NoBlackBoxes/LastBlackBox/boxes/magnets/README.md

# The Last Black Box : Magnets
In this box, you will learn about magnets...

<details><summary><i>Materials</i></summary><p>

Name|Description| # |Package|Data|Link|
:-------|:----------|:-----:|:-:|:--:|:--:|
Inductor|1 mH toroidal inductor|1|Passive Electronics|[-D-](/boxes/magnets/_resources/datasheets/inductor_toroidal.pdf)|[-L-](https://uk.farnell.com/bourns/2124-v-rc/inductor-1000uh-15-1-3a-toroid/dp/1929753)
Magnet Wire|Narrow gauge epoxy insulated (1 m)|1|Passive Electronics|[-D-](/boxes/magnets/)|[-L-](https://www.amazon.co.uk/sourcing-map-Enameled-Transformers-Inductors/dp/B0CYP8L4L1)
Magnet|Neodymium disc (8 mm x 3 mm)|4|Auxiliary|[-D-](/boxes/magnets/)|[-L-](https://uk.farnell.com/duratool/d01766/magnets-rare-earth-8-x-3mm-pk10/dp/1888095)
USB Sound Card|USB to 3.5 mm Audio out/in|1|Auxiliary|[-D-](/boxes/magnets/)|[-L-](https://www.amazon.co.uk/UGREEN-USB-C-3-5mm-Female-Adapter-dp-B08TR7LWQH/dp/B08TR7LWQH)
Stereo Plug Terminal|3.5 mm plug to screw terminal|2|Auxiliary|[-D-](/boxes/magnets/)|[-L-](https://www.amazon.co.uk/dp/B07MNYBFL9)

</p></details><hr>

## Magnets
#### Watch this video: [Ferromagnetism](https://vimeo.com/1031272573)
<p align="center">
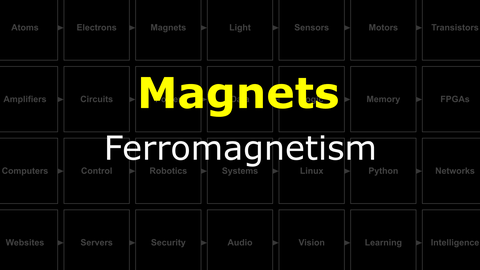
[picture p53: boxes/magnets/_resources/lessons/thumbnails/Ferromagnetism.gif]
Ferromagnetism

</p>

> A mysterious force found in certain types of "magical" materials, ferromagnetism was known about and used for thousands of years, but it was only understood quite recently.

#### Watch this video: [Electromagnets](https://vimeo.com/1031275874)
<p align="center">
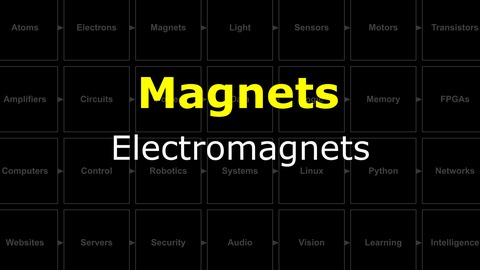
[picture p54: boxes/magnets/_resources/lessons/thumbnails/Electromagnets.gif]
Electromagnets

</p>

> When electrons move they create a (weak) magnetic field. With clever geometry we can make this field much, much stronger.

#### Watch this video: [Induction](https://vimeo.com/1031538232)
<p align="center">
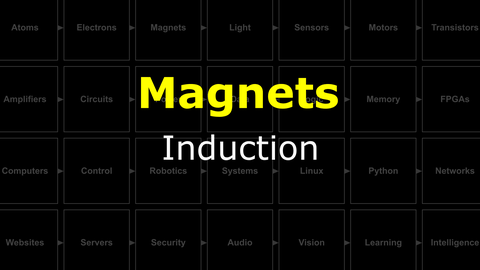
[picture p55: boxes/magnets/_resources/lessons/thumbnails/Induction.gif]
Induction

</p>

> A *changing* magnetic field **induces** an electromotive force on charged particles (and current in a complete conducting circuit). This electromagnetic induction is key to building time-dependent electronic circuits (such as filters) and generating the electricity we use in our homes.

# Projects
#### Watch this video: [NB3 : Building a Speaker](https://vimeo.com/1031277112)
<p align="center">
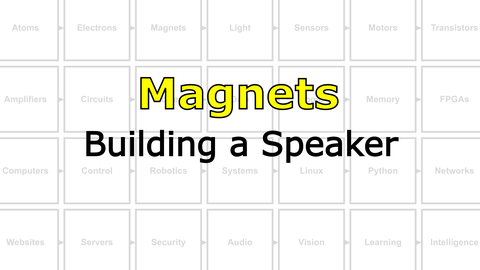
[picture p56: boxes/magnets/_resources/lessons/thumbnails/NB3_Building-a-Speaker.gif]
NB3 : Building a Speaker

</p>

> Oscillating current in a coil creates a dynamic magnetic field. Let's turn these oscillations into sound.
