NoBlackBoxes/LastBlackBox/boxes/motors/README.md

# The Last Black Box : Motors
In this box, you will learn about motors...

<details><summary><i>Materials</i></summary><p>

Name|Description| # |Package|Data|Link|
:-------|:----------|:-----:|:-:|:--:|:--:|
DC Brushed Motor|6V Brushed DC motor|1|Large (100)|[-D-](/boxes/motors/)|[-L-](https://www.amazon.co.uk/Gikfun-1V-6V-Hobby-Arduino-EK1894/dp/B07BHHP2BT)

</p></details><hr>

## Motors
#### Watch this video: [DC Motors](https://vimeo.com/1031627739)
<p align="center">
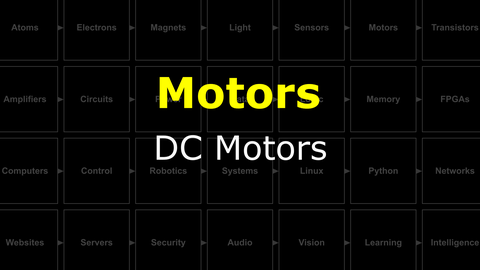
[picture p57: boxes/motors/_resources/lessons/thumbnails/DC-Motors.gif]
DC Motors

</p>

> An electric motor converts current into rotation using electromagnets that are turned on and off in a coordinated pattern. Different types of motors (stepper, brushed, or brushless) use different strategies (circuits) for this coordination.

- **TASK**: Play with your brushed DC motor. Spin it forwards *and* backwards...
    - *Challenge*: What are some ways you could change the *speed* with which your motor spins?
> Switching the direction that current flows through your motor will change the direction it spins.

# Projects
