NoBlackBoxes/LastBlackBox/boxes/sensors/README.md

# The Last Black Box : Sensors
In this box, you will learn about sensors...

<details><summary><i>Materials</i></summary><p>

Name|Description| # |Package|Data|Link|
:-------|:----------|:-----:|:-:|:--:|:--:|
Photoresistor (LDR)|Light-dependent resistor (GL5516 and GL5528)|2|Passive Electronics|[-D-](/boxes/sensors/)|[-L-](https://uk.farnell.com/advanced-photonix/nsl-19m51/light-dependent-resistor-550nm/dp/3168335)
Thermistor|Temperature sensitive resistor|1|Passive Electronics|[-D-](/boxes/sensors/_resources/datasheets/thermistor.pdf)|[-L-](https://uk.farnell.com/epcos/b57891m0103k000/thermistor-ntc-radial-leaded/dp/2285471)
Piezo|Piezo element|1|Passive Electronics|[-D-](/boxes/sensors/_resources/datasheets/piezo.pdf)|[-L-](https://uk.farnell.com/multicomp/mcabt-455-rc/audio-element-piezo-2-8khz-35mm/dp/2433035)

</p></details><hr>

## Sensors
#### Watch this video: [Transducers](https://vimeo.com/1031477896)
<p align="center">
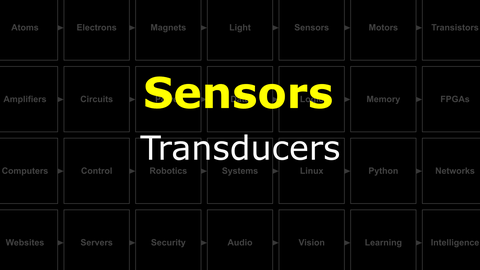
[picture p70: boxes/sensors/_resources/lessons/thumbnails/Transducers.gif]
Transducers

</p>

> A sensor converts (transduces) a physical quantity (light, heat, pressure, etc.) into an electrical signal (voltage, current, or resistance).

# Projects
#### Watch this video: [NB3 : Building a Light Sensor](https://vimeo.com/1031479533)
<p align="center">
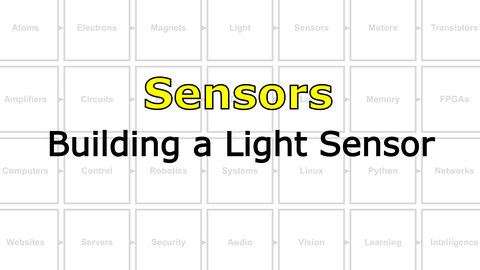
[picture p71: boxes/sensors/_resources/lessons/thumbnails/NB3_Building-a-Light-Sensor.gif]
NB3 : Building a Light Sensor

</p>

> Your NB3 will use LDRs to convert light into voltage. Here you will build and test this light sensing circuit.

- **TASK**: Build a light sensor
    - *Hint*: Build a voltage divider with one of the fixed resistors replaced with an LDR (light-dependent resistor). Does the "output" voltage vary with light level?
    - *Challenge*: What should the value of the fixed resistor be to maximize the sensitive range of the output voltage for varying light levels?
> Your multimeter should measure a change in voltage as you cover your LDR or shine light on it. The voltage will either increase with more light or decrease, depending on whether your LDR is the first or second resistor in the voltage divider circuit.

### NB3 : Sensory Systems
> What your NB3 "knows" about the world is up to you! Want touch sensitivity? temperature? You can add whatever you (and your robot) might like/need.
