NoBlackBoxes/LastBlackBox/boxes/transistors/README.md

# The Last Black Box : Transistors
In this box, you will learn about transistors...

<details><summary><i>Materials</i></summary><p>

Name|Description| # |Package|Data|Link|
:-------|:----------|:-----:|:-:|:--:|:--:|
MOSFET (5V)|Power MOSFET/N-channel (IRL510)|1|Active Electronics|[-D-](/boxes/transistors/_resources/datasheets/IRL510.pdf)|[-L-](https://uk.farnell.com/vishay/irl510pbf/mosfet-n-logic-to-220/dp/9102779)
Diode|IN4001|2|Active Electronics|[-D-](/boxes/transistors/_resources/datasheets/IN4001.pdf)|[-L-](https://uk.farnell.com/on-semiconductor/1n4001g/diode-standard-1a-do-41/dp/1458986)
LED (Red)|3 mm/2 mA red LED|2|Active Electronics|[-D-](/boxes/transistors/_resources/datasheets/led_HLMP.pdf)|[-L-](https://uk.farnell.com/broadcom-limited/hlmp-1700/led-3mm-red-2-1mcd-626nm/dp/1003207)
LED (Yellow)|3 mm/2 mA yellow LED|2|Active Electronics|[-D-](/boxes/transistors/_resources/datasheets/led_HLMP.pdf)|[-L-](https://uk.farnell.com/broadcom-limited/hlmp-1719/led-3mm-yellow-2-1mcd-585nm/dp/1003208)
LED (Green)|3 mm/2 mA green LED|2|Active Electronics|[-D-](/boxes/transistors/_resources/datasheets/led_HLMP.pdf)|[-L-](https://uk.farnell.com/broadcom-limited/hlmp-1790/led-3mm-green-2-3mcd-569nm/dp/1003209)
Resistor (470)|470 &Omega;/0.25 W|4|Passive Electronics|[-D-](/boxes/electrons/_resources/datasheets/resistor.pdf)|[-L-](https://uk.farnell.com/multicomp/mf25-470r/res-470r-1-250mw-axial-metal-film/dp/9341943)
Photodiode (Visible)|Visible (broadband) photodiode|2|Active Electronics|[-D-](/boxes/transistors/)|[-L-](https://uk.farnell.com/vishay/tefd4300/photodiode-950nm-3mm/dp/2251271)
Photodiode (IR)|IR sensitive photodiode|2|Active Electronics|[-D-](/boxes/transistors/)|[-L-](https://uk.farnell.com/osram-opto-semiconductors/sfh203-fa/photodiode-ir-filtered/dp/1212743)
LED (Blue)|Low power blue light emitting diode|2|Active Electronics|[-D-](/boxes/transistors/)|[-L-](https://uk.farnell.com/broadcom-limited/hlmp-ka45-e0000/led-3mm-blue-85mcd-470nm/dp/1863182)
LED (IR)|Low power IR light emitting diode|2|Active Electronics|[-D-](/boxes/transistors/)|[-L-](https://uk.farnell.com/vishay/tsal6100/infrared-emitter-940nm-t-1-3-4/dp/1328299)

</p></details><hr>

## Transistors
#### Watch this video: [Diodes](https://vimeo.com/1032443724)
<p align="center">
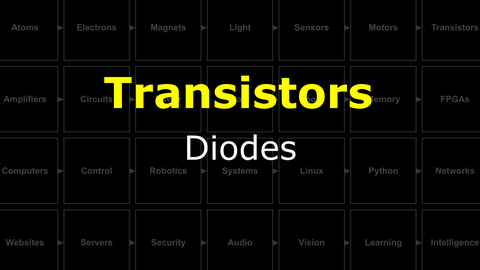
[picture p82: boxes/transistors/_resources/lessons/thumbnails/Diodes.gif]
Diodes

</p>

> The chemical and electrical equilibrium between charge carriers creates a potential across the PN junction. This junction potential only permits current flow in one direction, which gives **diodes** there delightfully non-linear behavior.

- **TASK**: Illuminate a light-emitting diode (LED). *Remember the current limiting resistor!*
> The LED should only illuminate when installed in one orientation. If you flip it around, then the "diode" of the LED will prevent current flowing through the circuit.

#### Watch this video: [Semiconductors](https://vimeo.com/1032460818)
<p align="center">
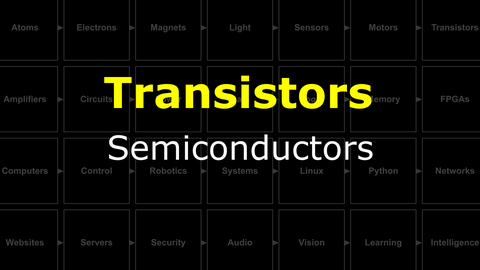
[picture p83: boxes/transistors/_resources/lessons/thumbnails/Semiconductors.gif]
Semiconductors

</p>

> We can modify a pure crystal of certain elements (e.g. silicon) to change how well they conduct electricity.

### Transistors (BJTs)
> Bipolar junction transistors inject charge carriers to amplify the external *current* flowing. They are current controlled devices.

#### Watch this video: [Transistors (MOSFETs)](https://vimeo.com/1032452466)
<p align="center">
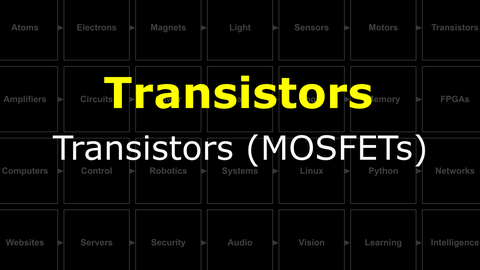
[picture p84: boxes/transistors/_resources/lessons/thumbnails/Transistors-MOSFETs.gif]
Transistors (MOSFETs)

</p>

> MOSFETs are the thing that humans have built more of than anything else. They must be useful! Let's discuss what they are and how they work.

- **TASK**: Measure the threshold voltage that opens your MOSFET gate. Compare it to the "expected" range listed in the
    - The datasheet for your MOSFET here [IRL510](/boxes/transistors/_resources/datasheets/IRL510.pdf)
> The threshold for when current starts to flow through your MOSFET ("Gate-Source Threshold Voltage") should be between 1 to 3 vols for the IRL510. However, the amount of current it allows will rise rapidly up to (and beyond) 5 Volts for the IRL510. Check the datasheet (Figure 3).

# Projects
#### Watch this video: [NB3 : Testing Diodes](https://vimeo.com/1032458879)
<p align="center">
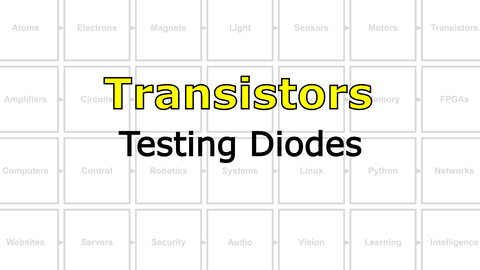
[picture p85: boxes/transistors/_resources/lessons/thumbnails/NB3_Testing-Diodes.gif]
NB3 : Testing Diodes

</p>

> Diodes allow current to flow in only one direction...if you overcome the internal junction potential. Let's measure this...and also use an LED to emit some light.

#### Watch this video: [NB3 : Building a Light-Sensitive Motor](https://vimeo.com/1032454998)
<p align="center">
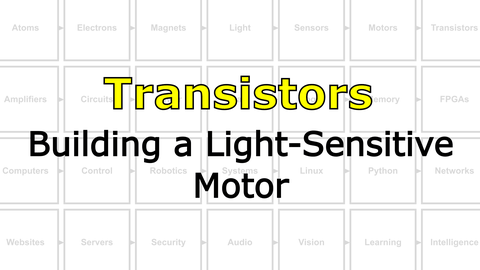
[picture p86: boxes/transistors/_resources/lessons/thumbnails/NB3_Building-a-Light-Sensitive-Motor.gif]
NB3 : Building a Light-Sensitive Motor

</p>

> Let's make something move in response to light!

- **TASK**: Use a MOSFET transistor to control how much current is flowing through your motor and gate the MOSFET with the output voltage from your light sensor...creating a motor that spins when the light is **ON** and stops when the light is **OFF**, or the other way around.
- *Hint*: Use the following circuit as a guide: [MOSFET driver:400](/boxes/transistors/_resources/images/MOSFET_motor_driver.png)
> Your motor should change how fast it spins when you change how much light hits the LDR.
