NoBlackBoxes/LastBlackBox/boxes/amplifiers/README.md

# The Last Black Box : Amplifiers
In this box, you will learn about amplifiers...

<details><summary><i>Materials</i></summary><p>

Name|Description| # |Package|Data|Link|
:-------|:----------|:-----:|:-:|:--:|:--:|
LM741|OpAmp|1|Active Electronics|[-D-](/boxes/amplifiers/_resources/datasheets/LM741.pdf)|[-L-](https://uk.farnell.com/texas-instruments/lm741cn-nopb/op-amp-single-pdip-8-0-to-70deg/dp/3117118)
LM386|Audio-Amp|2|Active Electronics|[-D-](/boxes/amplifiers/_resources/datasheets/LM386.pdf)|[-L-](https://uk.farnell.com/texas-instruments/lm386n-4-nopb/audio-power-amplifier-class-ab/dp/3116866)

</p></details><hr>

## Amplifiers
### Differential Amplifier
> Signals often have noise. However, this noise is often the same in many places around our circuit. What if we could reject (subtract out) this common noise? A differential amplifier allows us to selectively amplify the difference between a signal (with noise) and background (just noise). They are *very* useful.

### Op Amps
> Combine *high gain differential amplification* with *negative feedback* to build a much, much better amplifier. We call these devices **operational amplifiers** or **Op Amps**.

- Use an OpAmp to make your DIY speaker louder!

# Projects
