NoBlackBoxes/LastBlackBox/boxes/circuits/README.md

# The Last Black Box : Circuits
In this box, you will learn about circuits...

<details><summary><i>Materials</i></summary><p>

Name|Description| # |Package|Data|Link|
:-------|:----------|:-----:|:-:|:--:|:--:|

</p></details><hr>

## Circuits
### Radios
> Let's make some light, send it across the room, and decode it into a useful signal.

# Projects
