NoBlackBoxes/LastBlackBox/boxes/fpgas/README.md

# The Last Black Box : FPGAs
In this box, you will learn about fpgas...

<details><summary><i>Materials</i></summary><p>

Name|Description| # |Package|Data|Link|
:-------|:----------|:-----:|:-:|:--:|:--:|
NB3 Hindbrain|ICE40UP5K dev board with ADC/DAC|1|Circuit Boards|[-D-](/boxes/fpgas/NB3_hindbrain)|[-L-](VK)
Cable (MicroUSB-1m)|Micro-USB to Type-A cable (1 m)|1|Cables (001)|[-D-](/boxes/fpgas/)|[-L-](https://www.amazon.co.uk/gp/product/B07GBCKX49)
Cable (MicroUSB-20cm)|Short micro-USB to Type-A cable (20 cm)|1|Cables (001)|[-D-](/boxes/networks/)|[-L-](https://www.amazon.co.uk/gp/product/B07GBS2QZ1)

</p></details><hr>

## FPGAs
### Hardware Description Languages
> Describing hardware layouts is very different than describing software algorithms. Hardware description languages allow you to describe precisely what pieces of transistor logic you want. They come in many flavours, but the most popular are **Verilog** and **VHDL**.

# Projects
