NoBlackBoxes/LastBlackBox/course/tools/README.md

# course : tools
Tools to generate LBB designs, material lists, video lists, and run the README template engine
