NoBlackBoxes/LastBlackBox/boxes/ics/README.md

# FPGAs

Field-programmable-gate-arrays-are-awesome.

----

<details><summary><b>Materials</b></summary><p>

Contents|Description| # |Data|Link|
:-------|:----------|:-:|:--:|:--:|
UpDuino|ICE40UP5K dev board|1|[-D-](_data/datasheets/arduino_nano_rev3.pdf)|[-L-](https://uk.farnell.com/arduino/a000005/arduino-nano-evaluation-board/dp/1848691)
Cable (MiniUSB-1m)|Mini-USB to Type-A cable (1 m)|1|[-D-](_data/datasheets/mini_USB_cable_1m.pdf)|[-L-](https://uk.farnell.com/molex/88732-8602/usb-cable-2-0-plug-plug-1m/dp/1221071)
Piezo Buzzer|Piezoelectric speaker/buzzer|1|[-D-](_data/datasheets/piezo_speaker.pdf)|[-L-](https://uk.farnell.com/kingstate/kpeg110/piezo-transducer/dp/1193641)

</p></details>

----

## Goals

### Grey

1. Setup your FPGA dev board (run "blink" example).
2. Design a counter in HDL, synthesize, and test.
3. Design a 4-bit adder in HDL, synthesisze, and test.
4. Design a PWM controller in HDL, synthesisze, and test.

### White

1. Design a (RISC-V: rv32i) CPU

----

## NB3

This box will contribute the following (red) components to your NB3

<p align="center">
NB3 stage
<p>

----
