NoBlackBoxes/LastBlackBox/boxes/vision/image_processing/README.md

# Vision : Image Processing

This directory contains image processing examples and tools for computer vision tasks.

## Subdirectories

- **`python/`** - Python scripts for image processing (offline and online/streaming)
- **`picamera/`** - Information about using picamera2 library with libcamera

## Quick Start

**⚠️ Setup Required**: Before running the scripts, make sure you have activated your Python environment (or set one up). Follow the [Virtual Environment Setup Guide](../../python/virtual_environments/README.md) if needed.

### Python Dependencies

**Note**: Make sure you have activated the LBB virtual environment before installing packages:
```bash
source ~/NoBlackBoxes/LastBlackBox/_tmp/LBB/bin/activate
```

Then install the required packages:
```bash
pip install opencv-python
pip install numpy==1.26       # OpenCV is currently forcing numpy version >2 (which breaks other things)
```

### Camera Support

- **NB3/Raspberry Pi**: Uses picamera2 library (pre-installed on Raspberry Pi OS)
- **PC/Development**: Falls back to webcam support

See the individual subdirectory READMEs for detailed documentation:
- [`python/README.md`](python/README.md) - Python scripts documentation
- [`picamera/README.md`](picamera/README.md) - picamera2 information
