NoBlackBoxes/LastBlackBox/course/tools/videos/README.md

# course : tools : videos
Generate the LBB video list (with links), thumbnail frames, and GIF summary clips

## Normalize Audio
Use FFMPEG's loudnorm filter (via a Python wrapper: https://github.com/slhck/ffmpeg-normalize/tree/master)

```bash
# Requires an installation of FFMPEG
pip install ffmpeg-normalize

# Usage
ffmpeg-normalize -p -v -f -c:a aac -b:a 320k -t -16 --keep-loudness-range-target <filename.mkv>

# Detect volume levels
ffmpeg -filter:a ebur128 -map 0:a -f null - -i <filename.mkv>

## Integrated loudness should be around -16 LUFS
```
