NoBlackBoxes/LastBlackBox/boxes/electrons/kicad/README.md

# Electrons : KiCAD
KiCad is an open-course, highly capable, Python-based printed circuit board (PCB) design software

## JLC to KICAD
The following library coverts JLC/LCSC footprints/schematics/models into KiCAD footprints/schematics/models based on the part number.

```bash
pip install JLC2KiCadLib
```
