NoBlackBoxes/LastBlackBox/boxes/networks/sockets/README.md

# Python : Sockets
Instructions for developing socket-based network applications in Python.

## Setup
- Upload the "analog_stream" sketch to your Arduino
- Run the server on your NB3
- Run one of the clients (text, Matplotlib plotting (slow), OpenGL plotting (fast))
