NoBlackBoxes/LastBlackBox/boxes/vision/drone-NB3/README.md

# Vision : Drone NB3
Stream live camera images from the NB3 camera and provide web form input controls for driving the NB£ with a first-person view (FPV).
