NoBlackBoxes/LastBlackBox/boxes/light/equations/README.md

# Light : equations

Maxwell-Heaviside equations explained and demonstrated.

$$
\begin{align}
  \nabla \cdot  \vec{E} &= \frac{\rho} {\epsilon_0} \nonumber \\
  \nabla \cdot  \vec{B} &= 0 \nonumber \\
  \nabla \times \vec{E} &= - \frac{\partial \vec{B}}{\partial t} \nonumber \\
  \nabla \times \vec{B} &= \mu_0 ( \vec{j} + \frac{\partial \vec{E}}{\partial t} ) \nonumber \\
\end{align}
$$

---

## Gauss's Law for Electricity
$$
\begin{align}
  \nabla \cdot \vec{E} &= \frac{\rho} {\epsilon_0} \nonumber \\
\end{align}
$$

The electric field points towards negative charges and away from positive charges.  $\rho$ is charge density and $\epsilon_0$ is the permitivity of free space.

## Gauss's Law for Magnetisim
$$
\begin{align}
  \nabla \cdot  \vec{B} &= 0 \nonumber \\
\end{align}
$$

There are no magnetic dipoles (i.e. no net inward or outward magentic field lines).

## Faraday's Law of Induction
$$
\begin{align}
  \nabla \times \vec{E} &= - \frac{\partial \vec{B}}{\partial t} \nonumber \\
\end{align}
$$

Induced electric field (also EMF) is related to the rate of change of a magentic field.

## Ampere's Law
$$
\begin{align}
  \nabla \times \vec{B} &= \mu_0 ( \vec{j} + \frac{\partial \vec{E}}{\partial t} ) \nonumber \\
\end{align}
$$

Induced magnetic field is related to the rate of change of an electric field field + current density $\vec(j)$ scaled by $\mu_0$, the permeability of free space. (hmm....more to this...)
