NoBlackBoxes/LastBlackBox/boxes/servers/node/README.md

# Servers : Node

There is a lot to say about Node.js, but not yet. This section is currently only used to introduce the framework for developing a VSCode extension.
