NoBlackBoxes/LastBlackBox/course/versions/crick/01_electronics-and-sensors/README.md

# Crick : Electronics and Sensors
Day one of the NB3 build is entirely analog - no microcontroller, no software, no code. By the end of the session you will have built a working light sensor (LDR voltage divider), a hand-wound electromagnetic speaker, and a fully analog light-sensitive motor with a MOSFET as the only computational element.

<details><summary><i>Materials</i></summary><p>

Name|Description| # |Package|Data|Link|
:-------|:----------|:-----:|:-:|:--:|:--:|
Periodic Table|Periodic Table Card|1|Body (000)|[-D-](/boxes/atoms/card)|[-L-](VK)
NB3 Body|NB3 robot base PCB|1|Body (000)|[-D-](/boxes/electrons/NB3_body)|[-L-](VK)
Resistor (470)|470 &Omega;/0.25 W|2|Passive Electronics|[-D-](/boxes/electrons/_resources/datasheets/resistor.pdf)|[-L-](https://uk.farnell.com/multicomp/mf25-470r/res-470r-1-250mw-axial-metal-film/dp/9341943)
Resistor (1k)|1 k&Omega;/0.25 W|2|Passive Electronics|[-D-](/boxes/electrons/_resources/datasheets/resistor.pdf)|[-L-](https://uk.farnell.com/multicomp/mf25-1k/res-1k-1-250mw-axial-metal-film/dp/9341102)
Resistor (10k)|10 k&Omega;/0.25 W|2|Passive Electronics|[-D-](/boxes/electrons/_resources/datasheets/resistor.pdf)|[-L-](https://uk.farnell.com/multicomp/mf25-10k/res-10k-1-250mw-axial-metal-film/dp/9341110)
Button|Tactile switch|2|Passive Electronics|[-D-](/boxes/electrons/_resources/datasheets/button.pdf)|[-L-](https://uk.farnell.com/omron/b3f-1000/switch-spno-0-05a-24v-tht-0-98n/dp/176432)
Potentiometer|2.2 k&Omega; variable resistor|2|Passive Electronics|[-D-](/boxes/electrons/_resources/datasheets/pot_2k2.pdf)|[-L-](https://uk.farnell.com/bourns/3362p-1-222lf/trimmer-pot-2-2kohm-10-1turn-th/dp/2328599)
Breadboard (400)|400-tie solderless breadboard|1|Small (010)|[-D-](/boxes/electrons/_resources/datasheets/breadboard_400.pdf)|[-L-](https://www.amazon.co.uk/gp/product/B0739XRX8F)
Breadboards (170)|170-tie solderless breadboard|4|Small (010)|[-D-](/boxes/electrons/_resources/datasheets/breadboard_170.pdf)|[-L-](https://www.amazon.co.uk/ELEGOO-tie-points-Breadboard-Breadboards-Electronic/dp/B01N0YWIR7)
Batteries (AA)|AA 1.5 V alkaline battery|4|Auxiliary|[-D-](/boxes/electrons/)|[-L-](https://www.amazon.co.uk/Duracell-Optimum-Alkaline-Batteries-MX1500/dp/B093Q5XY66)
Battery holder|4xAA battery holder with ON-OFF switch|1|Small (010)|[-D-](/boxes/electrons/)|[-L-](https://www.amazon.co.uk/gp/product/B0814ZH68F)
Jumper Kit|Kit of multi-length 22 AWG breadboard jumpers|1|Large (100)|[-D-](/boxes/electrons/_resources/datasheets/jumper_kit.pdf)|[-L-](https://uk.farnell.com/multicomp/mc001810/hard-jumper-wire-22awg-140pc/dp/2770338)
Jumper Wires|Assorted 22 AWG jumper wire leads (male/female)|1|Cables (001)|[-D-](/boxes/electrons/_resources/datasheets/jumper_wires.pdf)|[-L-](https://www.amazon.co.uk/gp/product/B09KR7Z4PF)
Test Lead|Alligator clip to 0.64 mm pin (20 cm)|2|Cables (001)|[-D-](/boxes/electrons/)|[-L-](https://www.amazon.co.uk/gp/product/B096JR15JW)
Rubber feet|Adhesive rubber standoffs (1421T6CL)|4|Passive Electronics|[-D-](/boxes/electrons/_resources/datasheets/rubber_feet.pdf)|[-L-](https://uk.farnell.com/hammond/1421t6cl/feet-stick-on-pk24/dp/1876522)
Photoresistor (LDR)|Light-dependent resistor (GL5516 and GL5528)|2|Passive Electronics|[-D-](/boxes/sensors/)|[-L-](https://uk.farnell.com/advanced-photonix/nsl-19m51/light-dependent-resistor-550nm/dp/3168335)
DC Brushed Motor|6V Brushed DC motor|1|Large (100)|[-D-](/boxes/motors/)|[-L-](https://www.amazon.co.uk/Gikfun-1V-6V-Hobby-Arduino-EK1894/dp/B07BHHP2BT)
MOSFET (5V)|Power MOSFET/N-channel (IRL510)|1|Active Electronics|[-D-](/boxes/transistors/_resources/datasheets/IRL510.pdf)|[-L-](https://uk.farnell.com/vishay/irl510pbf/mosfet-n-logic-to-220/dp/9102779)
Diode|IN4001|2|Active Electronics|[-D-](/boxes/transistors/_resources/datasheets/IN4001.pdf)|[-L-](https://uk.farnell.com/on-semiconductor/1n4001g/diode-standard-1a-do-41/dp/1458986)
LED (Red)|3 mm/2 mA red LED|2|Active Electronics|[-D-](/boxes/transistors/_resources/datasheets/led_HLMP.pdf)|[-L-](https://uk.farnell.com/broadcom-limited/hlmp-1700/led-3mm-red-2-1mcd-626nm/dp/1003207)
LED (Yellow)|3 mm/2 mA yellow LED|2|Active Electronics|[-D-](/boxes/transistors/_resources/datasheets/led_HLMP.pdf)|[-L-](https://uk.farnell.com/broadcom-limited/hlmp-1719/led-3mm-yellow-2-1mcd-585nm/dp/1003208)
LED (Green)|3 mm/2 mA green LED|2|Active Electronics|[-D-](/boxes/transistors/_resources/datasheets/led_HLMP.pdf)|[-L-](https://uk.farnell.com/broadcom-limited/hlmp-1790/led-3mm-green-2-3mcd-569nm/dp/1003209)
Resistor (470)|470 &Omega;/0.25 W|4|Passive Electronics|[-D-](/boxes/electrons/_resources/datasheets/resistor.pdf)|[-L-](https://uk.farnell.com/multicomp/mf25-470r/res-470r-1-250mw-axial-metal-film/dp/9341943)
Magnet Wire|Narrow gauge epoxy insulated (1 m)|1|Passive Electronics|[-D-](/boxes/magnets/)|[-L-](https://www.amazon.co.uk/sourcing-map-Enameled-Transformers-Inductors/dp/B0CYP8L4L1)
Magnet|Neodymium disc (8 mm x 3 mm)|4|Auxiliary|[-D-](/boxes/magnets/)|[-L-](https://uk.farnell.com/duratool/d01766/magnets-rare-earth-8-x-3mm-pk10/dp/1888095)
USB Sound Card|USB to 3.5 mm Audio out/in|1|Auxiliary|[-D-](/boxes/magnets/)|[-L-](https://www.amazon.co.uk/UGREEN-USB-C-3-5mm-Female-Adapter-dp-B08TR7LWQH/dp/B08TR7LWQH)
Stereo Plug Terminal|3.5 mm plug to screw terminal|2|Auxiliary|[-D-](/boxes/magnets/)|[-L-](https://www.amazon.co.uk/dp/B07MNYBFL9)

</p></details><hr>

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

## Voltage, current, resistance
#### Watch this video: [Voltage](https://vimeo.com/1000730032)
<p align="center">
<a href="https://vimeo.com/1000730032" title="Control+Click to watch in new tab">Voltage</a>
</p>

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

## Building circuits
#### Watch this video: [NB3 : Body](https://vimeo.com/1030776673)
<p align="center">
<a href="https://vimeo.com/1030776673" title="Control+Click to watch in new tab">NB3 : Body</a>
</p>

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

## Voltage dividers and transduction
#### Watch this video: [Voltage Dividers](https://vimeo.com/1030787469)
<p align="center">
<a href="https://vimeo.com/1030787469" title="Control+Click to watch in new tab">Voltage Dividers</a>
</p>

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

> Step-by-step guide to building and testing voltage dividers with discrete resistors and a potentiometer.

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

## Semiconductors and the MOSFET
#### Watch this video: [Semiconductors](https://vimeo.com/1032460818)
<p align="center">
<a href="https://vimeo.com/1032460818" title="Control+Click to watch in new tab">Semiconductors</a>
</p>

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

# Project
#### Watch this video: [NB3 : Building a Speaker](https://vimeo.com/1031277112)
<p align="center">
<a href="https://vimeo.com/1031277112" title="Control+Click to watch in new tab">NB3 : Building a Speaker</a>
</p>

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

> Let's make something move in response to light!

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
