NoBlackBoxes/LastBlackBox/course/versions/bootcamp/08_signal-processing/README.md

# Bootcamp : Signal Processing
Let's learn how to process one-dimensional time series data...like audio waveforms.

<details><summary><i>Materials</i></summary><p>

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

</p></details><hr>

## Audio
We will continue our explanation of sound measurement and generation by exploring "signal processing" in Python.
#### Watch this video: [Signal Processing](https://vimeo.com/manage/videos/1139975157)
<p align="center">
<a href="https://vimeo.com/manage/videos/1139975157" title="Control+Click to watch in new tab">Signal Processing</a>
</p>

> One-dimensional (1D) signals are common in the world. They often arise as time series (a sequence of measurements made at a regular "sample rate"). Here we will explore techniques to process a common 1D signal...**sound**. We will both measure and generate different sounds. We will develop tools in Python to compare their amplitude (volume), frequency content, and visualize the "spectrogram" of different spoken words (e.g. "Go" vs "Stop").

- Explore, test, and expand upon these Python examples for processing signals measured from the NB3's microphones (ears): [Measurement](/boxes/audio/signal-processing/python/measurement/)
    - Stream the live frequency spectrum from your NB3 to your PC.
        - Run the [server](/boxes/audio/signal-processing/python/measurement/03_stream_frequency.py) on your NB3 (via SSH)
        - Run the [client](/boxes/audio/signal-processing/python/measurement/clients/live_plot_frequency_client_pyglet.py) on your PC (in a separate VS Code window)
- Explore, test, and expand upon these Python examples for processing signals generated and output to the NB3's speaker (mouth): [Generation](/boxes/audio/signal-processing/python/generation/)
    - *Note*: For text-to-speech synthesis you will need to install the Linux espeak package:
- *code*
```bash
sudo apt install espeak-ng
```

# Project
You should now have all the skills required to make your NB3 "respond" to sound!
  - This could be as simple as detecting a loud ***clap*** and turning on an LED.
  - You could tell NB3 to turn left or right based on the most prominent frequency measured by its ears.
  - Respond to commands, like "Go" and "Stop"...tricky...but doable.
    - *Note*: We will revisit this when we start learning about learning.
