NoBlackBoxes/LastBlackBox/course/_resources/videos/list.md

## Atoms
- [x] [The Periodic Table](https://vimeo.com/1028399080)
- [ ] [Chemistry]()
- [ ] [Nuclear Forces]()
- [x] [Heat](https://vimeo.com/1029691491)
- [x] [Atomic Structure](https://vimeo.com/1000458082)
- [ ] [Fission and Fusion]()

## Electrons
- [x] [NB3 : Multimeter Basics](https://vimeo.com/1027764019)
- [x] [Voltage Dividers](https://vimeo.com/1030787469)
- [x] [NB3 : Body](https://vimeo.com/1030776673)
- [ ] [NB3 : Designing PCBs With KiCAD]()
- [x] [NB3 : Measuring Resistance](https://vimeo.com/1027761453)
- [x] [NB3 : Building Circuits](https://vimeo.com/1030783826)
- [x] [NB3 : Building Voltage Dividers](https://vimeo.com/1030790826)
- [x] [Electric Fields](https://vimeo.com/1032441712)
- [x] [Capacitors](https://vimeo.com/1035298931)
- [x] [Resistors](https://vimeo.com/1029696806)
- [x] [NB3 : Measuring Current](https://vimeo.com/1027757287)
- [x] [Current](https://vimeo.com/1029334167/2492ff3542)
- [x] [Ohm's Law](https://vimeo.com/1029695302)
- [ ] [NB3 : How Do Multimeters Work]()
- [x] [Power](https://vimeo.com/1029693122)
- [x] [NB3 : Measuring Voltage](https://vimeo.com/1027762531)
- [x] [Batteries](https://vimeo.com/1029278169)
- [x] [NB3 : Building a Battery](https://vimeo.com/1029280971)
- [x] [Conductors](https://vimeo.com/1029337222)
- [x] [Voltage](https://vimeo.com/1000730032)

## Magnets
- [x] [NB3 : Building a Speaker](https://vimeo.com/1031277112)
- [x] [Ferromagnetism](https://vimeo.com/1031272573)
- [x] [Electromagnets](https://vimeo.com/1031275874)
- [x] [Induction](https://vimeo.com/1031538232)

## Light
- [ ] [The EM Spectrum]()
- [ ] [Optics]()
- [ ] [Maxwell's Equations]()
- [x] [Electromagnetic Radiation](https://vimeo.com/1032447600)

## Sensors
- [x] [Transducers](https://vimeo.com/1031477896)
- [ ] [NB3 : Sensory Systems]()
- [x] [NB3 : Building a Light Sensor](https://vimeo.com/1031479533)

## Motors
- [x] [DC Motors](https://vimeo.com/1031627739)

## Transistors
- [ ] [Transistors (BJTs)]()
- [x] [Diodes](https://vimeo.com/1032443724)
- [x] [Semiconductors](https://vimeo.com/1032460818)
- [x] [NB3 : Building a Light-Sensitive Motor](https://vimeo.com/1032454998)
- [x] [Transistors (MOSFETs)](https://vimeo.com/1032452466)
- [x] [NB3 : Testing Diodes](https://vimeo.com/1032458879)

## Amplifiers
- [ ] [Differential Amplifier]()
- [ ] [Op Amps]()

## Circuits
- [ ] [Radios]()

## Data
- [x] [Analog to Digital Converters](https://vimeo.com/1033223967)
- [x] [Binary Numbers](https://vimeo.com/1033226788)
- [x] [NB3 : Build an ADC (input)](https://vimeo.com/1034767170)

## Logic
- [x] [Logic Gates](https://vimeo.com/1033231995)
- [ ] [NB3 : Build an ADC (output)]()

## Memory
- [x] [Flash Memory](https://vimeo.com/1033230293)
- [x] [NB3 : Building an SR Latch](https://vimeo.com/1033234541)
- [ ] [Flip Flop]()
- [x] [SR Latch](https://vimeo.com/1033238234)

## FPGAs
- [ ] [Hardware Description Languages]()

## Computers
- [x] [Architecture](https://vimeo.com/1033601146)
- [x] [NB3 : Hindbrain](https://vimeo.com/1033609727)
- [ ] [Low-Level Programming]()
- [x] [NB3 : Building a Theremin](https://vimeo.com/1033896646)
- [x] [NB3 : Programming Arduino](https://vimeo.com/1033810807)

## Control
- [x] [PWM](https://vimeo.com/1033905955)
- [x] [Servo Loops](https://vimeo.com/1033963709)
- [x] [NB3 : Building a PWM Speed Controller](https://vimeo.com/1033891821)
- [x] [H-Bridges](https://vimeo.com/1034209519)

## Robotics
- [ ] [NB3 : Muscles (DC Gear Motors)]()
- [ ] [Reflexes]()
- [x] [NB3 : Muscles (Servos)](https://vimeo.com/1034800702)
- [x] [NB3 : Build a Braitenberg Vehicle](https://vimeo.com/1034798460)
- [x] [NB3 : Ball Caster](https://vimeo.com/1034797327)

## Power
- [x] [NB3 : Power Supply](https://vimeo.com/1035306761)
- [x] [NB3 : Battery Pack](https://vimeo.com/1042781111)
- [x] [DC-DC Converters](https://vimeo.com/1035304311)

## Systems
- [x] [NB3 : Programming Concurrency (Arduino)](https://vimeo.com/1036094397)
- [x] [Operating Systems](https://vimeo.com/1036096746)
- [x] [NB3 : Connecting to RPi](https://vimeo.com/1036391512)
- [x] [NB3 : Midbrain](https://vimeo.com/1036089510)
- [x] [Visual Studio Code](https://vimeo.com/1036716612)
- [x] [Multi-Tasking](https://vimeo.com/1036086160)
- [x] [NB3 : RPiOS](https://vimeo.com/1036095710)

## Linux
- [x] [Package Managers](https://vimeo.com/1036834036)
- [x] [Navigating the Command Line](https://vimeo.com/1036829527)
- [x] [Git](https://vimeo.com/1036825331)

## Python
- [x] [Virtual Environments](https://vimeo.com/1042637566)
- [x] [Introducing the Interpreter](https://vimeo.com/1042618092)
- [ ] [NB3 : Playing With Python]()

## Networks
- [x] [NB3 : Remote Control NB3 (TUI)](https://vimeo.com/1042784651)
- [x] [Sockets](https://vimeo.com/1134201413)
- [x] [Architectures](https://vimeo.com/manage/videos/1127222969)
- [x] [Physical Layers](https://vimeo.com/1127178041)
- [x] [NB3 : Develop a Protocol](https://vimeo.com/1042782602)

## Websites
- [x] [Javascript](https://vimeo.com/1134729863)
- [x] [HTML](https://vimeo.com/1134724080)
- [x] [CSS](https://vimeo.com/1134720724)

## Servers
- [x] [NB3 : Remote Control NB3 (GUI)](https://vimeo.com/1135870296)
- [x] [NB3 : Host a Website](https://vimeo.com/1135859914)
- [x] [HTTP](https://vimeo.com/1135853103)

## Security
- [ ] [One Way Functions]()

## Audio
- [x] [NB3 : Install the Mouth](https://vimeo.com/1042947561)
- [x] [NB3 : Install the Ears](https://vimeo.com/1042943195)
- [x] [NB3 : Build and Install the Linux I2S Driver](https://vimeo.com/1042781850)
- [x] [Microphones, Speakers, and I2S](https://vimeo.com/1136576333)
- [x] [Signal Processing](https://vimeo.com/manage/videos/1139975157)

## Vision
- [x] [NB3 : Streaming Images](https://vimeo.com/manage/videos/1141582696)
- [x] [Light, Cameras, Noise](https://vimeo.com/manage/videos/1141367902)
- [x] [Image-Processing](https://vimeo.com/manage/videos/1144050570)
- [x] [NB3 : Install the Eye](https://vimeo.com/1042945461)

## Learning
- [ ] [NB3 : Clicker Training]()
- [ ] [Gradient Descent]()

## Intelligence
- [ ] [Large Language Models]()
- [x] [NB3 : Install the Forebrain (NPU)](https://vimeo.com/1043159124)
- [ ] [NB3 : Install the Skull]()
