NoBlackBoxes/LastBlackBox/boxes/circuits/_resources/info.md

## Description
Analog circuits can do some amazing things. Here we will build a radio (receiver and transmitter).
