NoBlackBoxes/LastBlackBox/boxes/power/_resources/info.md

## Description
Running more capable software requires a faster computer, which requires more electrical power. We will now explore how power supplies work and then install one on your NB3.
