NoBlackBoxes/LastBlackBox/boxes/control/_resources/info.md

## Description
Getting a motor to move precisely how you want it to (direction and speed) is very important for *controlling* the behaviour of your robot. A number of very clever strategies have been developed to help you take **control** of your motor.
