NoBlackBoxes/LastBlackBox/boxes/robotics/_resources/info.md

## Description
Combining sensors, motors, and a "brain" in between.
