NoBlackBoxes/LastBlackBox/boxes/amplifiers/_resources/info.md

## Description
The signals arriving from the environment are often too small to measure reliably with a computer (or brain). We need to make them bigger. Making tiny voltage or current signals larger is called *amplification*, and the things that can do this are ***amplifiers***.
