NoBlackBoxes/LastBlackBox/boxes/data/_resources/info.md

## Description
What is a data...for computers? for brains? How can machines decide what to do based on their inputs? A key concept in decision-making is threshold functions. If an input value goes above a threshold, a decision is triggered. How can we make such a trigger out of electronic circuit elements?
