NoBlackBoxes/LastBlackBox/boxes/electrons/_resources/info.md

## Description
Electrons are the sub-atomic particles that underlie *electricity*. Controlling the movement of electrons (and the effects of that movement) will allow us to build many different kinds of electronic devices, from simple circuits to robots and computers.
