NoBlackBoxes/LastBlackBox/boxes/magnets/_resources/info.md

## Description
Magnets were known about (and useful) long before we understood electricity. However, the connection between electricity and magnetism is one of the most important discoveries of science. It has major implications for your everyday life (and your NB3).
