NoBlackBoxes/LastBlackBox/boxes/motors/_resources/info.md

## Description
Clever arrangements of electromagnets and their control circuits can be used to produce a rotational force. You will use these devices to make your NB3 move!
