NoBlackBoxes/LastBlackBox/boxes/transistors/_resources/info.md

## Description
Semiconductors are materials that can both conduct and resist the flow of electrons. You can arrange them such that the conduction of (lots of) electricity can be controlled by a (tiny) external signal. These devices are call **transistors**.
