NoBlackBoxes/LastBlackBox/boxes/vision/_resources/lessons/NB3_Streaming-Images.md

# Vision : NB3 : Streaming Images
Let's stream live images from your NB3's camera to any web browser.

## [Video](https://vimeo.com/manage/videos/1141582696)

## Concepts

## Lesson
