NoBlackBoxes/LastBlackBox/boxes/logic/_resources/lessons/Logic-Gates.md

# Logic : Logic Gates
The essential elements of computation (NOT, AND, OR, XOR, etc.) can be built from straight forward combinations of MOSFETs.

## [Video](https://vimeo.com/1033231995)

## Concepts
- MOSFETs make it easy.
- Inverter
- NAND (and AND)
- NOR
- Addition
- XOR?

## Lesson
- Design an XOR gate
- Build an addition circuit (2-bit adder)
- Build a priority encoder for your 2-bit ADC
