NoBlackBoxes/LastBlackBox/boxes/vision/_resources/lessons/Cameras.md

# Vision : Cameras
From CCDs to CMOS.

## [Video]()

## Concepts

## Lesson
