NoBlackBoxes/LastBlackBox/boxes/networks/_resources/lessons/Physical-Layers.md

# Networks : Physical Layers
Connections must be made between computers in order for them to communicate. These can be wires carrying electrical signals (from just one or two wires for serial connections to many wires for parallel connections) or wireless (most often using light, i.e. radio waves). This is the physical layer of the network...and a message may traverse many different types of physical connections on its path from the sender to the receiver.

## [Video](https://vimeo.com/1127178041)

## Concepts
 - serial connections (simplex/duplex?, synchronous (with clock, e.g. SPI (with chip select...master/slave)) or asynchronous (UART, Rx/Tx, frames), baud-rate (BPS))
 - twisted-pair, deal with noise - differential signalling
 - Ethernet (four twisted-pairs: RJ45)
 - WiFi

## Lesson
