NoBlackBoxes/LastBlackBox/boxes/systems/_resources/lessons/NB3_Midbrain.md

# Systems : NB3 : Midbrain
Now we will add a more powerful computer (Raspberry Pi) to your NB3's midbrain.

## [Video](https://vimeo.com/1036089510)

## Concepts
- Overview of Pi SoC
- Overview of Pi board layout
- Mount Midbrain
- Attach heatsinks

## Lesson

- **TASK**: Mount a Raspberry Pi on your robot (and connect its power inputs using your *shortest* jumper cables, 2x5V and 2x0V from the NB3, to the correct GPIO pins on the RPi...please *double-check* the pin numbers)
    - This pinout of the Raspberry Pi GPIO might be useful: [Raspberry Pi GPIO](/boxes/systems/_resources/images/rpi_GPIO_pinout.png)
> A powered and blinking RPi midbrain.
