NoBlackBoxes/LastBlackBox/boxes/systems/_resources/lessons/Visual-Studio-Code.md

# Systems : Visual Studio Code
We will be using Visual Studio Code (VS Code) as our tool for writing programs. VS Code is just a simple, *but really powerful*, text editor. It has extensions for all sorts of useful tools (Python, Git, etc.), and for connecting to a "remote" computer (our NB3's midbrain).

## [Video](https://vimeo.com/1036716612)

## Concepts
- Managing complex, powerful systems requires more complex, powerful tools
- Fortunately, the basics are pretty standardized: Run commands, browse folders, and edit files
- VS Code, simple, but extensible (runs in a browser framework  electron, based on Chrome)
- Overview: Terminal, Explorer, Editor, and Search
- Workflow: Open a project folder
- Extensions
- Remote-SSH

## Lesson
