NoBlackBoxes/LastBlackBox/boxes/power/_resources/lessons/DC-DC-Converters.md

# Power : DC-DC Converters
How does efficient DC to DC conversion work? Buck and Boost.

## [Video](https://vimeo.com/1035304311)

## Concepts
- A voltage divider is a bad (inefficient) idea
- Switching regulators are more efficient.
- Must filter out switching noise (ripple)
- Buck vs Boost
- Synchronous Buck (no diode)

## Lesson
