NoBlackBoxes/LastBlackBox/boxes/power/_resources/lessons/NB3_Battery-Pack.md

# Power : NB3 : Battery Pack
Let's install a rechargeable NiMH battery pack on our NB3.

## [Video](https://vimeo.com/1042781111)

## Concepts
- Add velcro mount
- Add battery pack
- Test

## Lesson

- **TASK**: Add a NiMH rechargeable 9.6 volt battery pack to your NB3.
> You should now be able to power and control your NB3 autonomously (without any cables).
