NoBlackBoxes/LastBlackBox/boxes/robotics/_resources/lessons/NB3_Ball-Caster.md

# Robotics : NB3 : Ball Caster
Let's add a front wheel (ball caster) to keep your NB3 from dragging its face on the ground.

## [Video](https://vimeo.com/1034797327)

## Concepts
- Add ball caster
- Choose spacer count (angle of attack)

## Lesson

- **TASK**: Mount caster (ball bearing) to the front of your NB3.
> The ball caster mount should look like this.
