NoBlackBoxes/LastBlackBox/boxes/robotics/_resources/lessons/Reflexes.md

# Robotics : Reflexes
Simple sensory-motor loops that underlie essential behaviour.

## [Video]()

## Concepts

## Lesson
