NoBlackBoxes/LastBlackBox/boxes/control/_resources/lessons/Servo-Loops.md

# Control : Servo Loops
A servo loop connects feedback from a sensor to the control signals sent to a motor.

## [Video](https://vimeo.com/1033963709)

## Concepts
- Feedback
- Demo hobby servo (position) and continuous rotation (speed?)
- PID
- Dissection

## Lesson
