NoBlackBoxes/LastBlackBox/boxes/amplifiers/_resources/lessons/Op-Amps.md

# Amplifiers : Op Amps
Combine *high gain differential amplification* with *negative feedback* to build a much, much better amplifier. We call these devices **operational amplifiers** or **Op Amps**.

## [Video]()

## Concepts
- Differential amplification
- Gain
- (Negative) feedback
- The *ideal* op amp

## Lesson

- Use an OpAmp to make your DIY speaker louder!
