NoBlackBoxes/LastBlackBox/boxes/electrons/_resources/lessons/NB3_Measuring-Current.md

# Electrons : NB3 : Measuring Current
How to measure current with a digital multimeter.

## [Video](https://vimeo.com/1027757287)

## Concepts
- Current is the trickiest of the basic electronic values to measure
- The current must flow *through* the meter. Therefore, you must measure in series.
- **Warning**: Do ***NOT*** try to measure the current coming out of your batteries directly...it will blow your fuse.

## Lesson
