NoBlackBoxes/LastBlackBox/boxes/electrons/_resources/lessons/NB3_Measuring-Resistance.md

# Electrons : NB3 : Measuring Resistance
How to measure resistance with a digital multimeter.

## [Video](https://vimeo.com/1027761453)

## Concepts
- Resistance between two points
- Must pass current from the multimeter through the resistor being measured
- Normally necessary to remove the resistor from the circuit (but there are some exceptions, e.g. an un-powered simple circuit).

## Lesson
