NoBlackBoxes/LastBlackBox/boxes/electrons/_resources/lessons/NB3_Multimeter-Basics.md

# Electrons : NB3 : Multimeter Basics
An overview of digital multimeters for beginners. What can it measure? What features do you need to complete the course?

## [Video](https://vimeo.com/1027764019)

## Concepts
- What is a multimeter? (electrical measurements)
- What types of multimeters? (cheap vs. expensive, analog vs. digital)
- Types of measurements (voltage, resistance, current, and more)
- Probes
- Fuses (over current protection)
- Auto-ranging vs. manual range
- Other features (light, hold)

## Lesson
