NoBlackBoxes/LastBlackBox/boxes/electrons/_resources/lessons/Voltage.md

# Electrons : Voltage
When there is more negative or positive charge in one location vs. another there is a *potential difference* between these locations. This *potential difference* is called a **voltage** and it creates a pressure that pushes electrons from the location with more negative charge to the location with less.

## [Video](https://vimeo.com/1000730032)

## Concepts
- Most materials are electrically neutral
- Static electricity
- Differences in charge concentration create "electric pressure" (potential difference): voltage

## Lesson
