NoBlackBoxes/LastBlackBox/boxes/memory/_resources/lessons/Flip-Flop.md

# Memory : Flip Flop
If we add a clock to our memory, then we can synchronize the operation of our logic circuit.

## [Video]()

## Concepts

## Lesson

- Build an D Flip Flop
