NoBlackBoxes/LastBlackBox/boxes/transistors/_resources/lessons/Transistors-BJTs.md

# Transistors : Transistors (BJTs)
Bipolar junction transistors inject charge carriers to amplify the external *current* flowing. They are current controlled devices.

## [Video]()

## Concepts
- Recall NPN, PNP stacks.
- BJTs use a direct connection to the base that can inject charge carriers.
- Different doping.
- Usage.

## Lesson
