NoBlackBoxes/LastBlackBox/boxes/control/_resources/lessons/H-Bridges.md

# Control : H-Bridges
An H-Bridge allows sending current through a motor in both directions, and thus drive forwards *and* backwards.

## [Video](https://vimeo.com/1034209519)

## Concepts

## Connections

## Lesson
