NoBlackBoxes/LastBlackBox/boxes/memory/README.md

# The Last Black Box : Memory
In this box, you will learn about memory...

<details><summary><i>Materials</i></summary><p>

Name|Description| # |Package|Data|Link|
:-------|:----------|:-----:|:-:|:--:|:--:|
Gate (NAND)|4xNAND gate|2|Active Electronics|[-D-](/boxes/memory/_resources/datasheets/NAND_gates.pdf)|[-L-](https://uk.farnell.com/texas-instruments/cd4011be/ic-4000-cmos-4011-dip14-18v/dp/3120113)

</p></details><hr>

## Memory
#### Watch this video: [Flash Memory](https://vimeo.com/1033230293)
<p align="center">
<a href="https://vimeo.com/1033230293" title="Control+Click to watch in new tab">Flash Memory</a>
</p>

> Storing much of your data requires *quantum mechanics*.

#### Watch this video: [SR Latch](https://vimeo.com/1033238234)
<p align="center">
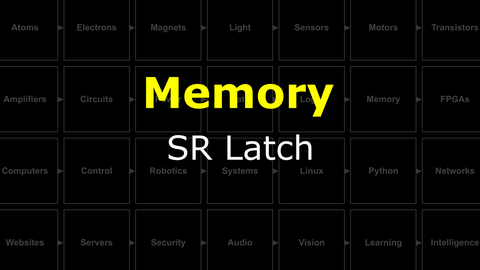
[picture p111: boxes/memory/_resources/lessons/thumbnails/SR-Latch.gif]
SR Latch

</p>

> Logic gates with feedback can hold onto their values...they can remember.

- Understand the role of feedback in an SR latch

### Flip Flop
> If we add a clock to our memory, then we can synchronize the operation of our logic circuit.

- Build an D Flip Flop

# Projects
#### Watch this video: [NB3 : Building an SR Latch](https://vimeo.com/1033234541)
<p align="center">
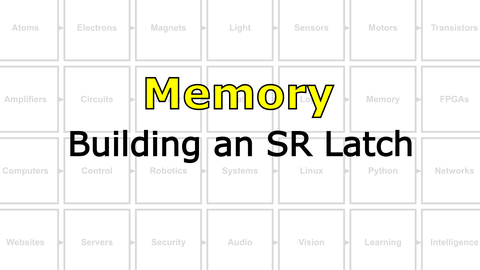
[picture p112: boxes/memory/_resources/lessons/thumbnails/NB3_Building-an-SR-Latch.gif]
NB3 : Building an SR Latch

</p>

> Let's build and test an SR latch from NAND gates.

- Build an SR latch, follow the video guide
