NoBlackBoxes/LastBlackBox/boxes/learning/README.md

# The Last Black Box : Learning
In this box, you will learn about vision...

<details><summary><i>Materials</i></summary><p>

Name|Description| # |Package|Data|Link|
:-------|:----------|:-----:|:-:|:--:|:--:|
Clicker|Loud sound maker (and whistle)|1|Auxiliary|[-D-](/boxes/learning/)|[-L-](https://www.amazon.co.uk/Clicker-Multi-Color-Diyife-Training-Wrist/dp/B076LZ4XGK)

</p></details><hr>

## Learning
### Gradient Descent
> If it gets better, then keep going!

# Projects
### NB3 : Clicker Training
> If a *click* is reinforcing, then training complex behaviour becomes far simpler.
