NoBlackBoxes/LastBlackBox/boxes/security/README.md

# The Last Black Box : Security
In this box, you will learn about security...

<details><summary><i>Materials</i></summary><p>

Name|Description| # |Package|Data|Link|
:-------|:----------|:-----:|:-:|:--:|:--:|
Secret Message|A SHA256 encrypted message (in HEX)|1|Auxiliary|[-D-](/boxes/security/)|[-L-]()

</p></details><hr>

## Security
### One Way Functions
> Easy to compute, hard to inverse.

# Projects
