NoBlackBoxes/LastBlackBox/boxes/servers/flask/README.md

# Servers : Flask
Flask is a Python-based micro-framework for creating (and serving) web applications

## Install

```bash
pip install Flask
```

## Notes
- Request context (request and session)
- Application context

- Request hooks
  - before_request, before_first, after, etc.

- redirects (response that tells the browser to navigate to a new location)

- Templates
  - Jinja2 template engine (for rendering)
