NoBlackBoxes/LastBlackBox/course/versions/ownphone/README.md

# The Last Black Box: *Own Phone*

> **LBB-104**: Smarter than your *smart*phone

<p align="center">
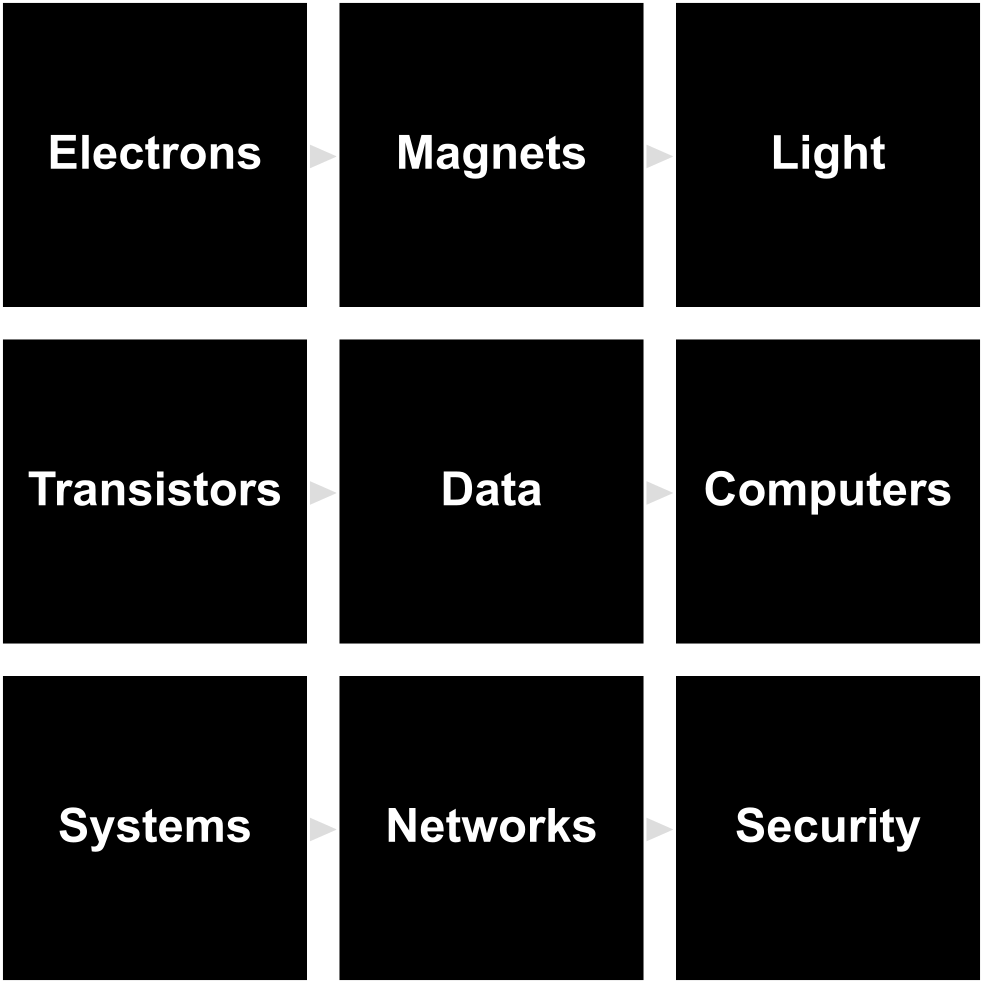
[picture p113: course/_resources/designs/layout/png/layout_ownphone.png]
LBB ownphone layout

</p>

----

## NB2P

You will be building a phone...without using any "black boxes". We thus call this phone the No-Black-Box-Phone or NBBP or ***NB2P***.

----

## Topics

- What is a phone?
  - learn about sound, light, and radio
- What is data?
  - learn about digital, compression
- Where are you?
  - learn about GPS
- Apps

- Attention/Focus
- Addiction
- Manipulation
- Advertisements
- Loot-boxes
- Mental health

## Timeline

### Session 1 - Electrons

- Build a circuit
  - Learn about atoms and electons

### Session 2 - Magnets

- Build a speaker
  - Learn about magnets, motion, and sound

### Session 3 - Light

- Build a radio
  - Learn about light, antennaes, transmitters, and receivers

### Session 4 - Transistors

- The most important thing you don't understand
  - Learn about transistors, amplifiers, and integrated circuits

### Session 5 - Data

- How can two numbers create *everything*?
  - Learn about logic and memory

### Session 6 - Computers

- To think is to compute
  - Learn about computers and FPGAs

### Session 7 - Systems

- Extend your phone with some human-engineered complexity
  - Learn about Linux and Python

### Session 8 - Networks

- Connect and communicate...like a machine
  - Learn about websites, servers, and networks

### Session 9 - Security

- How to keep things private?
  - Learn about encryption and hacking

----

## License

<br />The entire LastBlackBox repository and website is licensed under a <a rel="license" href="http://creativecommons.org/licenses/by-nc-sa/4.0/">Creative Commons Attribution-NonCommercial-ShareAlike 4.0 International License</a>.
