NoBlackBoxes/LastBlackBox/boxes/intelligence/LLMs/gemini/README.md

# Intelligence :  LLMs : Gemini

## Install required Python packages
```bash
pip install google-genai
pip install python-dotenv
```

## Environment File
Create a .env in "base_path"
```txt
GEMINI_API_KEY=######################
```

### Gemini API Key
This is a special code that you can get from Google that allows you to send requests to their computers running very large neural networks. Each time you make a request, they charge a tiny amount of money. This is their business model. I will provide you with a Gemini API key to use during the course...but please don't share it with the internet. (It has a spending cap, but it will be quickly used up if the "world" gets access.)

**NOTE**: You may be able to get a free API from Google, which should suffice for completing the exercises in this course: [Gemini API Quickstart](https://ai.google.dev/gemini-api/docs/quickstart)
