NoBlackBoxes/LastBlackBox/boxes/systems/_resources/lessons/NB3_Programming-Concurrency-Arduino.md

# Systems : NB3 : Programming Concurrency (Arduino)
Getting a microcontroller to perform two tasks (with very different timescales) at the same time is a fun programming challenge. You will develop new skills in organizing your programs and get a glimpse of the problems solved by the *kernel* of a modern operating system.

## [Video](https://vimeo.com/1036094397)

## Concepts
- Demo naive approach and problem
- Demo one solution
- Can you generalize?

## Lesson
