NoBlackBoxes/LastBlackBox/course/_resources/designs/layout/animation_parameters_position_hover.csv

Atoms | 0 | 0.285 | 0.3 | 0 | -30.986 | -30.986 | 0 | -27.959 | -27.959 | 0 | font-size | 0px | 1px | 2.00px
Electrons | 0 | 0.57 | 0.6 | 0 | -29.681 | -29.681 | 0 | -30.709 | -30.709 | 0 | font-size | 0px | 1px | 2.00px
Magnets | 0 | 0.6175 | 0.65 | 0 | -17.162 | -17.162 | 0 | -21.685 | -21.685 | 0 | font-size | 0px | 1px | 2.00px
Light | 0 | 0.285 | 0.3 | 0 | -14.557 | -14.557 | 0 | -27.022 | -27.022 | 0 | font-size | 0px | 1px | 2.00px
Sensors | 0 | 0.4275 | 0.45 | 0 | 4.492 | 4.492 | 0 | -19.107 | -19.107 | 0 | font-size | 0px | 1px | 2.00px
Motors | 0 | 0.475 | 0.55 | 0 | 9.645 | 9.645 | 0 | -22.34 | -22.34 | 0 | font-size | 0px | 1px | 2.00px
Transistors | 0 | 0.1425 | 0.15 | 0 | 16.512 | 16.512 | 0 | -30.364 | -30.364 | 0 | font-size | 0px | 1px | 2.00px
Amplifiers | 0 | 0.475 | 0.5 | 0 | -72.141 | -72.141 | 0 | -5.289 | -5.289 | 0 | font-size | 0px | 1px | 2.00px
Circuits | 0 | 0.52 | 0.5 | 0 | -54.282 | -54.282 | 0 | 2.329 | 2.329 | 0 | font-size | 0px | 1px | 2.00px
Data | 0 | 0.285 | 0.3 | 0 | -34.821 | -34.821 | 0 | 6.803 | 6.803 | 0 | font-size | 0px | 1px | 2.00px
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
