NoBlackBoxes/LastBlackBox/course/_resources/designs/logo/animation_parameters_fill_stroke_delay.csv

Atoms | 0 | 0.57 | 0.6 | 0 | 0 | 0 | 0 | 0 | 0 | 1 | fill | #000000 | #FFFFFF | #FFFFFF | stroke | #FFFFFF | #000000 | #000000
Electrons | 0 | 1.14 | 1.2 | 0 | 0 | 0 | 0 | 0 | 0 | 1 | fill | #000000 | #FFFFFF | #FFFFFF | stroke | #FFFFFF | #000000 | #000000
Magnets | 0 | 1.235 | 1.3 | 0 | 0 | 0 | 0 | 0 | 0 | 1 | fill | #000000 | #FFFFFF | #FFFFFF | stroke | #FFFFFF | #000000 | #000000
Light | 0 | 0.57 | 0.6 | 0 | 0 | 0 | 0 | 0 | 0 | 1 | fill | #000000 | #FFFFFF | #FFFFFF | stroke | #FFFFFF | #000000 | #000000
Sensors | 0 | 0.855 | 0.9 | 0 | 0 | 0 | 0 | 0 | 0 | 1 | fill | #000000 | #FFFFFF | #FFFFFF | stroke | #FFFFFF | #000000 | #000000
Motors | 0 | 2.95 | 3.1 | 0 | 0 | 0 | 0 | 0 | 0 | 1 | fill | #000000 | #000000 | #FFFFFF | stroke | #FFFFFF | #FFFFFF | #000000
Transistors | 0 | 0.285 | 0.3 | 0 | 0 | 0 | 0 | 0 | 0 | 1 | fill | #000000 | #FFFFFF | #FFFFFF | stroke | #FFFFFF | #000000 | #000000
Amplifiers | 0 | 0.95 | 1 | 0 | 0 | 0 | 0 | 0 | 0 | 1 | fill | #000000 | #FFFFFF | #FFFFFF | stroke | #FFFFFF | #000000 | #000000
Circuits | 0 | 1.14 | 1.2 | 0 | 0 | 0 | 0 | 0 | 0 | 1 | fill | #000000 | #FFFFFF | #FFFFFF | stroke | #FFFFFF | #000000 | #000000
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
