NoBlackBoxes/LastBlackBox/course/_resources/designs/logo/animation_parameters_fill_stroke_repeat.csv

Atoms | 0 | 0.57 | 4.2 | 0 | 0 | 0 | 0 | 0 | 0 | 1 | fill | #000000 | #FFFFFF | #FFFFFF | stroke | #FFFFFF | #000000 | #000000
Electrons | 0 | 1.14 | 4.2 | 0 | 0 | 0 | 0 | 0 | 0 | 1 | fill | #000000 | #FFFFFF | #FFFFFF | stroke | #FFFFFF | #000000 | #000000
Magnets | 0 | 1.235 | 4.2 | 0 | 0 | 0 | 0 | 0 | 0 | 1 | fill | #000000 | #FFFFFF | #FFFFFF | stroke | #FFFFFF | #000000 | #000000
Light | 0 | 0.57 | 4.2 | 0 | 0 | 0 | 0 | 0 | 0 | 1 | fill | #000000 | #FFFFFF | #FFFFFF | stroke | #FFFFFF | #000000 | #000000
Sensors | 0 | 0.855 | 4.2 | 0 | 0 | 0 | 0 | 0 | 0 | 1 | fill | #000000 | #FFFFFF | #FFFFFF | stroke | #FFFFFF | #000000 | #000000
Motors | 0 | 2.95 | 4.2 | 0 | 0 | 0 | 0 | 0 | 0 | 1 | fill | #000000 | #000000 | #FFFFFF | stroke | #FFFFFF | #FFFFFF | #000000
Transistors | 0 | 0.285 | 4.2 | 0 | 0 | 0 | 0 | 0 | 0 | 1 | fill | #000000 | #FFFFFF | #FFFFFF | stroke | #FFFFFF | #000000 | #000000
Amplifiers | 0 | 0.95 | 4.2 | 0 | 0 | 0 | 0 | 0 | 0 | 1 | fill | #000000 | #FFFFFF | #FFFFFF | stroke | #FFFFFF | #000000 | #000000
Circuits | 0 | 1.14 | 4.2 | 0 | 0 | 0 | 0 | 0 | 0 | 1 | fill | #000000 | #FFFFFF | #FFFFFF | stroke | #FFFFFF | #000000 | #000000
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
