NoBlackBoxes/LastBlackBox/boxes/amplifiers/_resources/lessons/thumbnails/Op-Amps.png

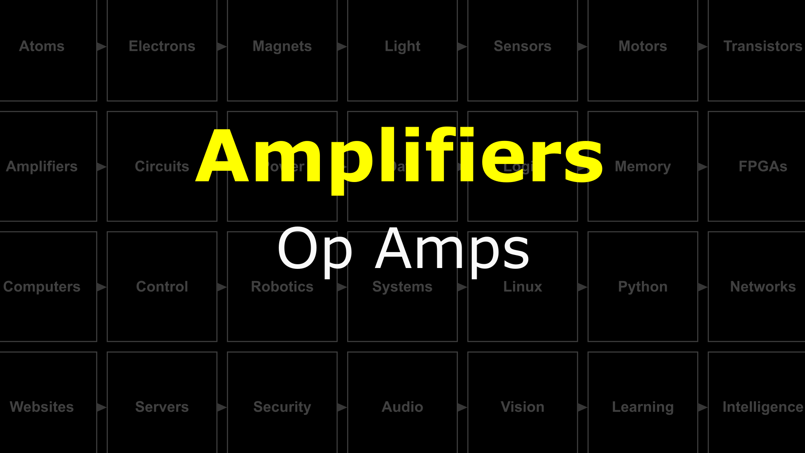
boxes/amplifiers/_resources/lessons/thumbnails/Op-Amps.png
