NoBlackBoxes/LastBlackBox/boxes/atoms/_resources/images/periodic_table.png

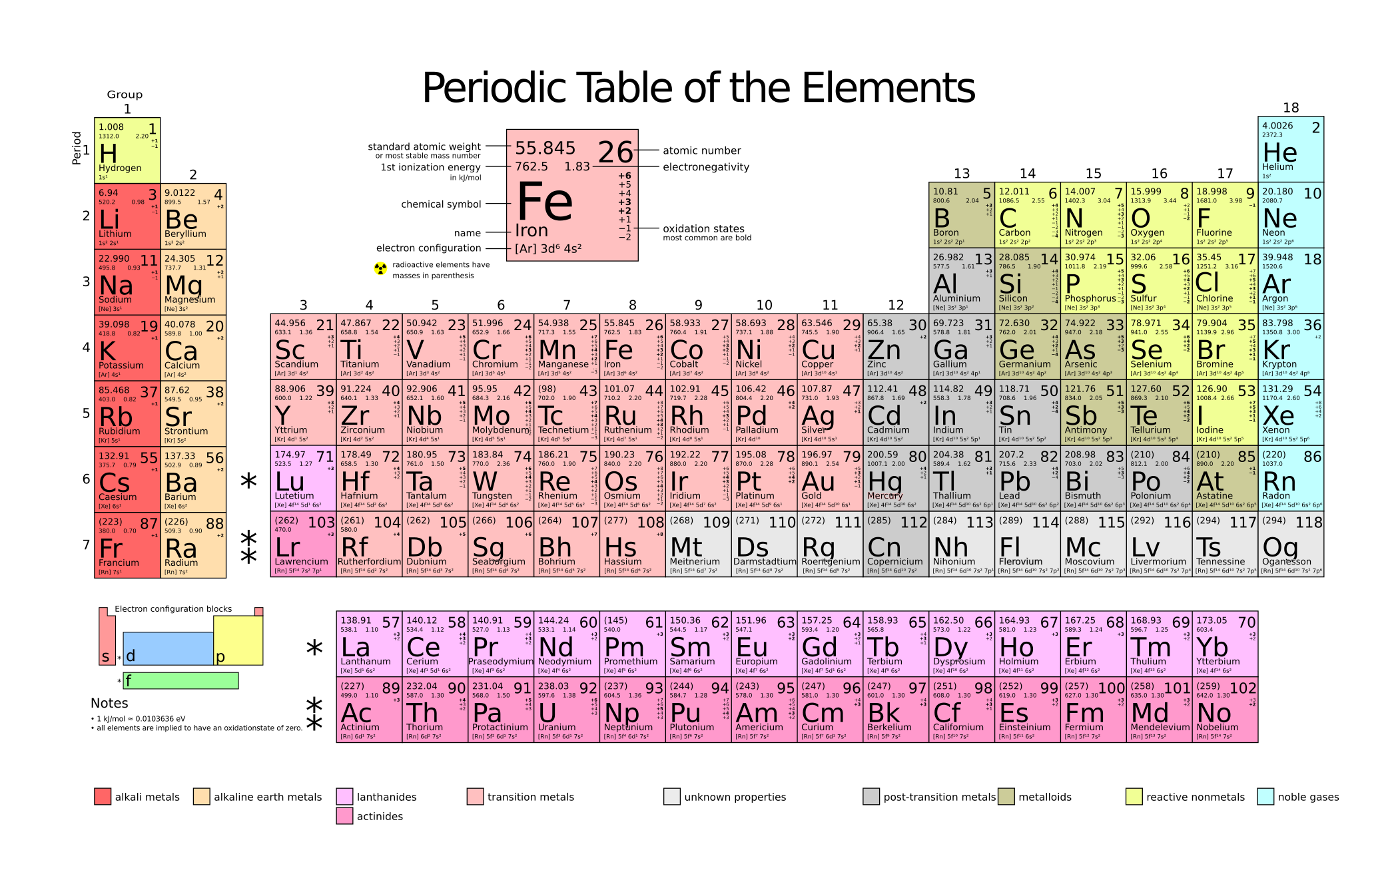
boxes/atoms/_resources/images/periodic_table.png
