NoBlackBoxes/LastBlackBox/boxes/atoms/_resources/lessons/thumbnails/Chemistry.png

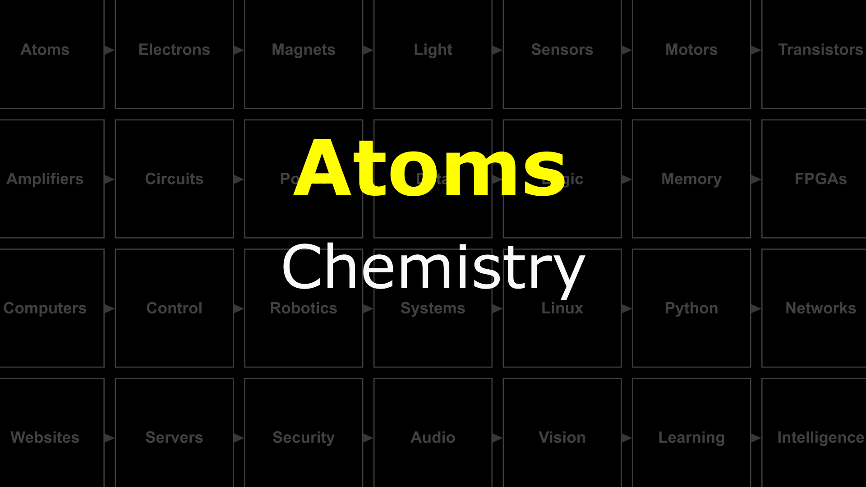
boxes/atoms/_resources/lessons/thumbnails/Chemistry.png
