NoBlackBoxes/LastBlackBox/boxes/atoms/card/periodic_table_card_back.png

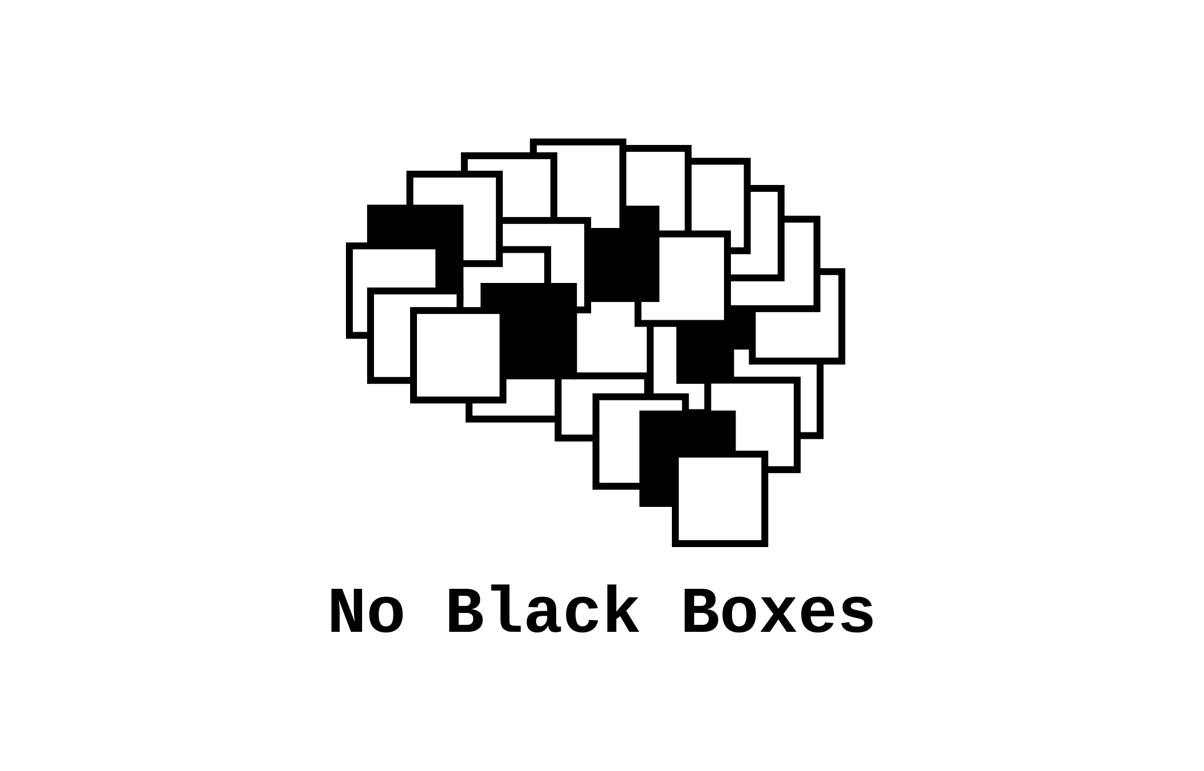
boxes/atoms/card/periodic_table_card_back.png
