NoBlackBoxes/LastBlackBox/boxes/atoms/card/periodic_table_card_front.png

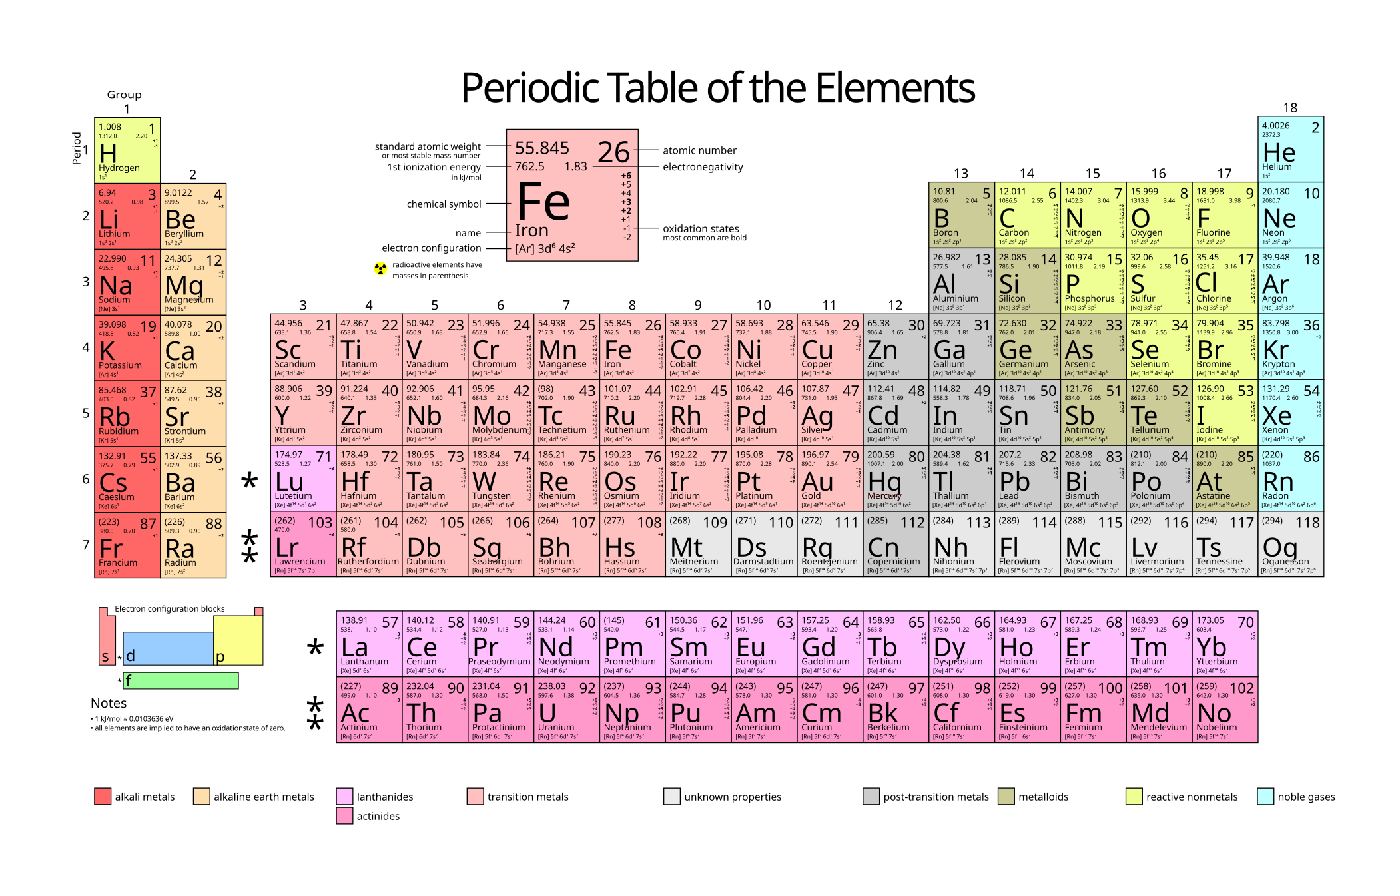
boxes/atoms/card/periodic_table_card_front.png
