NoBlackBoxes/LastBlackBox/boxes/audio/_resources/datasheets/CQR0508.jpg

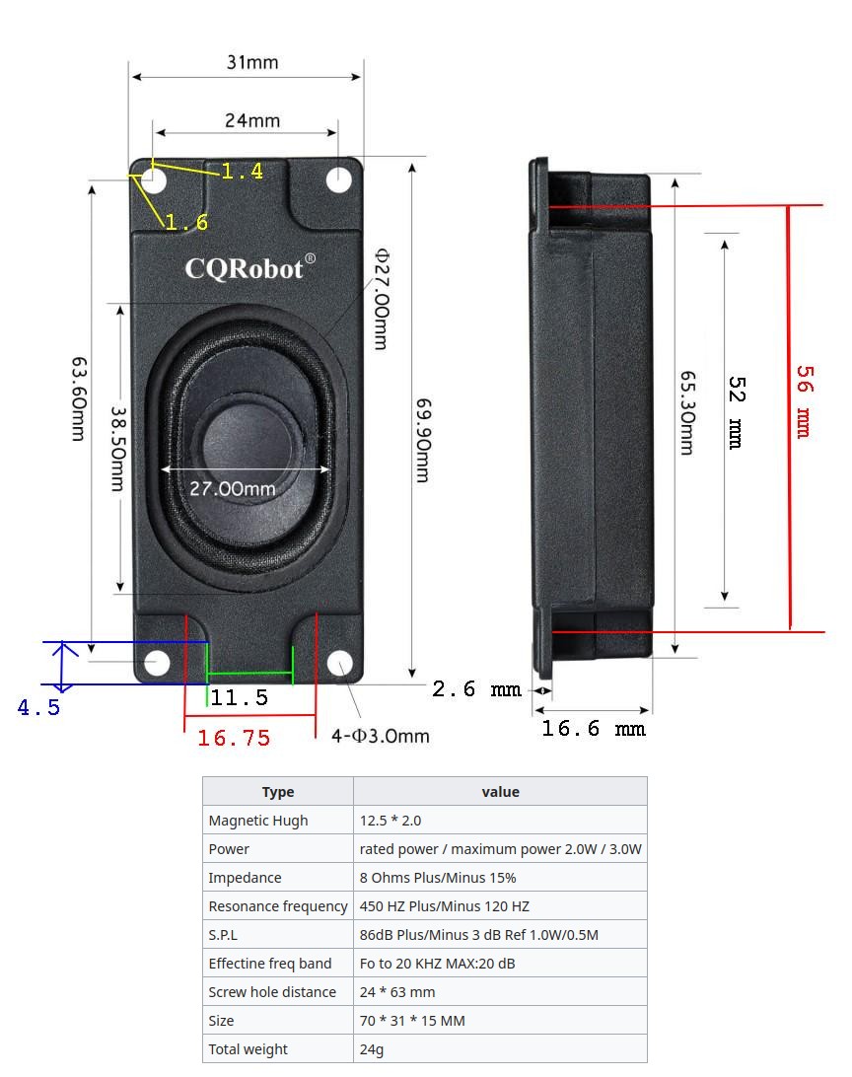
boxes/audio/_resources/datasheets/CQR0508.jpg
