NoBlackBoxes/LastBlackBox/boxes/audio/_resources/images/I2S.png

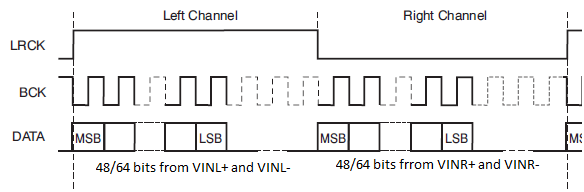
boxes/audio/_resources/images/I2S.png
