NoBlackBoxes/LastBlackBox/boxes/audio/NB3_ear/NB3_ear_back.png

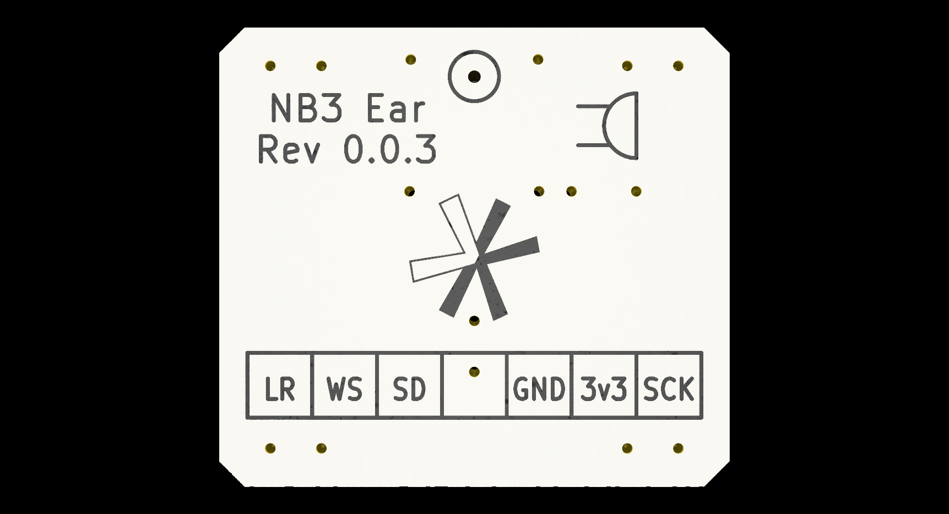
boxes/audio/NB3_ear/NB3_ear_back.png
