NoBlackBoxes/LastBlackBox/boxes/audio/NB3_ear/NB3_ear_FAB_pos_settings.png

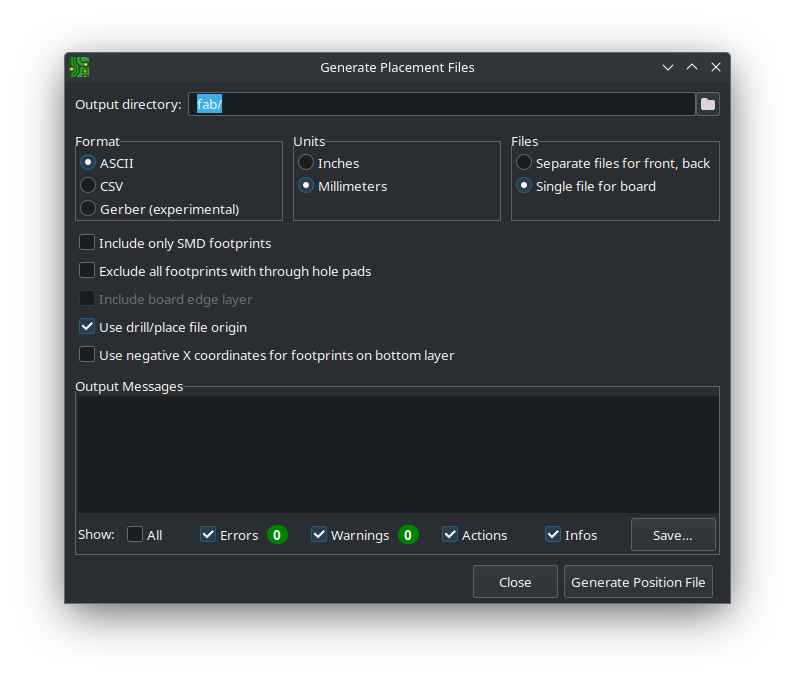
boxes/audio/NB3_ear/NB3_ear_FAB_pos_settings.png
