NoBlackBoxes/LastBlackBox/boxes/audio/NB3_mouth/NB3_mouth_FAB_plot_settings.png

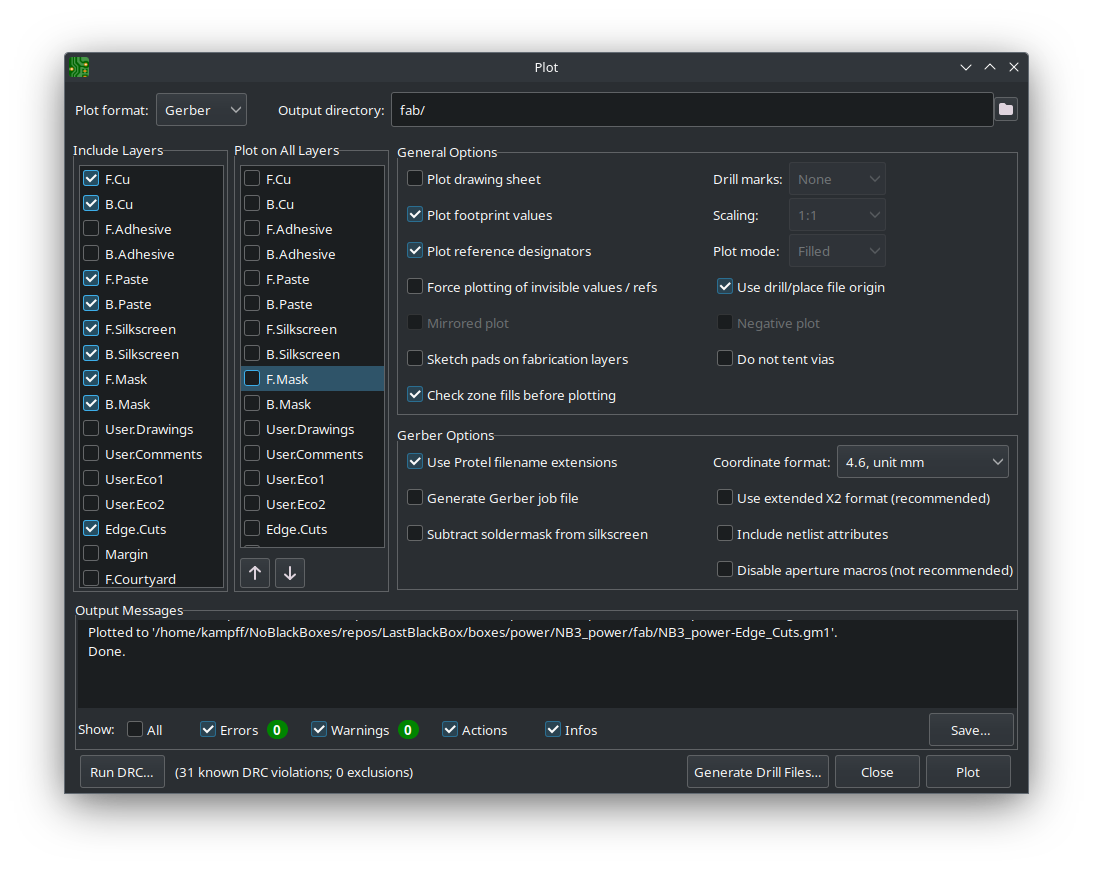
boxes/audio/NB3_mouth/NB3_mouth_FAB_plot_settings.png
