NoBlackBoxes/LastBlackBox/boxes/audio/NB3_mouth/NB3_mouth_front.png

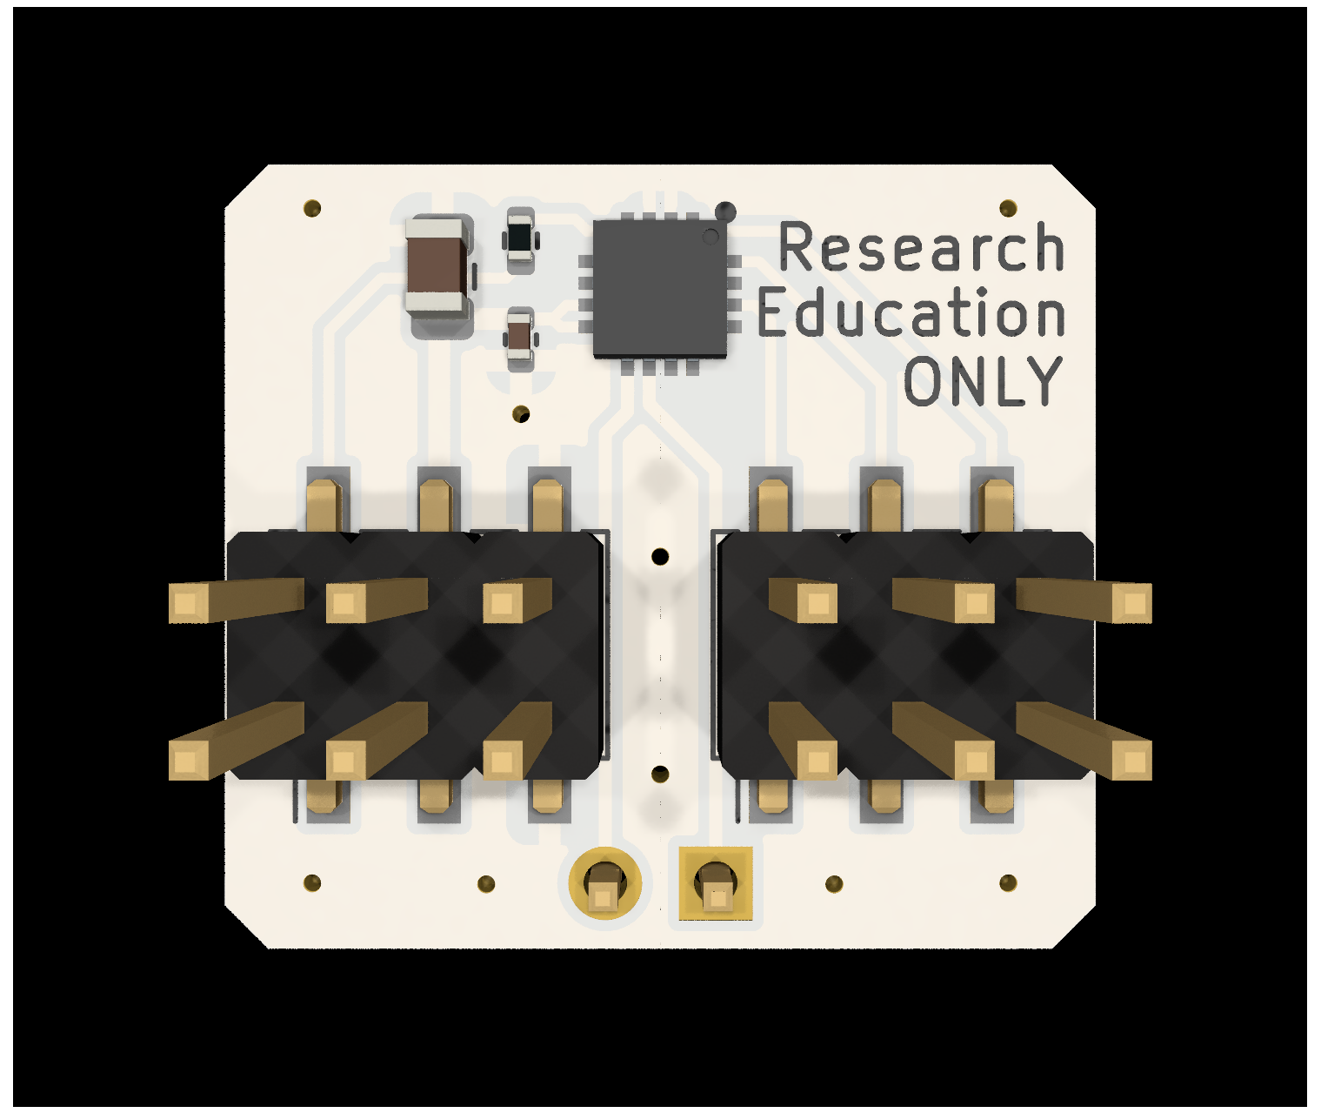
boxes/audio/NB3_mouth/NB3_mouth_front.png
