NoBlackBoxes/LastBlackBox/boxes/computers/_resources/lessons/thumbnails/Low-Level-Programming.png

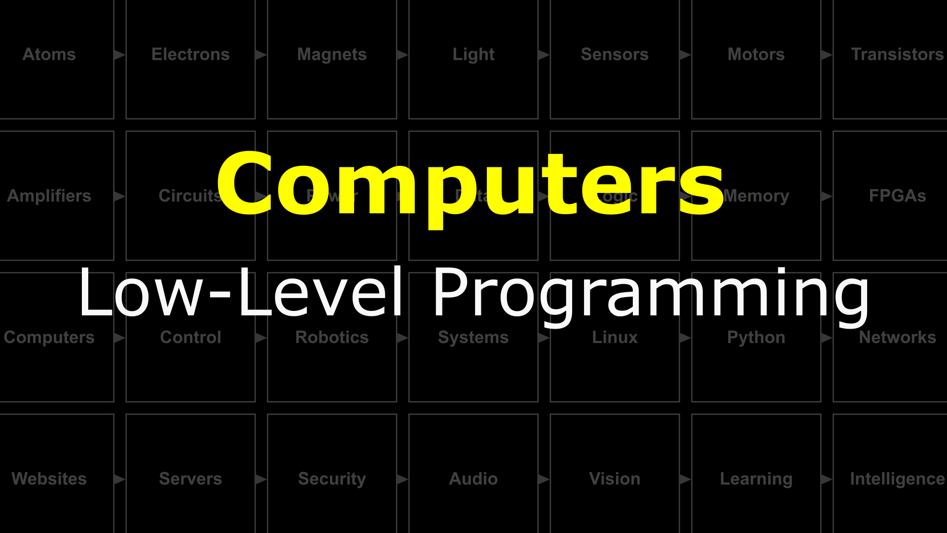
boxes/computers/_resources/lessons/thumbnails/Low-Level-Programming.png
