NoBlackBoxes/LastBlackBox/boxes/data/_resources/images/ASCII-Table.png

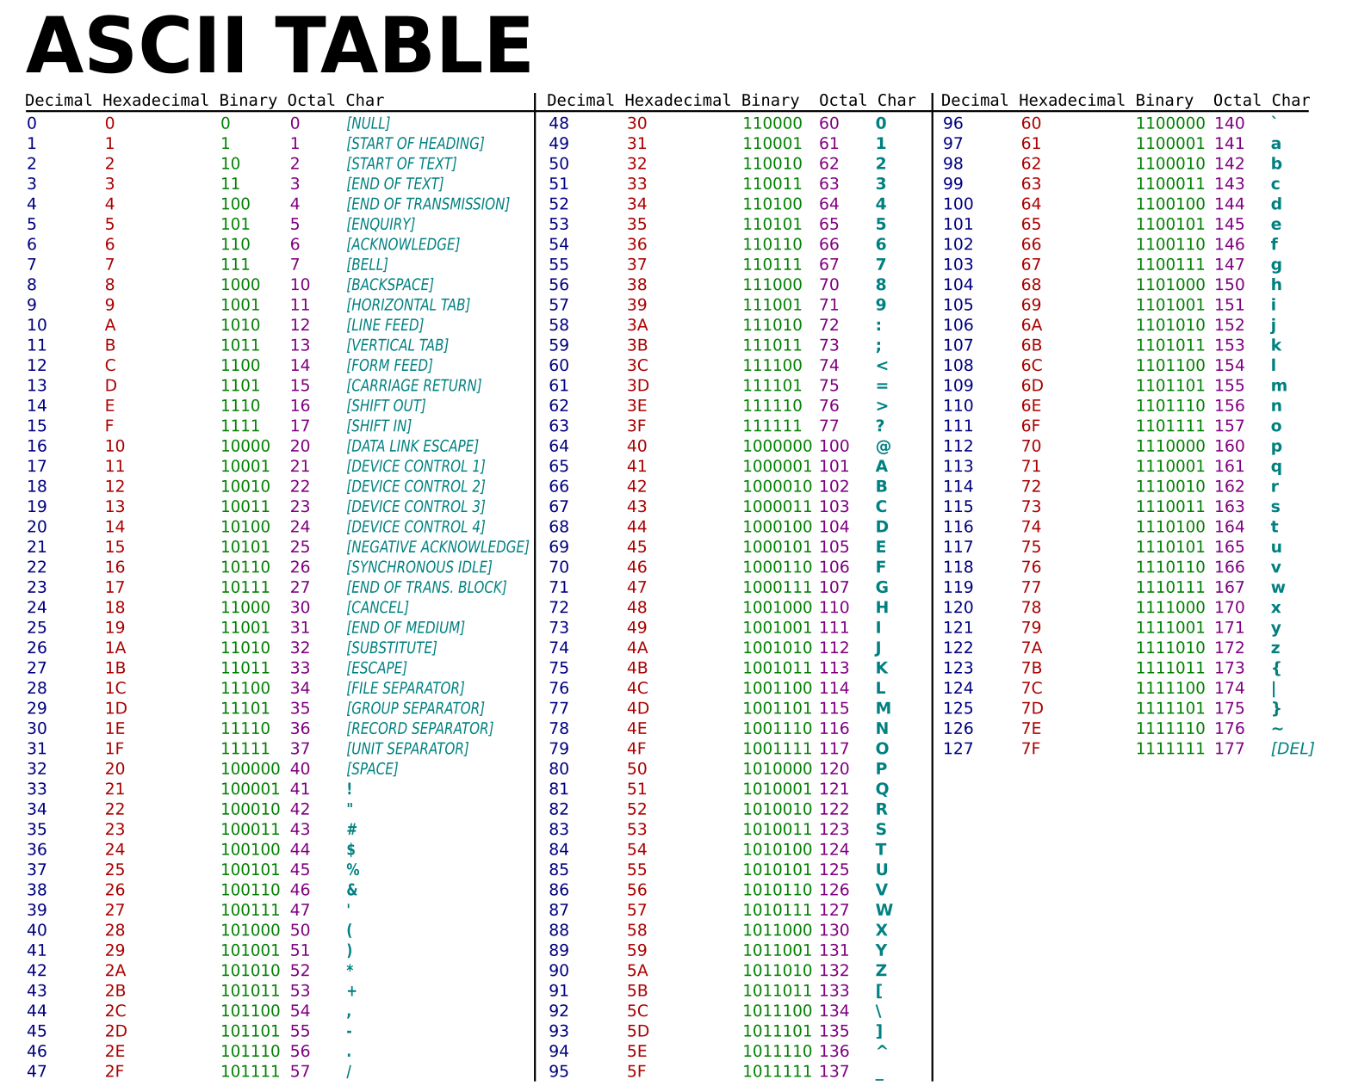
boxes/data/_resources/images/ASCII-Table.png
