NoBlackBoxes/LastBlackBox/boxes/electrons/_resources/lessons/thumbnails/NB3_Designing-PCBs-With-KiCAD.gif

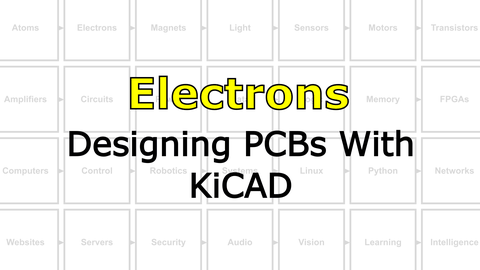
boxes/electrons/_resources/lessons/thumbnails/NB3_Designing-PCBs-With-KiCAD.gif
