NoBlackBoxes/LastBlackBox/boxes/electrons/_resources/lessons/thumbnails/NB3_How-Do-Multimeters-Work.png

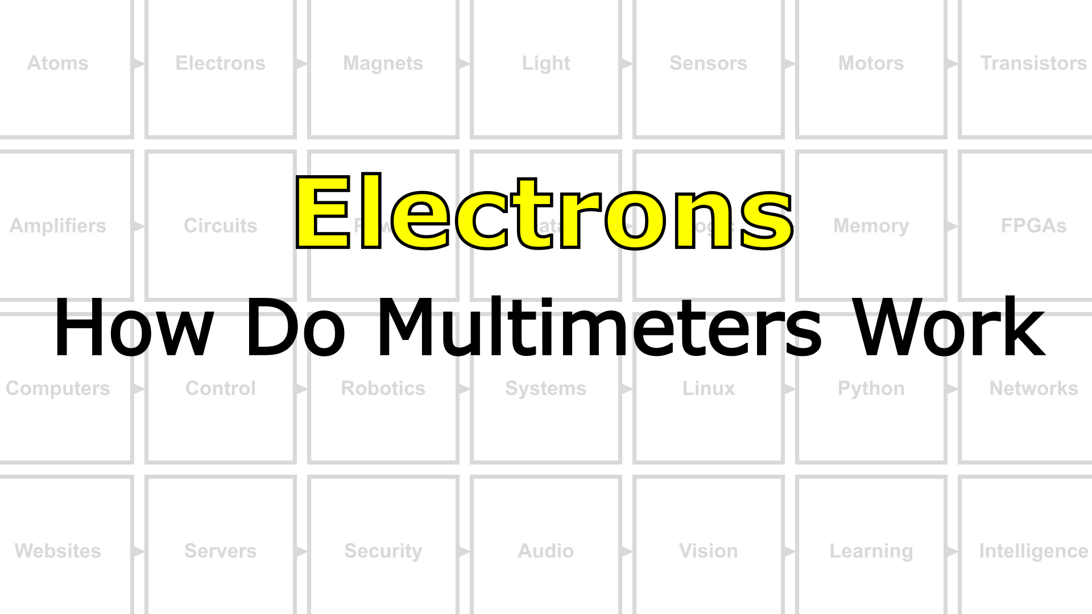
boxes/electrons/_resources/lessons/thumbnails/NB3_How-Do-Multimeters-Work.png
