NoBlackBoxes/LastBlackBox/boxes/electrons/NB3_body/NB3_body_back.png

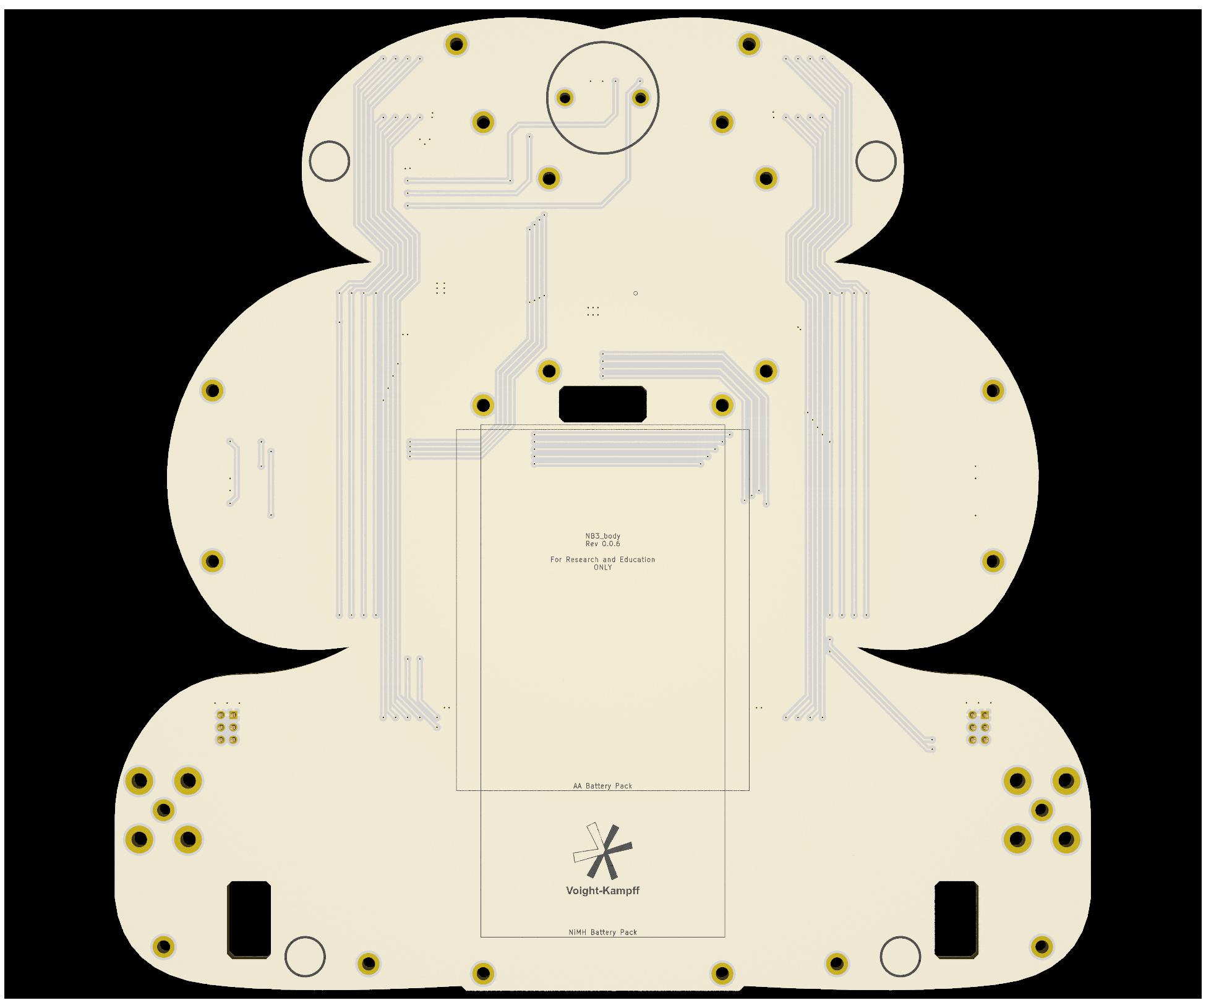
boxes/electrons/NB3_body/NB3_body_back.png
