NoBlackBoxes/LastBlackBox/boxes/electrons/NB3_body/NB3_body_front.png

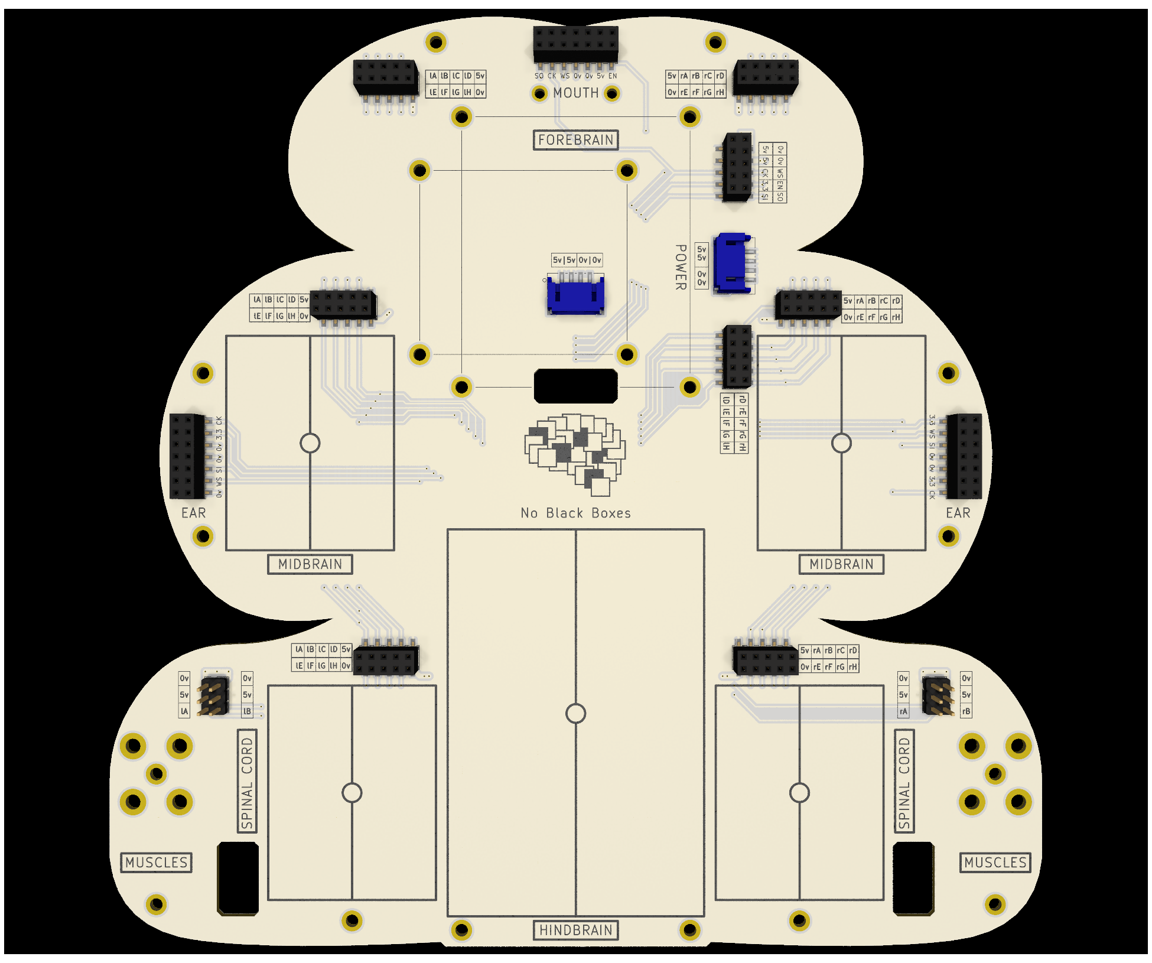
boxes/electrons/NB3_body/NB3_body_front.png
