NoBlackBoxes/LastBlackBox/boxes/fpgas/_resources/lessons/thumbnails/Hardware-Description-Languages.png

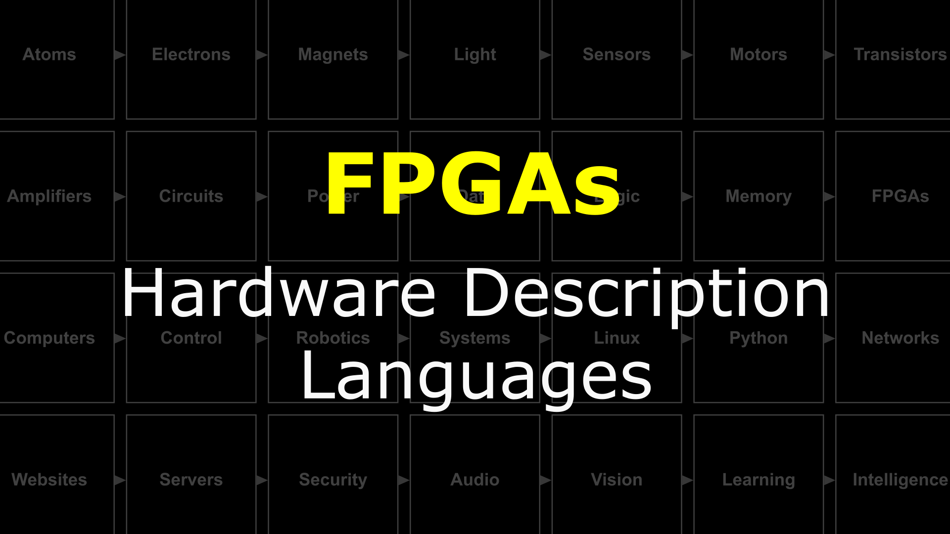
boxes/fpgas/_resources/lessons/thumbnails/Hardware-Description-Languages.png
