NoBlackBoxes/LastBlackBox/boxes/fpgas/NB3_hindbrain/NB3_hindbrain_back.png

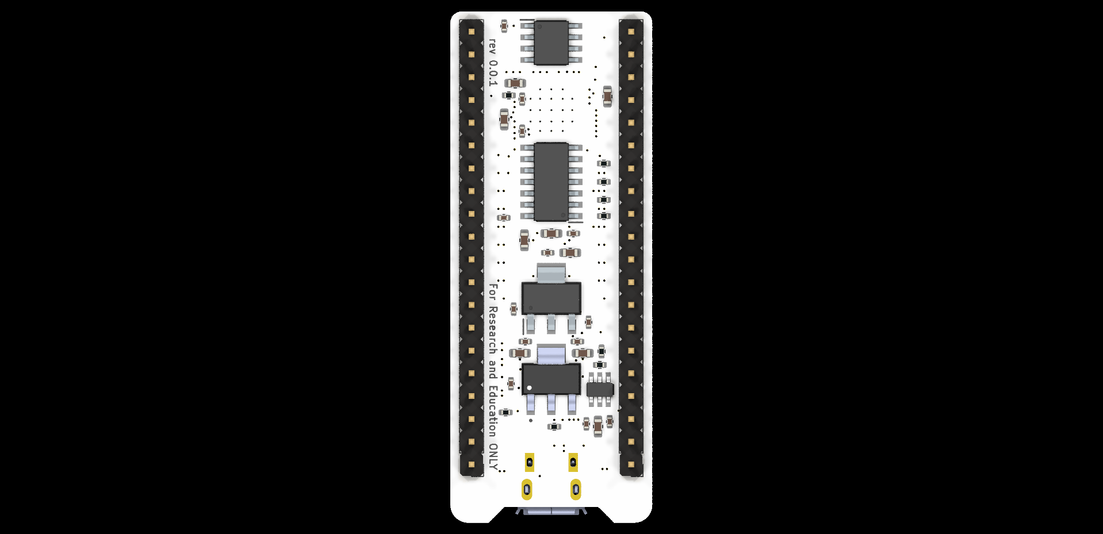
boxes/fpgas/NB3_hindbrain/NB3_hindbrain_back.png
