NoBlackBoxes/LastBlackBox/boxes/intelligence/transformers/vision/_data/zoom_lesson.jpg

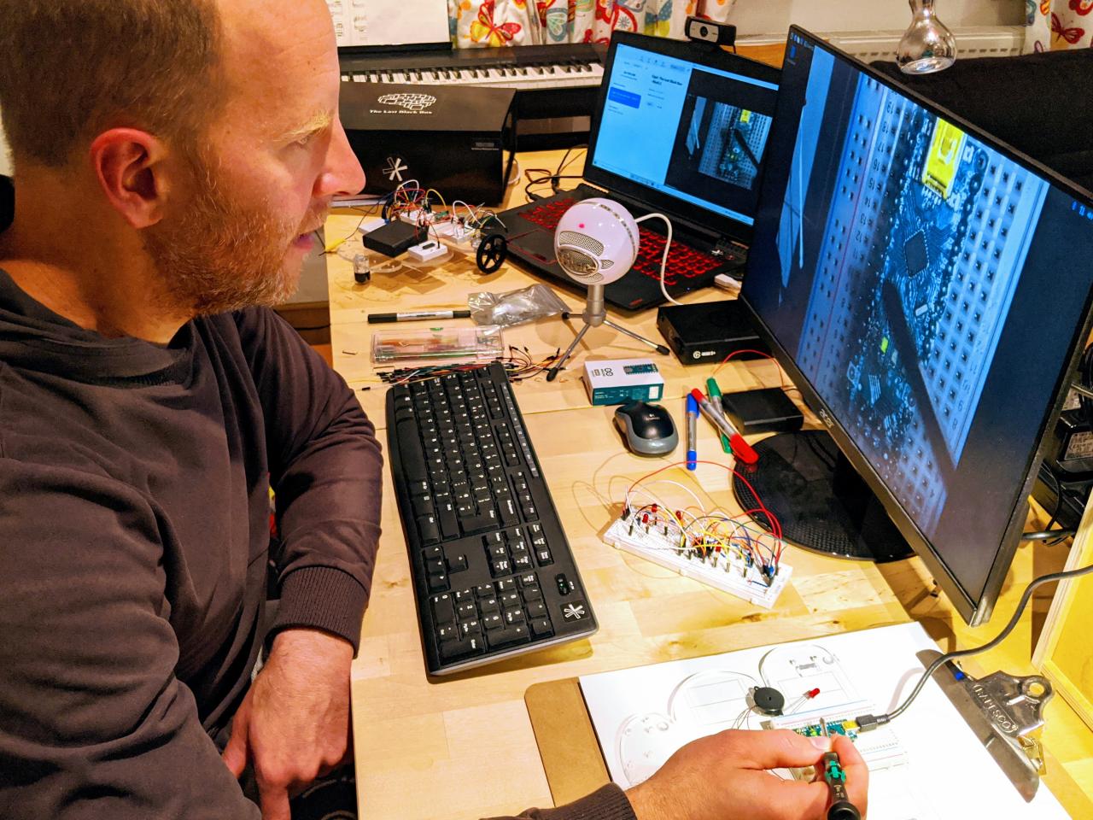
boxes/intelligence/transformers/vision/_data/zoom_lesson.jpg
