NoBlackBoxes/LastBlackBox/boxes/learning/_resources/lessons/thumbnails/NB3_Clicker-Training.png

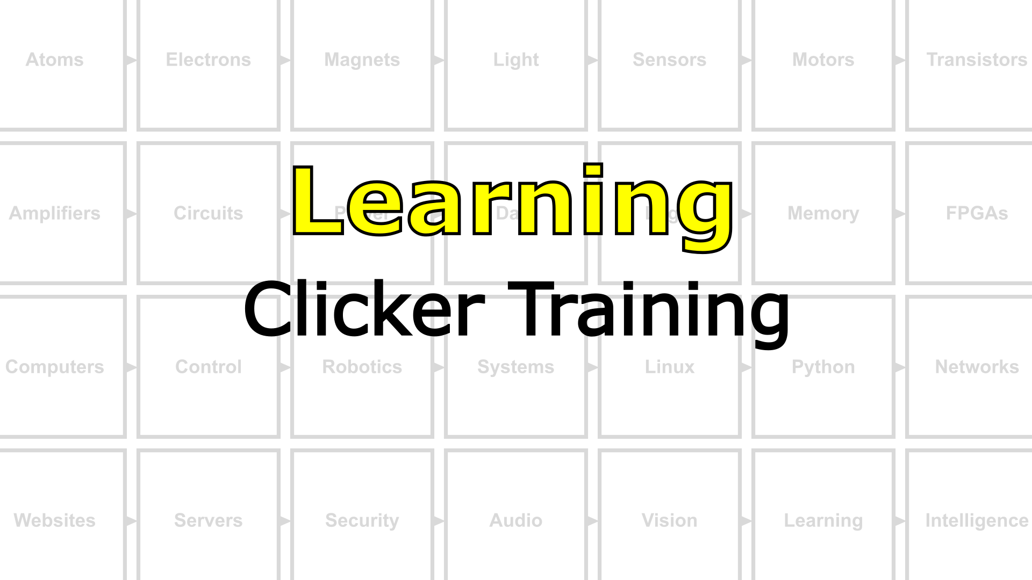
boxes/learning/_resources/lessons/thumbnails/NB3_Clicker-Training.png
