NoBlackBoxes/LastBlackBox/boxes/motors/_resources/images/brushed_DC_motor.png

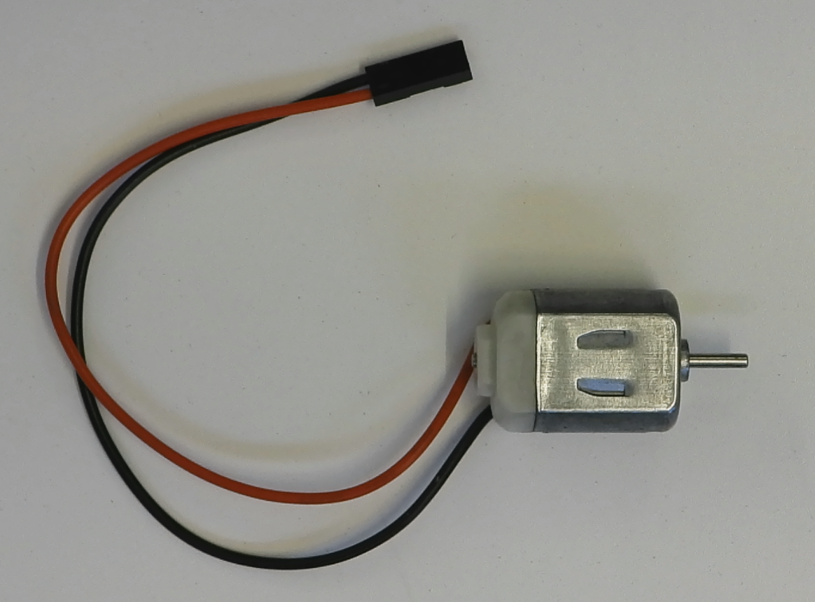
boxes/motors/_resources/images/brushed_DC_motor.png
