NoBlackBoxes/LastBlackBox/boxes/motors/_resources/images/DC_motor_anatomy.png

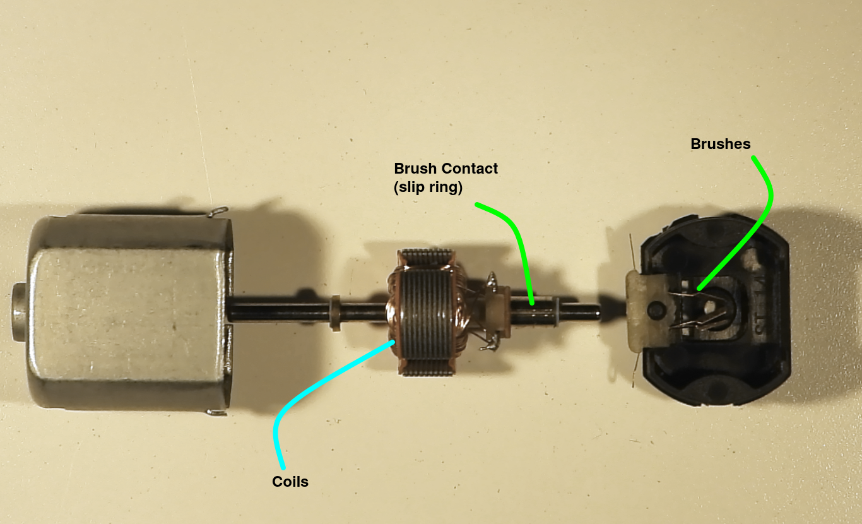
boxes/motors/_resources/images/DC_motor_anatomy.png
