NoBlackBoxes/LastBlackBox/boxes/motors/_resources/lessons/thumbnails/DC-Motors.png

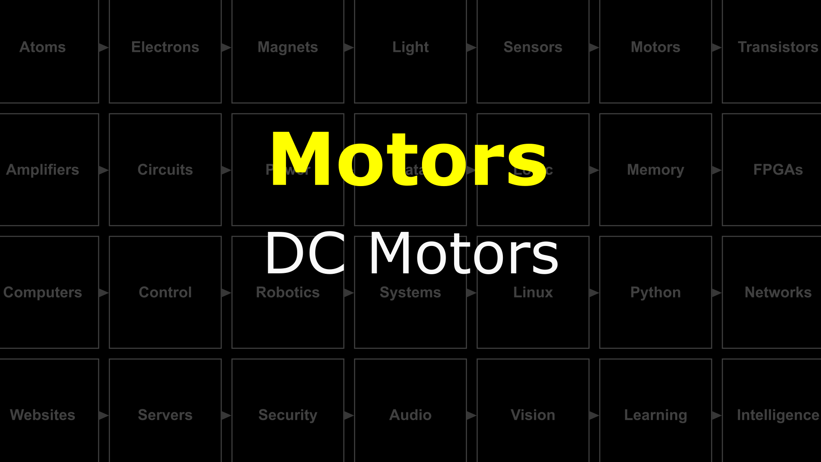
boxes/motors/_resources/lessons/thumbnails/DC-Motors.png
