NoBlackBoxes/LastBlackBox/boxes/networks/_resources/images/Internet_map_in_February_82.png

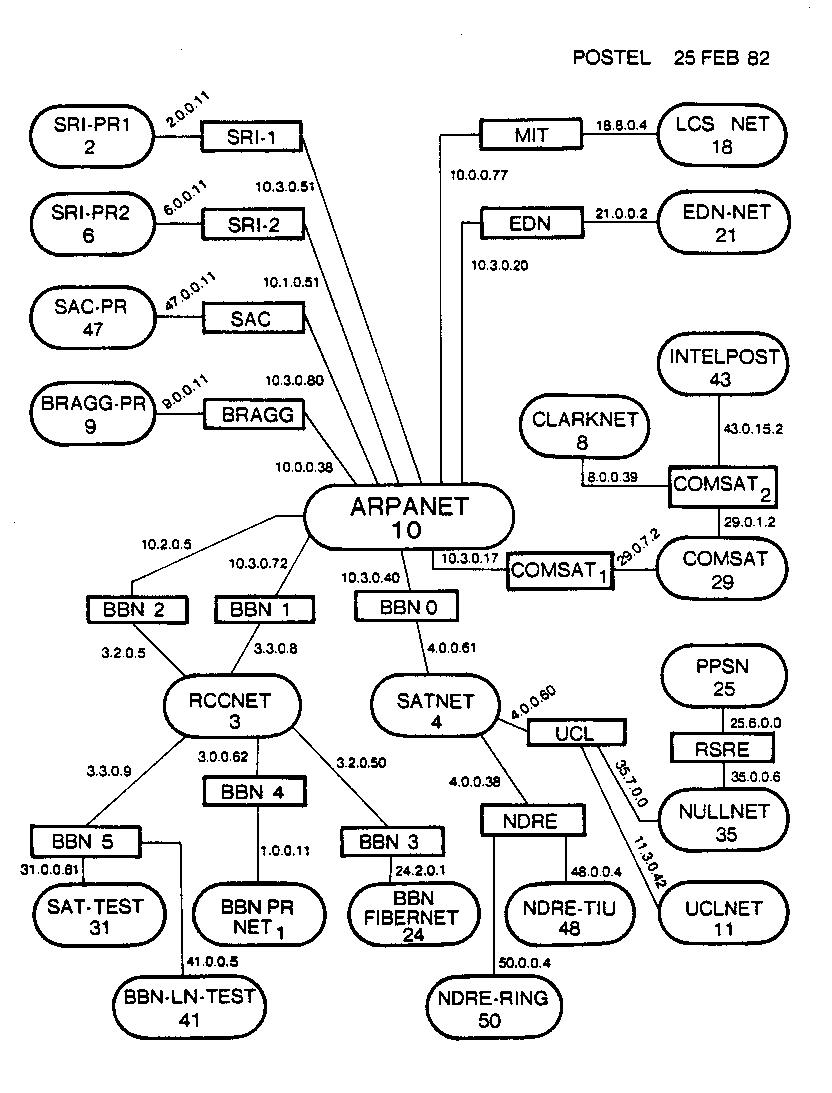
boxes/networks/_resources/images/Internet_map_in_February_82.png
