NoBlackBoxes/LastBlackBox/boxes/power/NB3_charger/NB3_charger_FAB_plot_settings.png

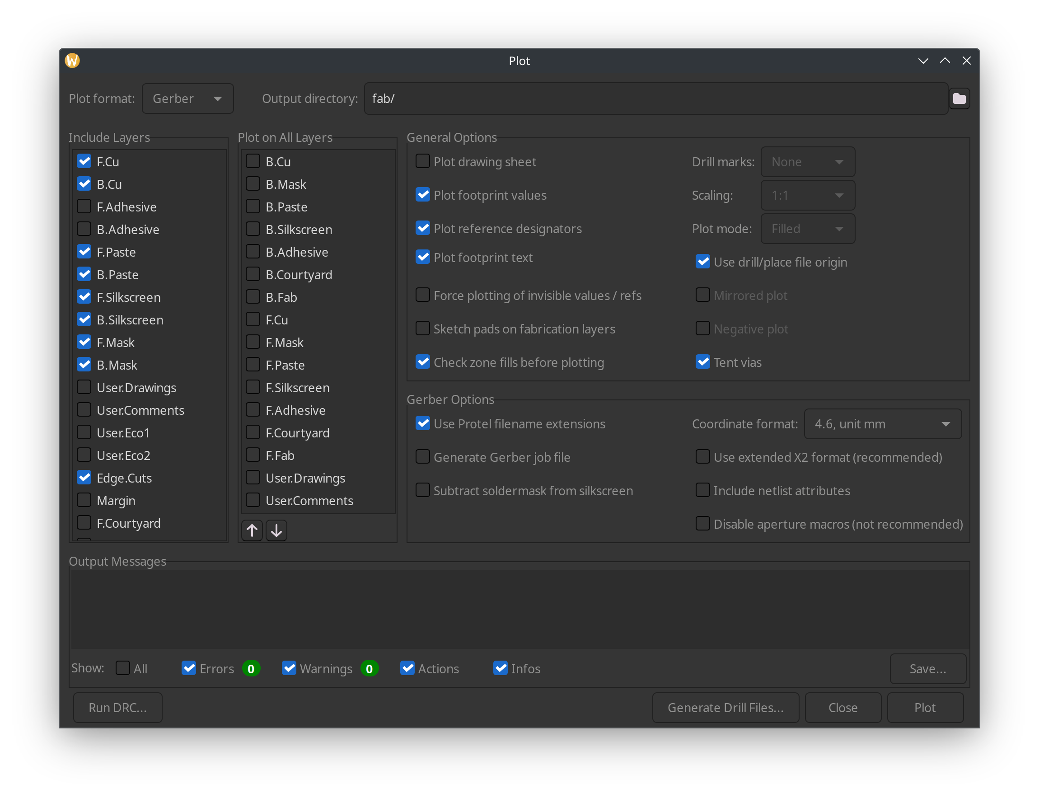
boxes/power/NB3_charger/NB3_charger_FAB_plot_settings.png
