NoBlackBoxes/LastBlackBox/boxes/power/NB3_power/NB3_power_back.png

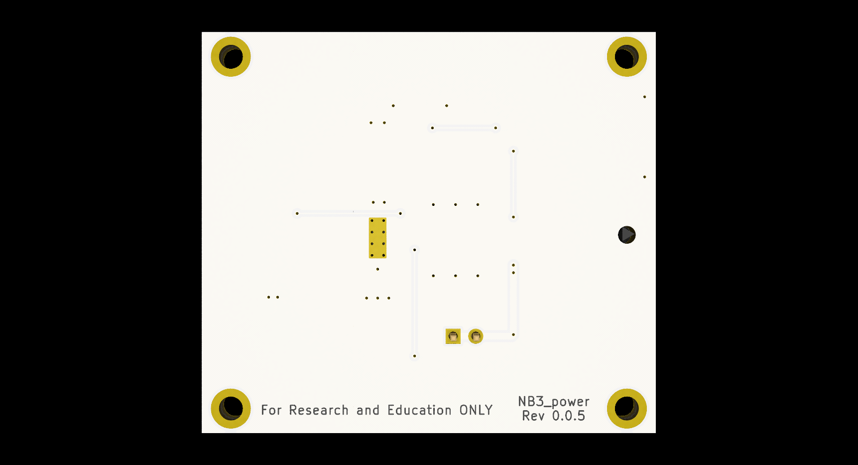
boxes/power/NB3_power/NB3_power_back.png
