NoBlackBoxes/LastBlackBox/boxes/power/NB3_power/NB3_power_front.png

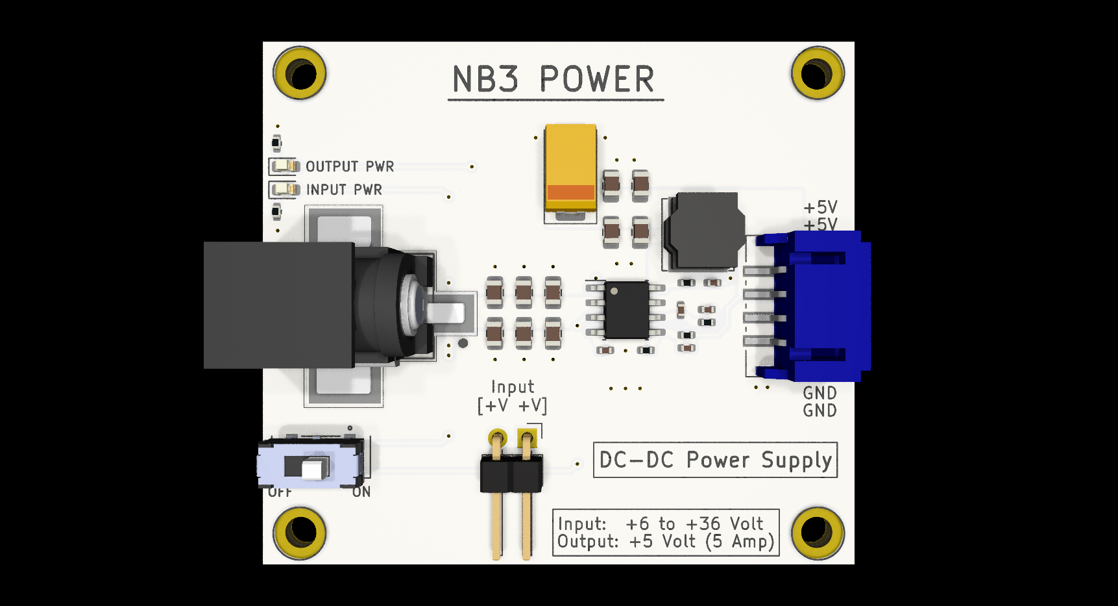
boxes/power/NB3_power/NB3_power_front.png
