NoBlackBoxes/LastBlackBox/boxes/python/_resources/images/image.jpeg

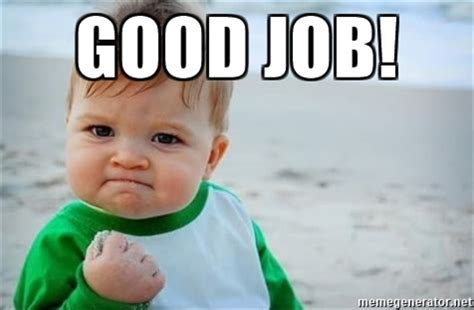
boxes/python/_resources/images/image.jpeg
