NoBlackBoxes/LastBlackBox/boxes/robotics/_resources/datasheets/micro_limit_switch.jpg

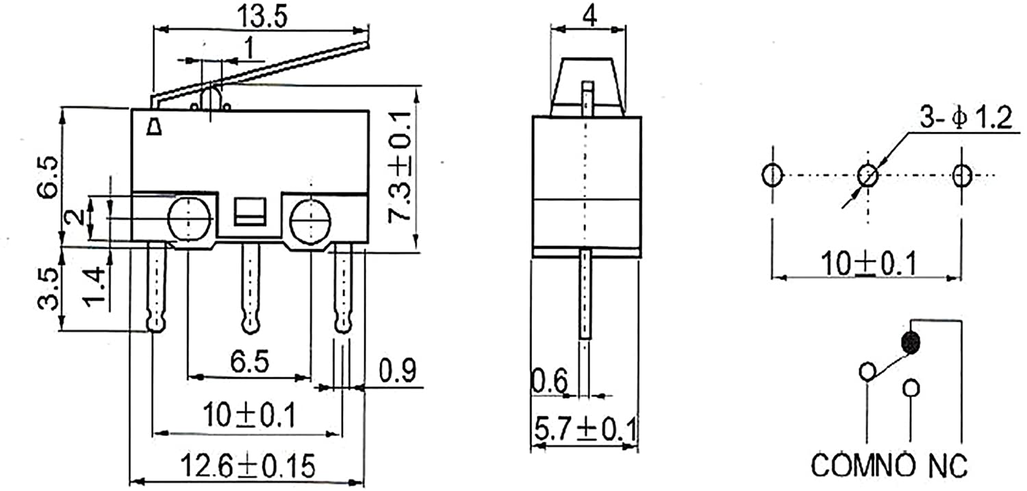
boxes/robotics/_resources/datasheets/micro_limit_switch.jpg
