NoBlackBoxes/LastBlackBox/boxes/robotics/_resources/lessons/thumbnails/NB3_Muscles-DC-Gear-Motors.png

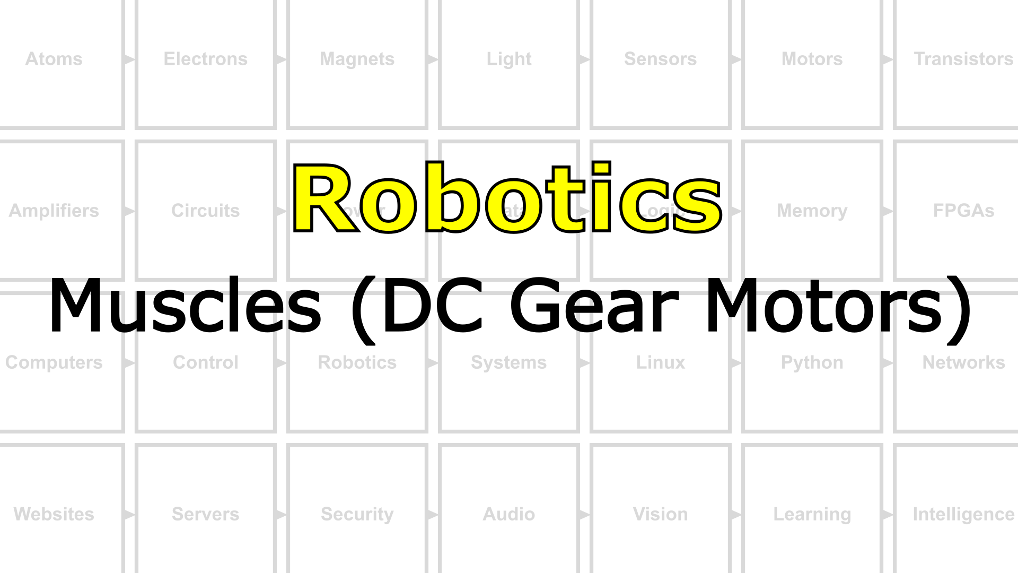
boxes/robotics/_resources/lessons/thumbnails/NB3_Muscles-DC-Gear-Motors.png
