NoBlackBoxes/LastBlackBox/boxes/systems/_resources/datasheets/rpi4b_heatsinks.jpg

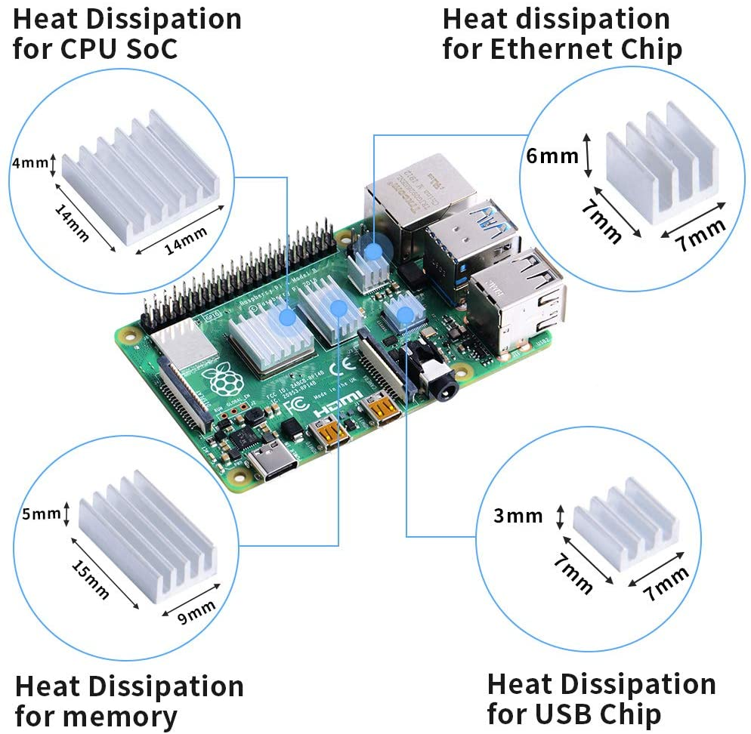
boxes/systems/_resources/datasheets/rpi4b_heatsinks.jpg
