NoBlackBoxes/LastBlackBox/boxes/systems/_resources/datasheets/speakers_3W.jpg

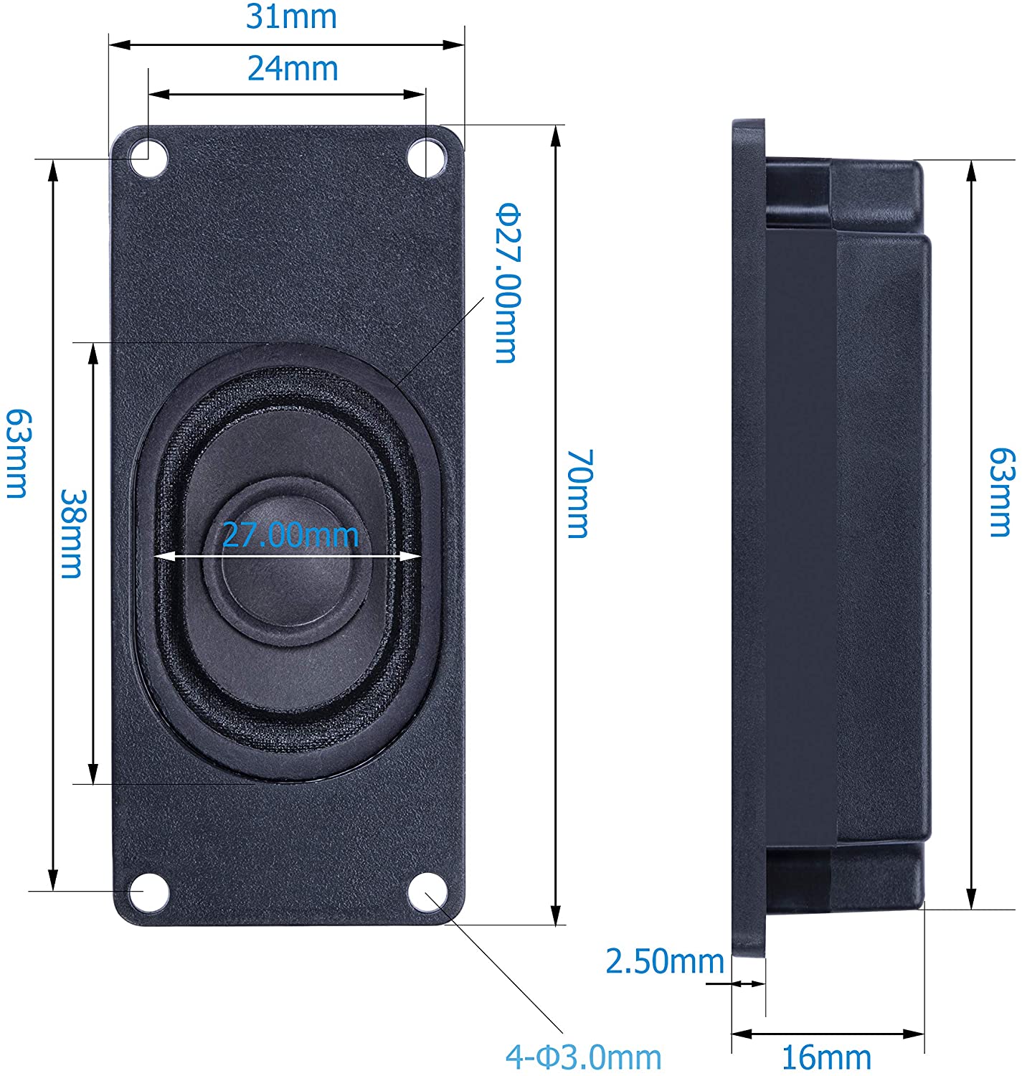
boxes/systems/_resources/datasheets/speakers_3W.jpg
