NoBlackBoxes/LastBlackBox/boxes/systems/connecting/resources/images/raspi_config_main_menu.png

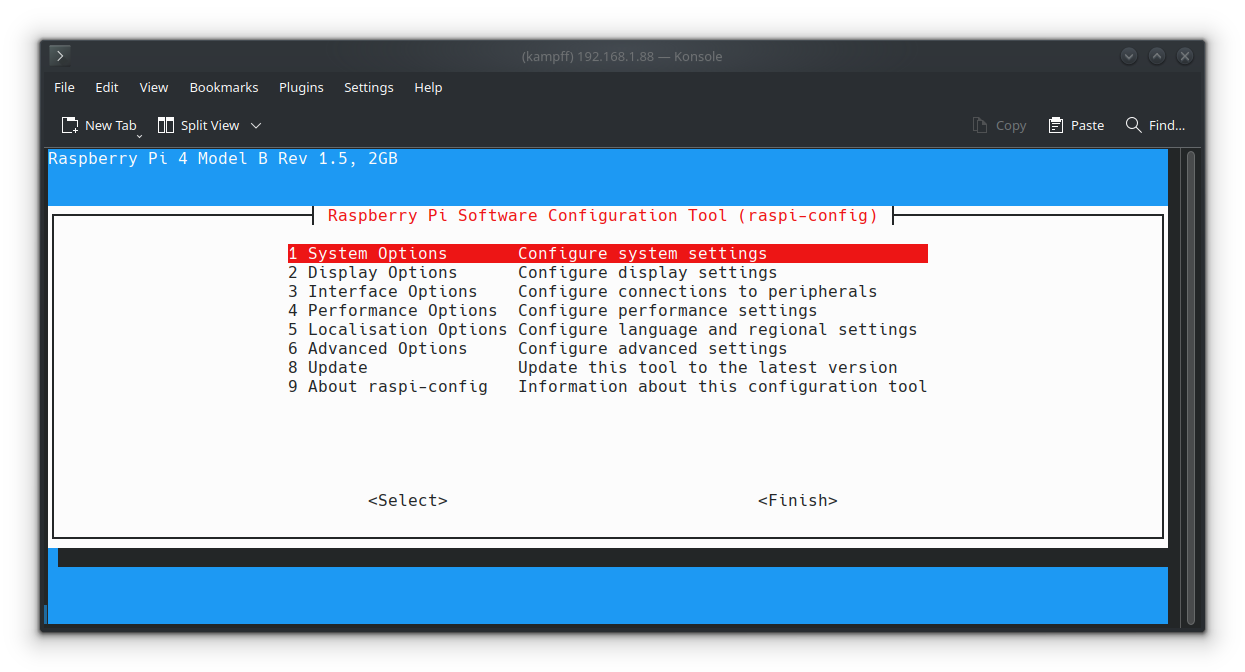
boxes/systems/connecting/resources/images/raspi_config_main_menu.png
