NoBlackBoxes/LastBlackBox/boxes/systems/NB3_eyes/NB3_eyes_back.png

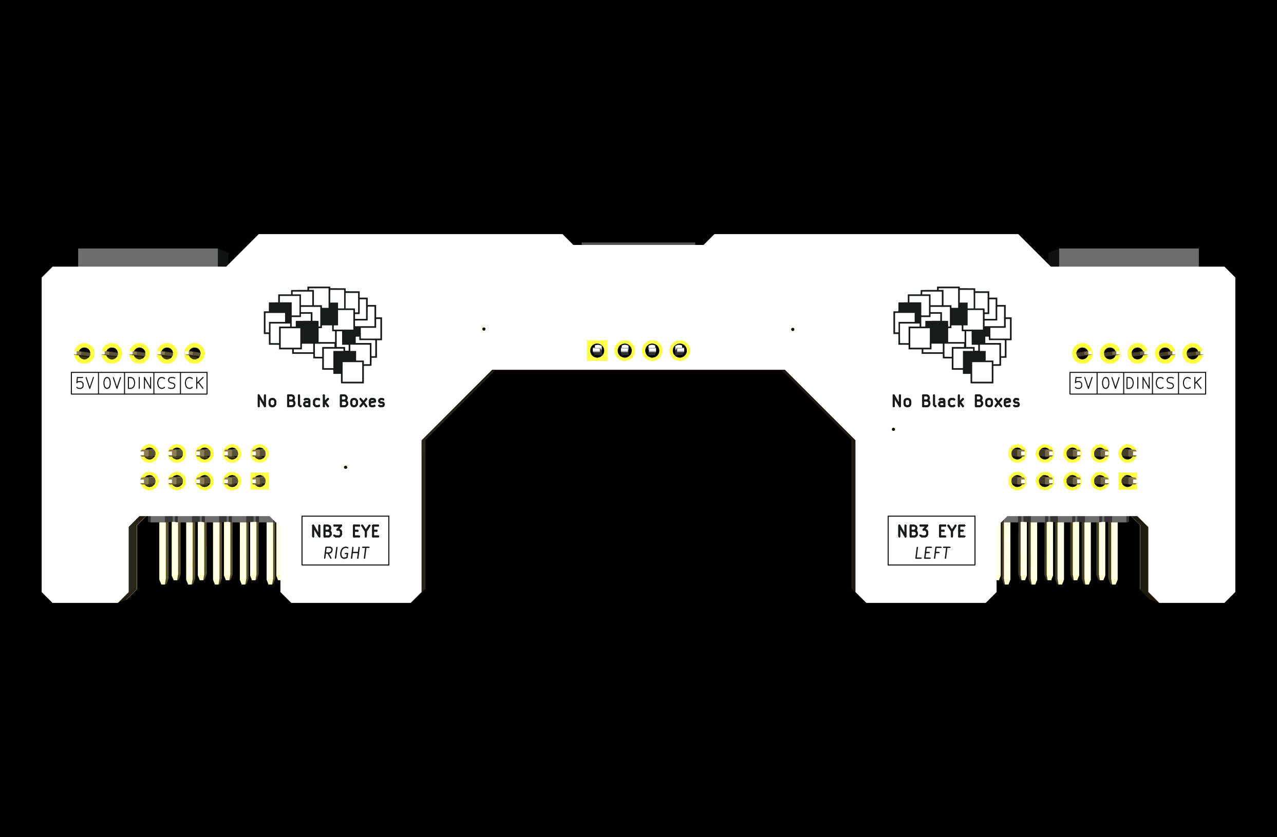
boxes/systems/NB3_eyes/NB3_eyes_back.png
