NoBlackBoxes/LastBlackBox/boxes/systems/NB3_eyes/settings/NB3_eyes_FAB_drill_settings.png

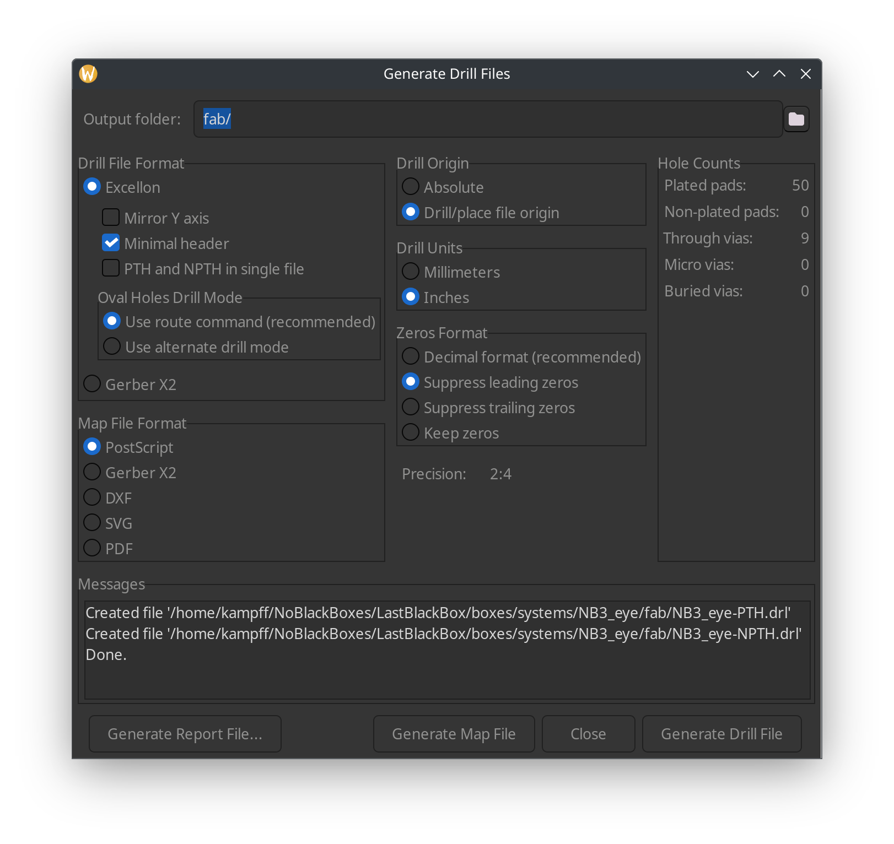
boxes/systems/NB3_eyes/settings/NB3_eyes_FAB_drill_settings.png
