NoBlackBoxes/LastBlackBox/boxes/vision/_resources/datasheets/Hsl-hsv_models.svg.png

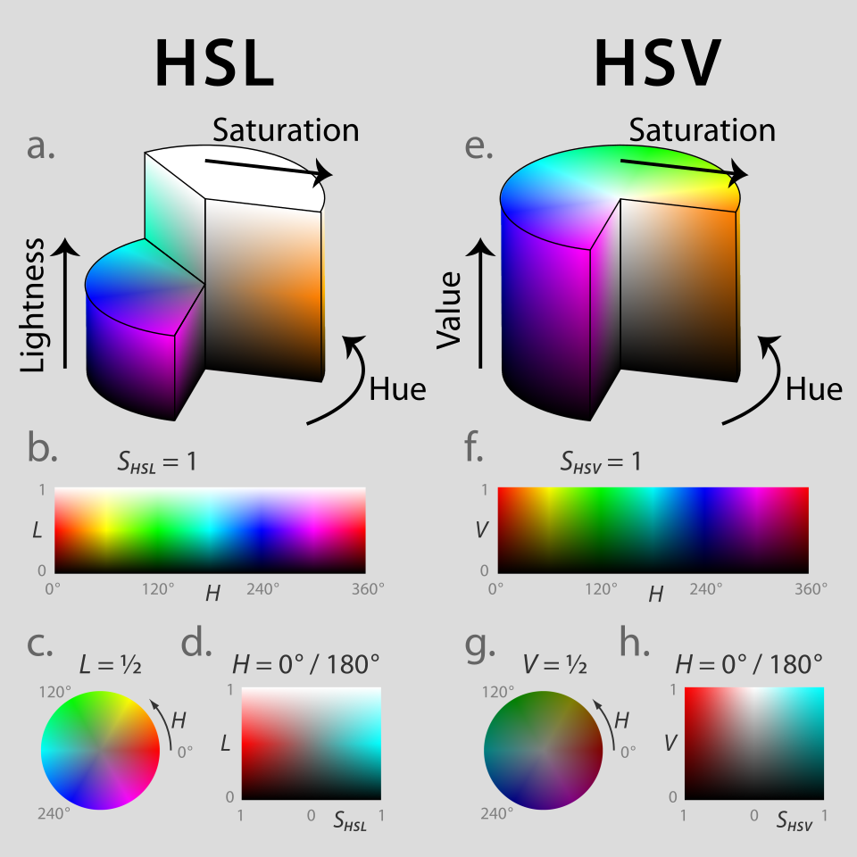
boxes/vision/_resources/datasheets/Hsl-hsv_models.svg.png
