NoBlackBoxes/LastBlackBox/course/_resources/designs/NB3/outline_dark.png

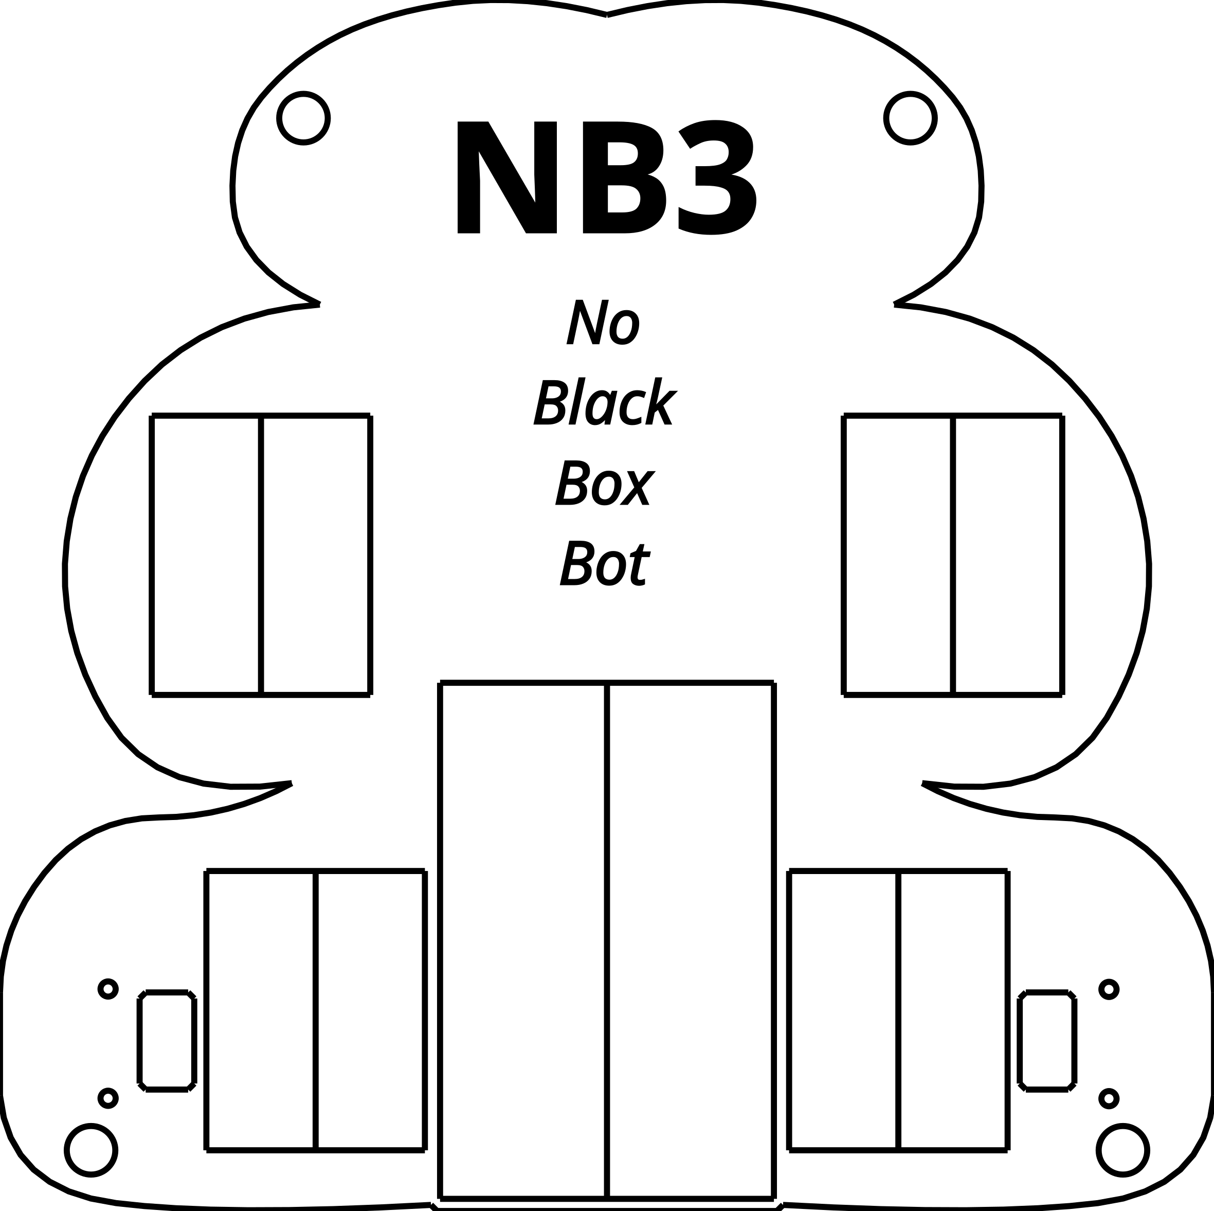
course/_resources/designs/NB3/outline_dark.png
