NoBlackBoxes/LastBlackBox/course/_resources/designs/NB3/outline_light.png

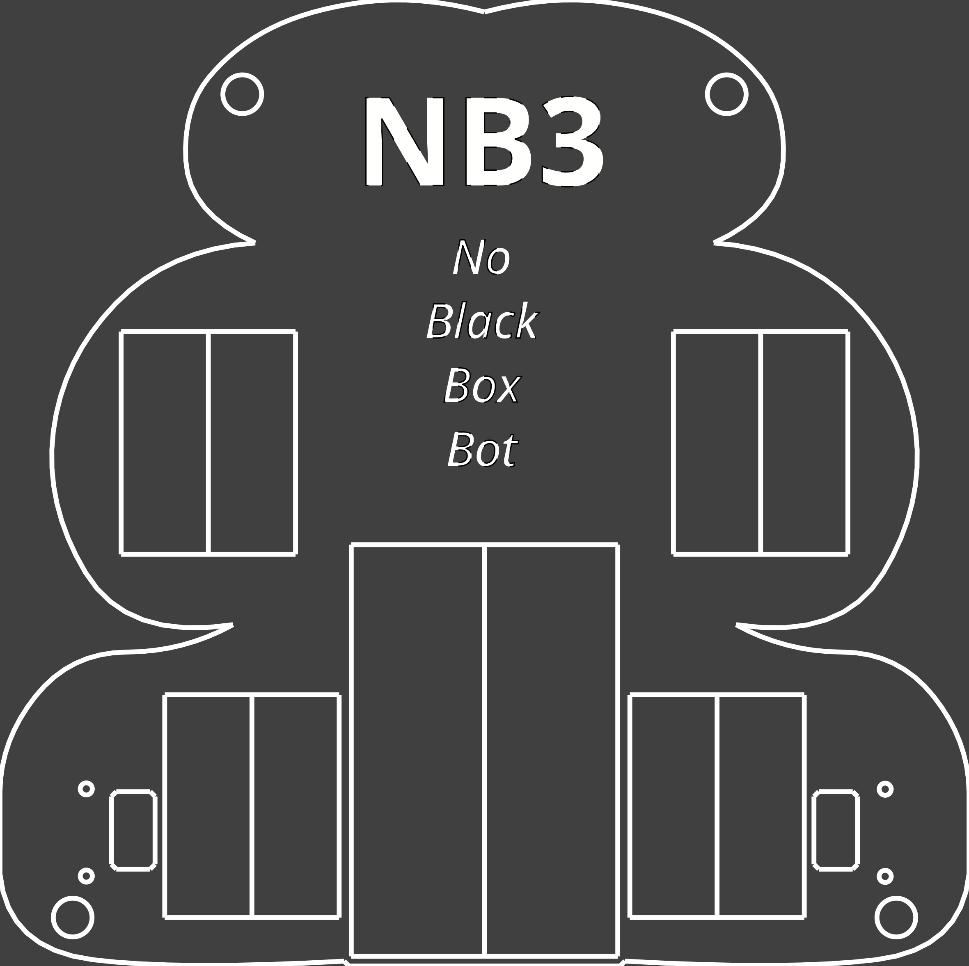
course/_resources/designs/NB3/outline_light.png
