NoBlackBoxes/LastBlackBox/course/versions/ai-workshops/02_vision/_resources/chromebook/images/dog_filter.png

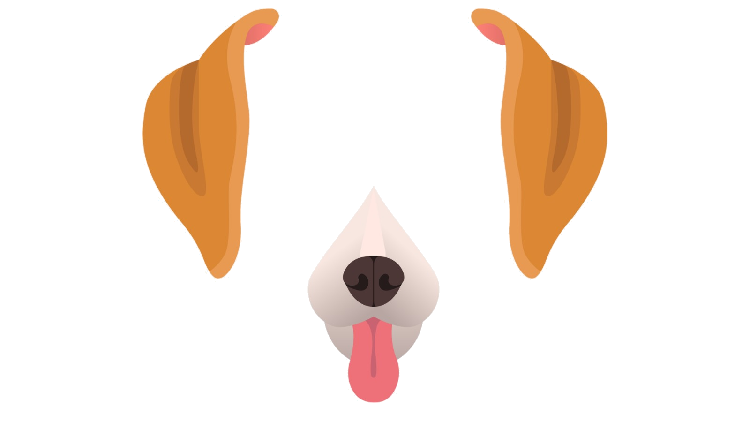
course/versions/ai-workshops/02_vision/_resources/chromebook/images/dog_filter.png
