NoBlackBoxes/LastBlackBox/course/versions/ai-workshops/02_vision/_resources/chromebook/images/epl.webp

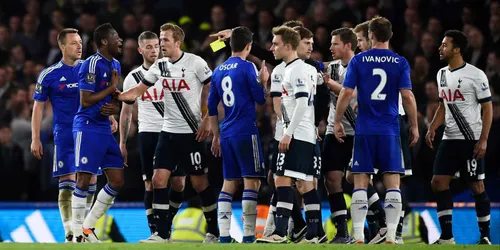
course/versions/ai-workshops/02_vision/_resources/chromebook/images/epl.webp
