NoBlackBoxes/LastBlackBox/course/versions/ai-workshops/02_vision/_resources/chromebook/images/google_ceo.jpg

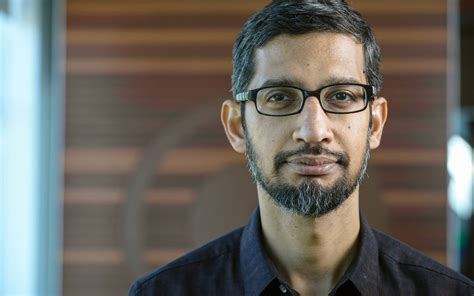
course/versions/ai-workshops/02_vision/_resources/chromebook/images/google_ceo.jpg
