NoBlackBoxes/LastBlackBox/course/versions/ai-workshops/02_vision/_resources/chromebook/images/group_photo.webp

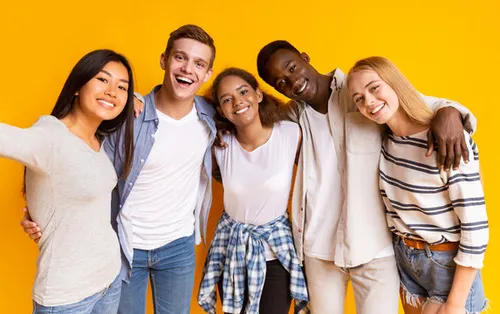
course/versions/ai-workshops/02_vision/_resources/chromebook/images/group_photo.webp
