NoBlackBoxes/LastBlackBox/course/versions/enb/07_microphones-and-speakers/_resources/media/sensor_data_serial_plotter.png

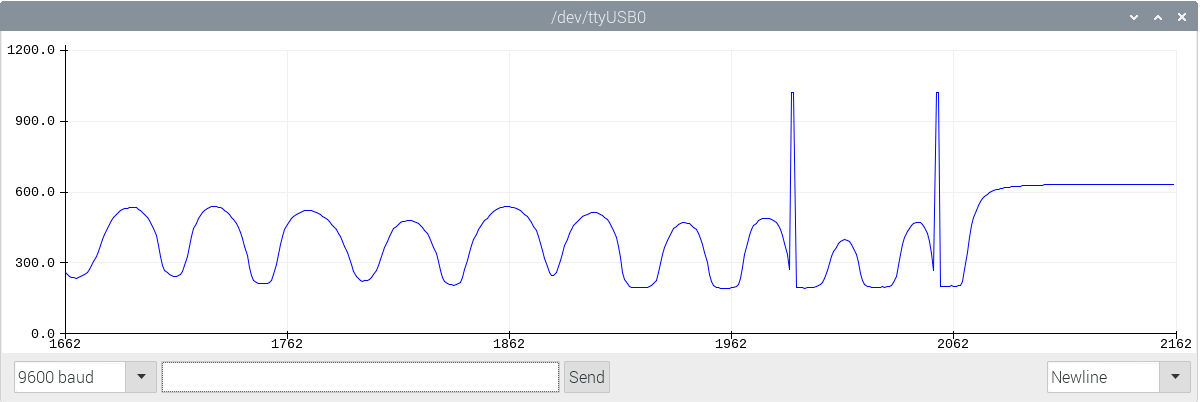
course/versions/enb/07_microphones-and-speakers/_resources/media/sensor_data_serial_plotter.png
