NoBlackBoxes/LastBlackBox/course/versions/enb/08_signal_processing/_resources/media/speech.png

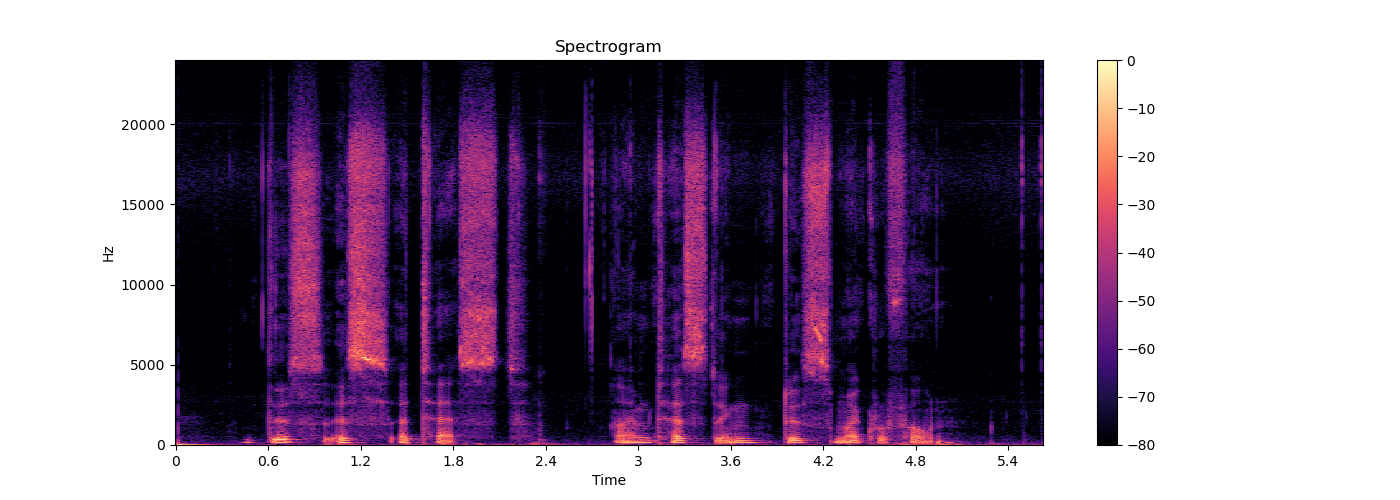
course/versions/enb/08_signal_processing/_resources/media/speech.png
