NoBlackBoxes/LastBlackBox/course/versions/enb/09_cameras/_resources/media/image3.png

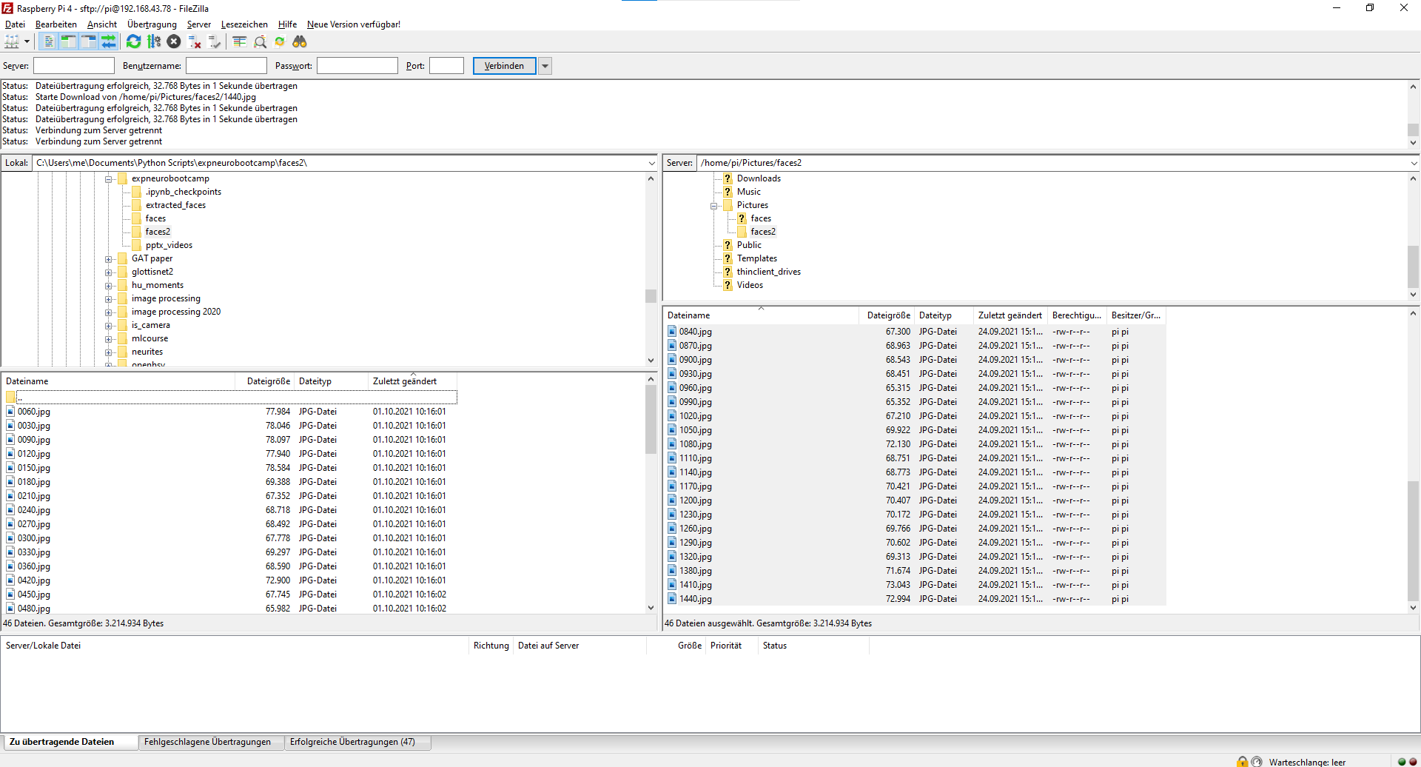
course/versions/enb/09_cameras/_resources/media/image3.png
