NoBlackBoxes/LastBlackBox/course/versions/enb/09_cameras/_resources/media/image3a.png

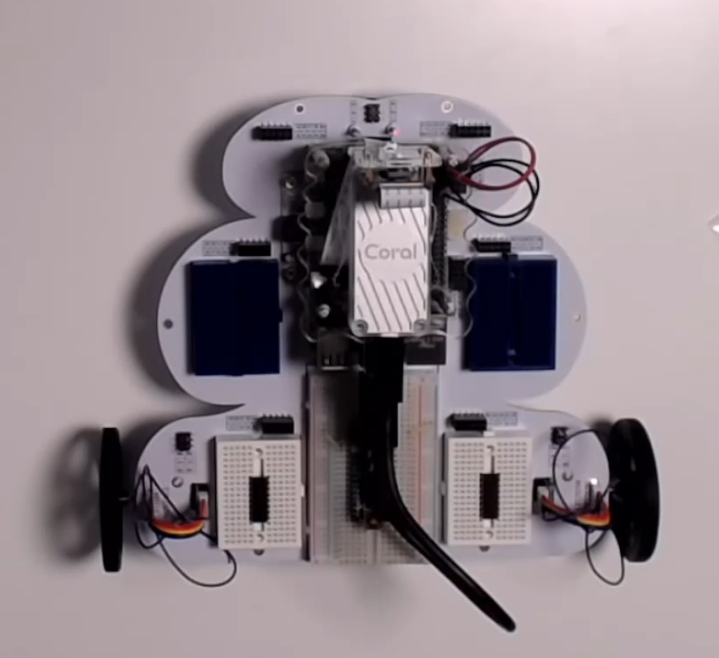
course/versions/enb/09_cameras/_resources/media/image3a.png
