NoBlackBoxes/LastBlackBox/course/versions/enb/09_cameras/_resources/media/image7.png

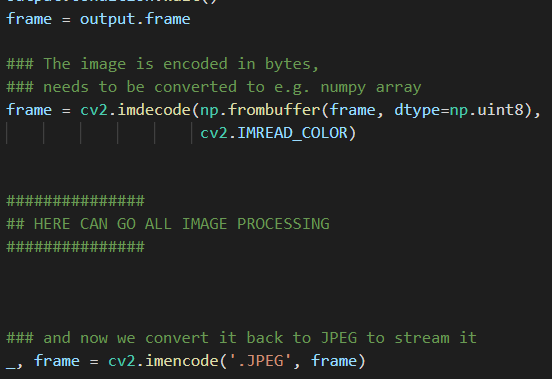
course/versions/enb/09_cameras/_resources/media/image7.png
