NoBlackBoxes/LastBlackBox/course/versions/enb/09_cameras/_resources/media/nb3_camera_stream.png

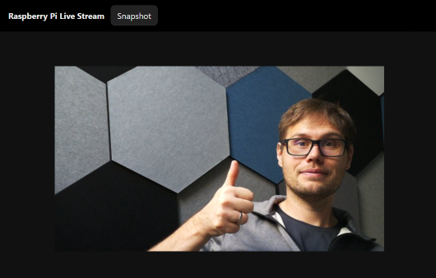
course/versions/enb/09_cameras/_resources/media/nb3_camera_stream.png
