NoBlackBoxes/LastBlackBox/course/versions/enb/09_cameras/_resources/media/nb3_with_camera.png

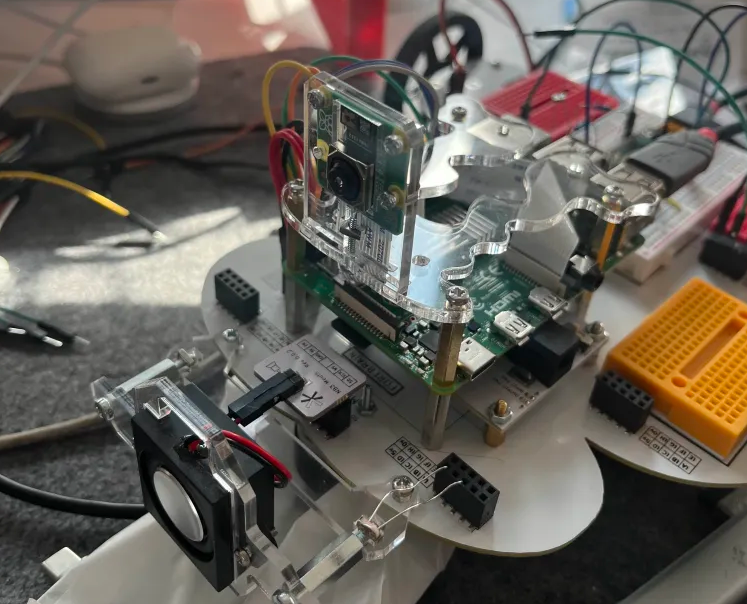
course/versions/enb/09_cameras/_resources/media/nb3_with_camera.png
