NoBlackBoxes/LastBlackBox/course/versions/enb/10_computer-vision/_resources/media/image9.jpeg

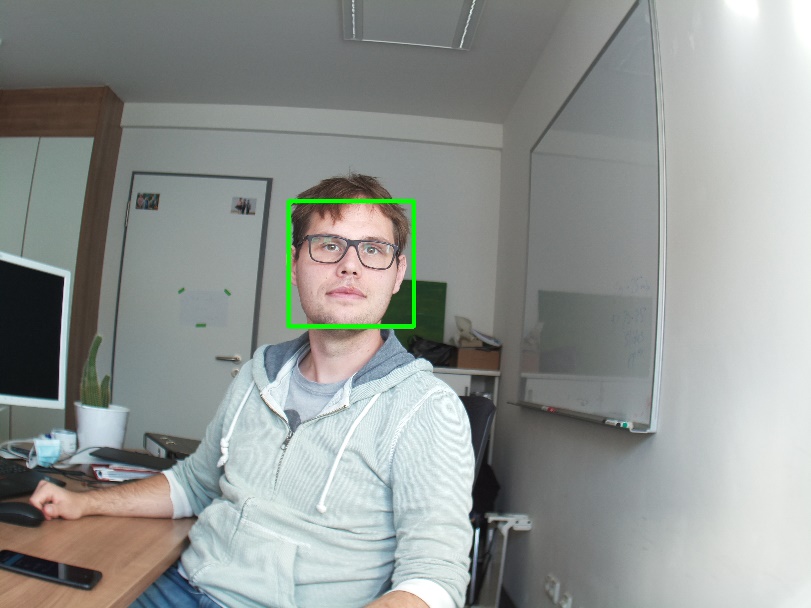
course/versions/enb/10_computer-vision/_resources/media/image9.jpeg
