NoBlackBoxes/LastBlackBox/course/versions/enb/10_computer-vision/_resources/media/image10.jpeg

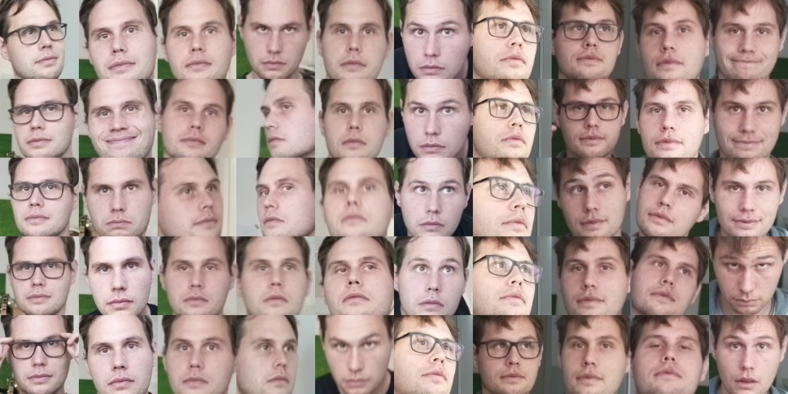
course/versions/enb/10_computer-vision/_resources/media/image10.jpeg
