NoBlackBoxes/LastBlackBox/course/tools/materials/README.md

# course : tools : materials
Generate BOM and packing lists

### Materials Format
Name, Slug, Description, Quantity, Datasheet (optional), Supplier (optional), Package, x(mm), y(mm), z(mm), Unit Price (£), Bulk Price (£), Available (new), Available, (used)

### Package Names
Acrylic Mounts
Active Electronics
Auxiliary
Body (000)
Cables (001)
Circuit Boards
Large (100)
Medium (011)
Mounting Hardware
Passive Electronics
Small (010)
