NoBlackBoxes/LastBlackBox/boxes/electrons/NB3_body/NB3_body.csv

Id | Designator | Footprint | Quantity | Designation | Supplier and ref
3 | J1,J2,J4,J15,J3,J5,J14,J6 | PinSocket_2x05_P2.54mm_Vertical_SMD | 8 | Conn_02x05_Counter_Clockwise
4 | J12,J13 | PinHeader_2x03_P2.54mm_Vertical | 2 | Conn_02x03_Top_Bottom
5 | J7,J9,J8 | PinSocket_2x07_P2.54mm_Vertical_SMD | 3 | Conn_02x07_Odd_Even
7 | J11,J10 | Connector_S4B-PH-SM4-TB(LF)(SN) | 2 | JST SH 4-way Socket
