NoBlackBoxes/LastBlackBox/boxes/power/NB3_charger/NB3_charger.ods

Designator | Quantity | Designation | Supplier | Part Number
BT6,BT2,BT4,BT5,BT1,BT3 | 6 | AA Battery PCB holder (TH) | LCSC | C5290180
J4,J5,J6,J3 | 4 | Pin Header 1x2 (TH) | LCSC | C124375
C6,C4,C3,C18,C19,C1,C5,C17,C2,C20,C12,C14,C15,C13 | 14 | 10uF ±10% 25V X5R 0805 Multilayer Ceramic Capacitors MLCC – SMD/SMT | LCSC | C15850
T1 | 1 | Thermistor NTCG163JF103FT1 | LCSC | C76589
R2 | 1 | 10 Ohms ±1% 1/16W ±100ppm/C 0402 Chip Resistor – Surface Mount | LCSC | C102766
R6 | 1 | 1.6k Ohms ±1% 1/16W ±100ppm/C 0402 Chip Resistor - Surface Mount | LCSC | C4908
D2 | 1 | Red 617.5~633.5nm 0603 Light Emitting Diodes (LED) | LCSC | C7371906
C16 | 1 | 100uF ±10% 10V 700mOhms 100kHz -55C~+125C CASE-D_7343 Tantalum Capacitors | LCSC | C110549
R3 | 1 | 20k Ohms ±1% 1/16W ±100ppm/C 0402 Chip Resistor - Surface Mount | LCSC | C258096
SW2,SW1 | 2 | SPDT Slide Switch SMD, 0.3A 6VDC | LCSC | C221659
R1,R7 | 2 | 5.6k Ohms ±1% 1/16W ±200ppm/C 0402 Chip Resistor - Surface Mount | LCSC | C286562
J1 | 1 | Barrel Jack SMD 2.1 inner, 5.5 outer (TH) | LCSC | C720557
C10 | 1 | 1.2nF ±10% 50V X7R 0603 Multilayer Ceramic Capacitors MLCC – SMD/SMT | LCSC | C79517
R11,R10 | 2 | 15k Ohms ±1% 1/16W ±100ppm/C 0402 Chip Resistor - Surface Mount | LCSC | C114761
D1 | 1 | Emerald 0603 Light Emitting Diodes (LED) | LCSC | C7371903
C9,C11 | 2 | 1nF ±10% 50V X7R 0402 Multilayer Ceramic Capacitors MLCC - SMD/SMT | LCSC | C106205
C7,C8 | 2 | 100nF ±10% 16V X7R 0402 Multilayer Ceramic Capacitors MLCC - SMD/SMT | LCSC | C60474
R8 | 1 | 3.6k Ohms ±1% 1/16W ±200ppm/C 0402 Chip Resistor - Surface Mount | LCSC | C137990
CR1,CR2 | 2 | Schottky Diode, 30V 5A (PMEG3050EP,115) | LCSC | C50603
U2 | 1 | Battery Management 0.8-A one- to six-cell NiMH stand-alone | Mouser | 595-BQ25172DSGR
Q1 | 1 | PMOS, -30V, -4A, 50mOhm | LCSC | C3280198
R4 | 1 | 12k Ohms ±1% 1/16W ±100ppm/C 0402 Chip Resistor - Surface Mount | LCSC | C102781
D3 | 1 | Yellow 0603 Light Emitting Diodes (LED) | LCSC | C7371907
L1 | 1 | 2.2 uH SMD power inductor (5A), SRN6045TA, Bourn | LCSC | C1332316
R5 | 1 | 2.2k Ohms ±1% 1/16W ±100ppm/C 0402 Chip Resistor - Surface Mount | LCSC | C25879
U1 | 1 | DC-DC converter, AP64501, Diodes Inc. | LCSC | C2071517
R9 | 1 | 1.5k Ohms ±1% 1/16W ±100ppm/C 0402 Chip Resistor - Surface Mount | LCSC | C114759
J2 | 1 | 1x4P 4P PH Direct Insert Plugin,P=2mm (JST) | LCSC | C131334
 | `
