NoBlackBoxes/LastBlackBox/boxes/audio/NB3_ear/NB3_ear.ods

Quantity | Designator | Description | Manufactuer | Manufacturer number | Supplier | Supplier number | Unit Price
1 | C1, | 100nF ±10% 16V X7R 0402 Multilayer Ceramic Capacitors MLCC - SMD/SMT | YAGEO | CC0402KRX7R7BB104 | LCSC | C60474 | 0.0012
2 | J1,J2, | Header Breakaway 6 2 Surface Mount 0.100"(2.54mm) SMD P=2.54mm Male | Ckmtw | C124390 | LCSC | C124390 | 0.05
1 | MK1 | MEMS Microphones Multi-Mode Microphone with I S Digital Output | TDK | ICS-43434 | LCSC | C5656610 | 1.34
1 | R1, | 100k Ohms ±1% 1/16W ±100ppm/C 0402 Chip Resistor - Surface Mount | FH | RC-02W1003FT | LCSC | C258090 | 0.0007
