NoBlackBoxes/LastBlackBox/boxes/audio/NB3_mouth/NB3_mouth.ods

Quantity | Designator | Description | Manufacturer | Manufacturer number | Supplier | Supplier number | Unit Price
1 | IC1 | MAX98357A | Maxim | MAX98357AETE+T | LCSC | C910544 | 1.1
1 | C1 | 10uF ±10% 25V X5R 0805 Multilayer Ceramic Capacitors MLCC - SMD/SMT | Samsung | CL21A106KAYNNNE | LCSC | C15850 | 0.018
1 | R1 | 62.5mW Thick Film Resistors ±100ppm/℃ ±1% 634kΩ 0402 Chip Resistor – SMD | YAGEO | RC0402FR-07634KL | LCSC | C273705 | 0.0006
1 | C2 | 100nF ±10% 16V X7R 0402 Multilayer Ceramic Capacitors MLCC - SMD/SMT | YAGEO | CC0402KRX7R7BB104 | LCSC | C60474 | 0.0012
2 | J1,J2, | Header Breakaway 6 2 Surface Mount 0.100"(2.54mm) SMD P=2.54mm Male | Ckmtw | C124390 | LCSC | C124390 or C780054 | 0.05
1 | J3 | Right-Angle Square Pins 2.5mm 2P 6mm -40℃~+105℃ 2.54mm Plugin Black Brass 1x2P Push-Pull,P=2.54mm Pin Headers ROHS | XFCN | PZ254R-11-02P | LCSC | C492410 | 0.012
