NoBlackBoxes/LastBlackBox/boxes/power/NB3_power/NB3_power.ods

Quantity | Designator | Description | Manufactuer | Manufacturer number | Supplier | Supplier number | Unit Price
10 | C1, C2, C3, C4, C5, C6, C12, C13, C14, C15, | 10uF ±10% 25V X5R 0805 Multilayer Ceramic Capacitors MLCC - SMD/SMT | Samsung | CL21A106KAYNNNE | LCSC | C15850 | 0.018
2 | C7, C8, | 100nF ±10% 16V X7R 0402 Multilayer Ceramic Capacitors MLCC - SMD/SMT | YAGEO | CC0402KRX7R7BB104 | LCSC | C60474 | 0.0012
2 | C9, C11, | 1nF ±10% 50V X7R 0402 Multilayer Ceramic Capacitors MLCC - SMD/SMT | YAGEO | CC0402KRX7R9BB102 | LCSC | C106205 | 0.0012
1 | C10, | 1.2nF ±10% 50V X7R 0603 Multilayer Ceramic Capacitors MLCC - SMD/SMT | FH | 0603B122K500NT | LCSC | C79517 | 0.004
1 | C16, | 100uF ±10% 10V 700mOhms 100kHz -55C~+125C CASE-D_7343 Tantalum Capacitors | KEMET | T491D107K010AT | LCSC | C110549 | 0.6835
1 | D1, | Green-yellow 569.5~577.5nm 0603 Light Emitting Diodes (LED) | Everlight Elec | 19-217/G7C-AN1P2/3T | LCSC | C72042 | 0.0199
1 | D2, | Red 617.5~633.5nm 0603 Light Emitting Diodes (LED) | Everlight Elec | 19-217/R6C-AL1M2VY/3T | LCSC | C72044 | 0.0157
1 | J1, | Barrel Jack SMD 2.1 inner, 5.5 outer, CUI | CUI | PJ-036AH-SMT-TR | Digi-Key | CP-036AHPJCT-ND | 0.99
1 | J2, | PH Header Male Pin 0.079"(2.00mm) 4 SMD,P=2mm Wire To Board / Wire To Wire | JST | S4B-PH-SM4-TB(LF)(SN) | LCSC | C265102 | 0.2873
1 | J3, | Right-Angle Square Pins 2.5mm 2P 6mm -40℃~+105℃ 2.54mm Plugin Black Brass 1x2P Push-Pull,P=2.54mm Pin Headers ROHS | XFCN | PZ254R-11-02P | LCSC | C492410 | 0.012
1 | L1, | 2.2 uH SMD power inductor (5A), SRN6045TA, Bourn | Bourn | SRN6045TA-2R2Y | LCSC | C1332316 | 0.2637
1 | R1, | 5.6k Ohms ±1% 1/16W ±200ppm/C 0402 Chip Resistor - Surface Mount | FH | RC-02W5601FT | LCSC | C286562 | 0.0007
1 | R2, | 10 Ohms ±1% 1/16W ±100ppm/C 0402 Chip Resistor – Surface Mount | RALEC | RTT0210R0FTH | LCSC | C102766 | 0.0065
1 | R3, | 20k Ohms ±1% 1/16W ±100ppm/C 0402 Chip Resistor - Surface Mount | FH | RC-02W2002FT | LCSC | C258096 | 0.0008
1 | R4, | 12k Ohms ±1% 1/16W ±100ppm/C 0402 Chip Resistor - Surface Mount | RALEC | RTT021202FTH | LCSC | C102781 | 0.0036
1 | R5, | 2.2k Ohms ±1% 1/16W ±100ppm/C 0402 Chip Resistor - Surface Mount | UNI-ROYAL | 0402WGF2201TCE | LCSC | C25879 | 0.0009
1 | R6, | 1.6k Ohms ±1% 1/16W ±100ppm/C 0402 Chip Resistor - Surface Mount | UNI-ROYAL | 0402WGF1601TCE | LCSC | C4908 | 0.0007
1 | SW1, | SPDT Slide Switch SMD, 0.3A 6VDC | C&K | JS102011JCQN | LCSC | C221659 | 0.9937
1 | U1, | DC-DC converter, AP64501, Diodes Inc. | Diodes Inc | AP64501SP-13 | LCSC | C2071517 | 1.73
30
