NoBlackBoxes/LastBlackBox/boxes/fpgas/NB3_hindbrain/NB3_hindbrain.ods

Quantity | Designator | Description | Manufactuer | Manufacturer number | Supplier | Supplier number | Unit Price | Total Price
8 | C32,C14,C15,C30,C39,C21,C36,C23 | 10uF ±20% 6V 0603 Multilayer Ceramic Capacitors MLCC - SMD/SMT | Samsung | CL10A106MQ8NNNC | LCSC | C1691 | 0.002 | 0.016
6 | C13,C5,C18,C25,C29,C22 | 4.7uF ±10% 10V 0603 Multilayer Ceramic Capacitors MLCC - SMD/SMT | Samsung | CL10A475KP8NNNC | LCSC | C1705 | 0.0053 | 0.0318
24 | C38,C7,C11,C12,C28,C24,C10,C1,C26,C9,C37,C2,C17,C34,C16,C19,C6,C3,C4,C33,C31,C20,C27,C8 | 100nF ±10% 16V X7R 0402 Multilayer Ceramic Capacitors MLCC - SMD/SMT | YAGEO | CC0402KRX7R7BB104 | LCSC | C60474 | 0.0012 | 0.0288
16 | R48,R17,R37,R32,R53,R16,R44,R36,R21,R49,R52,R20,R33,R45,R40,R41 | 3.3 MOhms ±1% 1/16W ±100ppm/C 0402 Chip Resistor - Surface Mount | YAGEO | RC0402FR-073M3L | LCSC | C470023 | 0.0009 | 0.0144
4 | R29,R27,R23,R25 | 33 kOhms ±1% 1/16W ±100ppm/C 0402 Chip Resistor - Surface Mount | UNI-ROYAL | 0402WGF3302TCE | LCSC | C25779 | 0.0005 | 0.002
4 | R24,R28,R26,R22 | 16.9 kOhms ±1% 1/16W ±100ppm/C 0402 Chip Resistor - Surface Mount | YAGEO | RC0402FR-0716K9L | LCSC | C163488 | 0.0007 | 0.0028
1 | R5 | 12 kOhms ±1% 1/16W ±100ppm/C 0402 Chip Resistor - Surface Mount | UNI-ROYAL | 0402WGF1202TCE | LCSC | C25752 | 0.0005 | 0.0005
7 | R2,R12,R4,R15,R13,R11,R1 | 10 kOhms ±1% 1/16W ±100ppm/C 0402 Chip Resistor - Surface Mount | YAGEO | RC0402FR-0710KL | LCSC | C60490 | 0.0006 | 0.0042
1 | R3 | 2.2 kOhms ±1% 1/16W ±100ppm/C 0402 Chip Resistor - Surface Mount | UNI-ROYAL | 0402WGF2201TCE | LCSC | C25879 | 0.0005 | 0.0005
1 | R6 | 1 kOhms ±1% 1/16W ±100ppm/C 0402 Chip Resistor - Surface Mount | UNI-ROYAL | 0402WGF1001TCE | LCSC | C11702 | 0.0005 | 0.0005
19 | R30,R8,R38,R47,R51,R54,R18,R43,R19,R7,R55,R9,R31,R34,R35,R42,R39,R50,R46 | 330 Ohms ±1% 1/16W ±100ppm/C 0402 Chip Resistor - Surface Mount | UNI-ROYAL | 0402WGF3300TCE | LCSC | C25104 | 0.0006 | 0.0114
1 | R14 | 100 Ohms ±1% 1/16W ±100ppm/C 0402 Chip Resistor - Surface Mount | UNI-ROYAL | 0402WGF1000TCE | LCSC | C25076 | 0.0005 | 0.0005
1 | D1 | 5 mA SMD 0402 Blue LED | Yongyu | SZYY0402W | LCSC | C434448 | 0.0143 | 0.0143
9 | D17,D7,D11,D13,D15,D19,D9,D21,D3 | 5 mA SMD 0402 Blue LED | Yongyu | SZYY0402B | LCSC | C434447 | 0.0159 | 0.1431
9 | D10,D20,D14,D12,D2,D8,D6,D18,D16 | 5 mA SMD 0402 Red LED | Yongyu | SZYY0402R | LCSC | C434445 | 0.0139 | 0.1251
1 | D4 | ESD suppressors / TVS diodes | Nexperia | PRTR5V0U2F-115 | LCSC | C478118 | 0.3241 | 0.3241
1 | D5 | Fast switching diode: FV 0.8V @ 2.5 mA | Diodes Inc. | 1N4148WS-7-F | LCSC | C60580 | 0.009 | 0.009
1 | RGB1 | Surface mount high-intensity RGB LED | Cree | CLMVC-FKA-CLBDGL7LBB79353 | Mouser | 941-CLMVCFKACLBDGL7L | 0.17 | 0.17
2 | FB2,FB1 | GHz noise suppression SMD ferrite bead | Murata | BLM18HE152SN1D | LCSC | C82155 | 0.0262 | 0.0524
16 | Q6,Q11,Q8,Q16,Q15,Q9,Q7,Q3,Q5,Q12,Q10,Q1,Q2,Q13,Q14,Q4 | SOT-723 N-Ch - 1.2 V gate | Rohm | RUM001L02T2CL | LCSC | C253528 | 0.0167 | 0.2672
1 | VR1 | Low dropout voltage regulator 800mA 1.2V | STM | LD1117S12TR | LCSC | C155612 | 0.2135 | 0.2135
1 | VR2 | Low dropout voltage regulator 800mA 3.3V | Texas Instruments | LM1117IMPX-3.3 | LCSC | C23984 | 0.4455 | 0.4455
1 | F1 | PTC 6V 750 mA trip | Bourns | MF-FSMF035X-2 | LCSC | C116602 | 0.0245 | 0.0245
1 | Y1 | Clock oscillators 12MHz 1.6-3.6V | ECS | ECS-2520MV-120-BN-TR | Mouser | 520-2520MV-120-BN-T | 0.89 | 0.89
1 | U1 | 2K microwire compatible serial EEPROM | Microchip | 93LC56BT-I/OT | LCSC | C190271 | 0.8448 | 0.8448
1 | IC1 | USB HS interface IC to dual UART/FIFO/SPI/JTAG/I2C | FTDI | FT2232HQ | Mouser | 895-FT2232HQ | 4.07 | 4.07
1 | IC2 | Lattice ICE40 UltraPlus 5280 LUTs 1.2V | Lattice | ICE40UP5K-SG48I | Mouser | 842-ICE40UP5K-SG48I | 7.13 | 7.13
1 | IC3 | 32M-bit 4Kb uniform sector SPI flash | WinBond | W25Q32JVSSIQ | LCSC | C179173 | 0.2618 | 0.2618
1 | IC4 | 10-bit SPI 4 channel ADC | Microchip | MCP3004-I/SL | Mouser | 579-MCP3004-I/SL | 2.13 | 2.13
1 | IC5 | 10-bit SPI 2 channel DAC | Microchip | MCP4812-E/SN | Mouser | 579-MCP4812-E/SN | 2.16 | 2.16
1 | J1 | Micro yype-B USB 2.0 SMD socket | Amphenol | 10103594-0001LF | LCSC | C428495 | 0.5298 | 0.5298
2 | J3,J2 | 1x20 2.54 mm through-hole pin header | BOOMELE | C50981 | LCSC | C50981 | 0.091 | 0.182
145 |  |  |  |  |  |  |  | 20.1005
