NoBlackBoxes/LastBlackBox/boxes/electrons/NB3_body/fab/NB3_body.xlsx

Quantity | Designator | Description | Manufactuer | Manufacturer number | Supplier | Supplier number | Unit Price
2 | J12,J13 | Male Header 2x03 Through-Hole 2.54mm P=2.54mm | XFCN | PZ254V-12-6P | LCSC | C492420 | 0.0354
8 | J1,J2,J4,J15,J3,J5,J14,J6 | Female Header 2x05 Surface Mount 2.54mm SMD P=2.54mm | BOOMELE | 2.54-2*5P | LCSC | C261072 | 0.1428
3 | J7,J9,J8 | Female Header 2x07 Surface Mount 2.54mm SMD P=2.54mm | BOOMELE | 2.54-2*7P | LCSC | C84005 | 0.2098
2 | J11,J10 | PH Header Male Pin 0.079"(2.00mm) 4 SMD P=2mm Wire To Board / Wire To Wire | JST | S4B-PH-SM4-TB(LF)(SN) | LCSC | C265102 | 0.2873
