NoBlackBoxes/LastBlackBox/boxes/vision/NB3_cortex_mount/NB3_cortex_mount.dxf

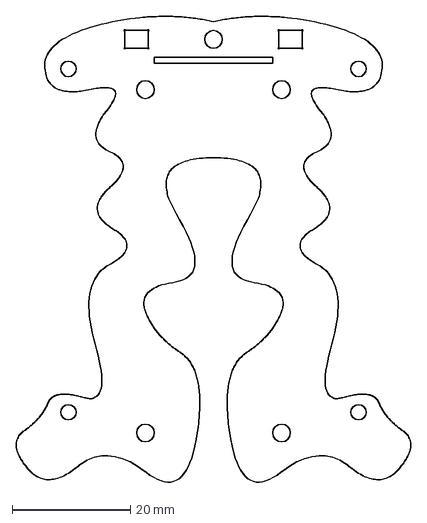
[picture p193: CAD file, 2024-08-30]
boxes/vision/NB3_cortex_mount/NB3_cortex_mount.dxf
66.7 x 78.8 mm
