NoBlackBoxes/LastBlackBox/boxes/vision/NB3_mounts/NB3_camera_mount.dxf

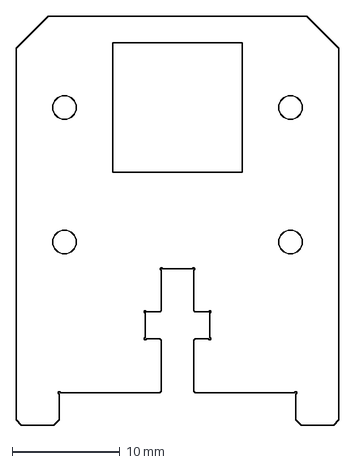
[picture p194: CAD file, 2023-09-02]
boxes/vision/NB3_mounts/NB3_camera_mount.dxf
30.0 x 38.0 mm
