NoBlackBoxes/LastBlackBox/course/_resources/packaging/CAD/boxes/Medium.step

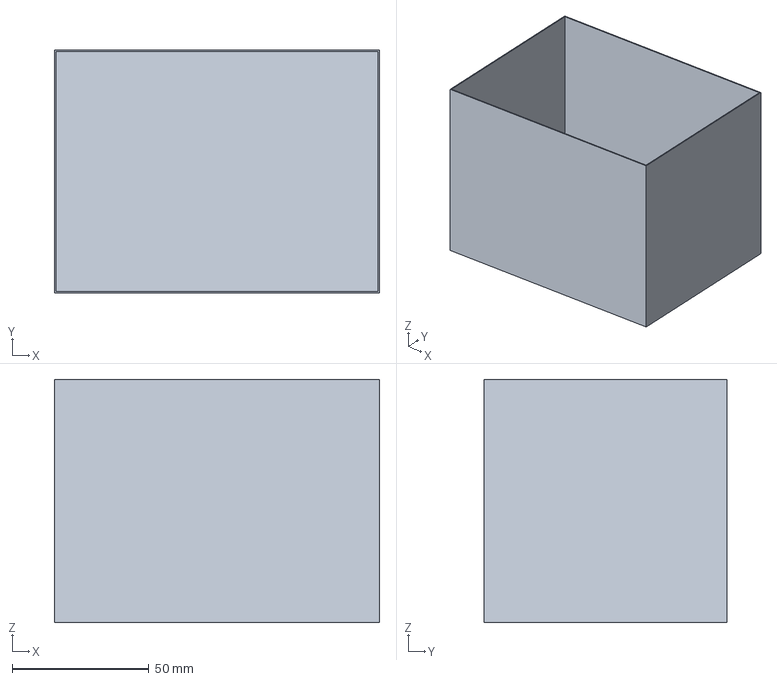
[picture p195: CAD file, 2025-02-15]
course/_resources/packaging/CAD/boxes/Medium.step
119.0 x 89.0 x 89.0 mm
