NoBlackBoxes/LastBlackBox/course/_resources/packaging/CAD/items/bootcamp/Cables/Cable__Mini_USB_20cm__networks_0.step

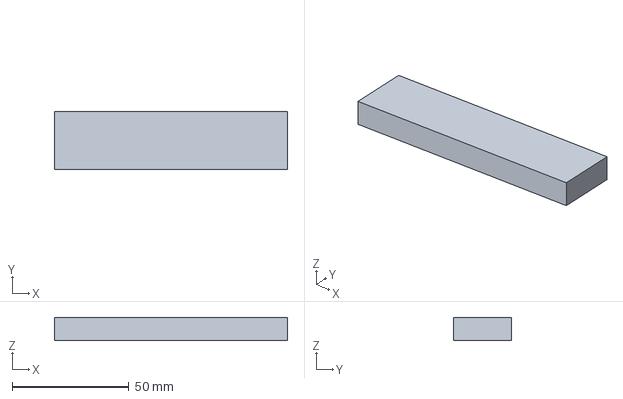
[picture p196: CAD file, 2025-01-30]
course/_resources/packaging/CAD/items/bootcamp/Cables/Cable__Mini_USB_20cm__networks_0.step
100.0 x 25.0 x 10.0 mm
