NoBlackBoxes/LastBlackBox/course/_resources/packaging/CAD/items/course/Active/LM386N_4_NOPB_amplifiers_1.step

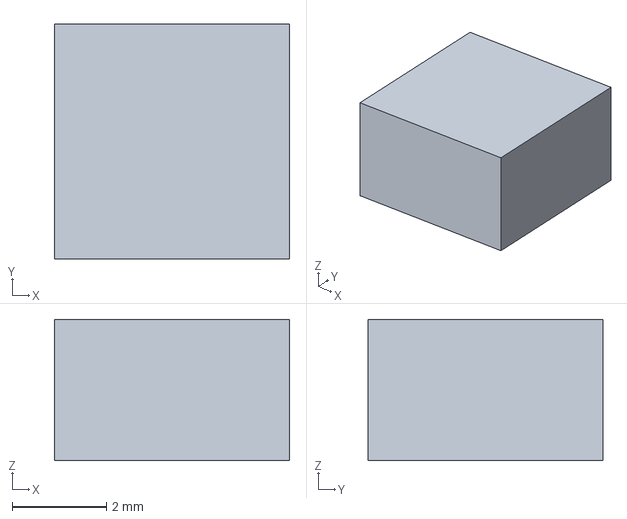
[picture p197: CAD file, 2025-01-30]
course/_resources/packaging/CAD/items/course/Active/LM386N_4_NOPB_amplifiers_1.step
5.00 x 5.00 x 3.00 mm
