NoBlackBoxes/LastBlackBox/course/designs/logo/cut_text.dxf

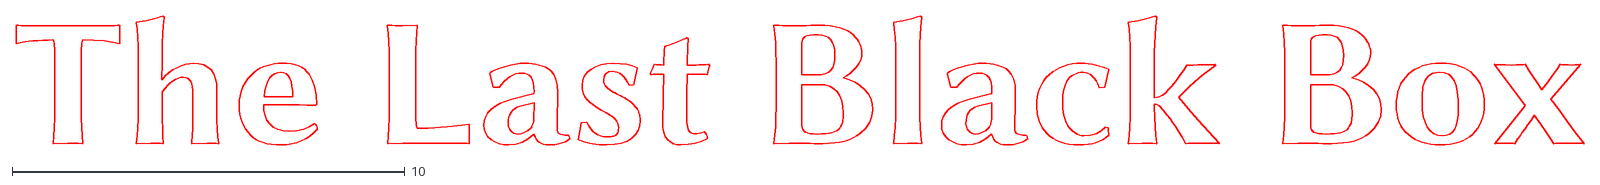
[picture p198: CAD file, 2020-09-04]
course/designs/logo/cut_text.dxf
39.9 x 3.28
