NoBlackBoxes/LastBlackBox/boxes/intelligence/NB3_skull/NB3_skull-midbrain_offset.dxf

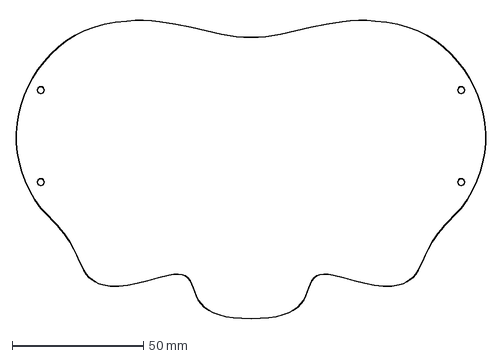
[picture p199: CAD file, 2025-01-26]
boxes/intelligence/NB3_skull/NB3_skull-midbrain_offset.dxf
178.6 x 115.1 mm
