NoBlackBoxes/LastBlackBox/course/_resources/packaging/CAD/boxes/Cables.step

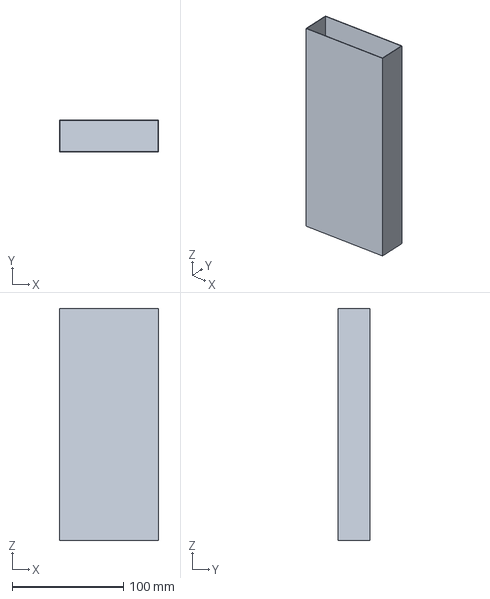
[picture p200: CAD file, 2025-02-15]
course/_resources/packaging/CAD/boxes/Cables.step
89.0 x 29.0 x 209.0 mm
