NoBlackBoxes/LastBlackBox/course/designs/logo/cut_logo.dxf

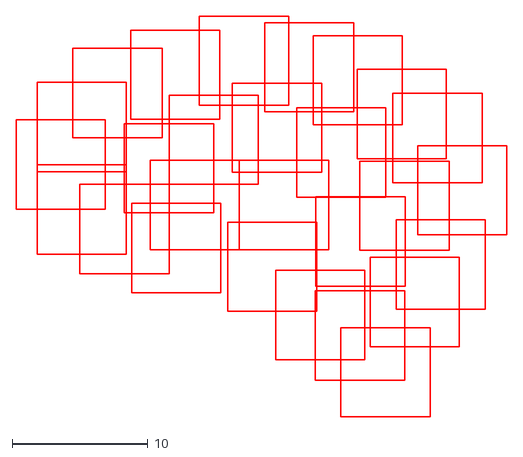
[picture p201: CAD file, 2020-09-04]
course/designs/logo/cut_logo.dxf
36.1 x 29.5
