NoBlackBoxes/LastBlackBox/boxes/intelligence/NB3_skull/NB3_skull_forebrain_offset.dxf

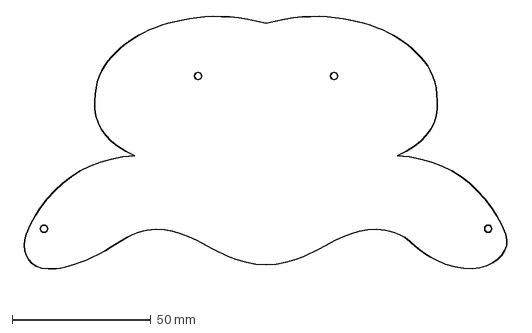
[picture p202: CAD file, 2025-01-26]
boxes/intelligence/NB3_skull/NB3_skull_forebrain_offset.dxf
179.9 x 99.5 mm
