NoBlackBoxes/LastBlackBox/course/_resources/packaging/CAD/boxes/Small.step

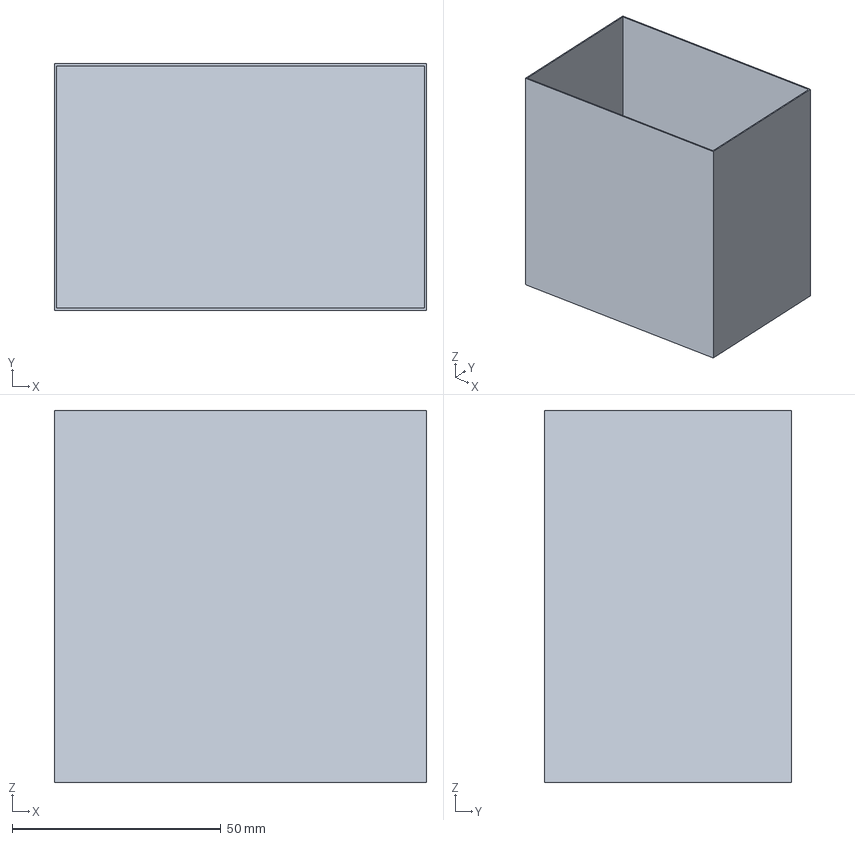
[picture p203: CAD file, 2025-02-15]
course/_resources/packaging/CAD/boxes/Small.step
89.0 x 59.0 x 89.0 mm
