NoBlackBoxes/LastBlackBox/course/designs/logo/cut.dxf

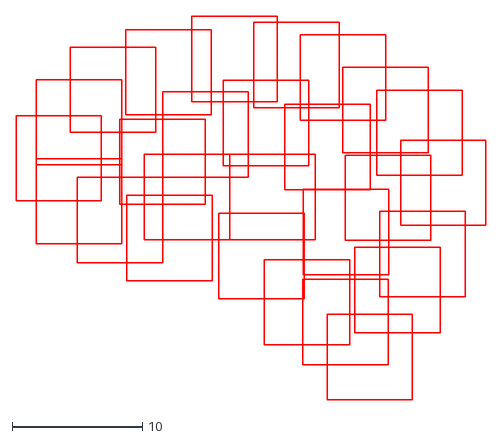
[picture p204: CAD file, 2020-09-04]
course/designs/logo/cut.dxf
36.1 x 29.5
