NoBlackBoxes/LastBlackBox/boxes/intelligence/NB3_skull/NB3_skull-midbrain.dxf

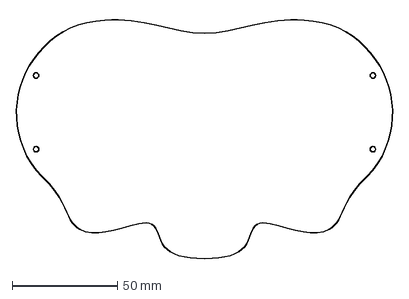
[picture p205: CAD file, 2025-01-26]
boxes/intelligence/NB3_skull/NB3_skull-midbrain.dxf
178.6 x 115.1 mm
