NoBlackBoxes/LastBlackBox/course/_resources/packaging/CAD/boxes/Large.step

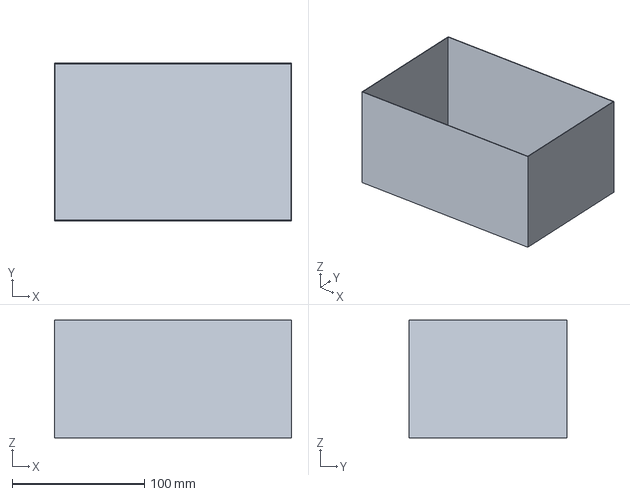
[picture p206: CAD file, 2025-02-15]
course/_resources/packaging/CAD/boxes/Large.step
179.0 x 119.0 x 89.0 mm
