NoBlackBoxes/LastBlackBox/boxes/intelligence/NB3_skull/NB3_skull_forebrain.dxf

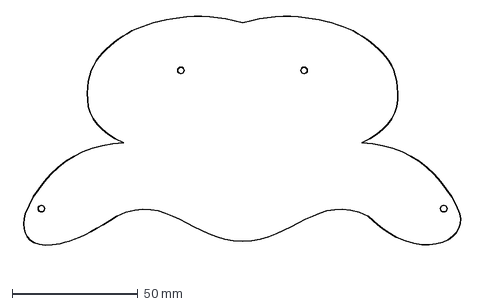
[picture p207: CAD file, 2025-01-26]
boxes/intelligence/NB3_skull/NB3_skull_forebrain.dxf
179.9 x 99.5 mm
