NoBlackBoxes/LastBlackBox/boxes/intelligence/NB3_skull/logo_NBB_black_text.dxf

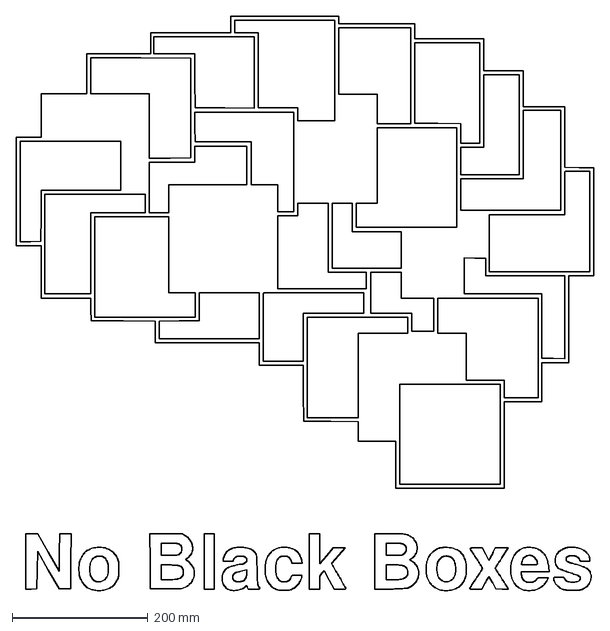
[picture p208: CAD file, 2025-01-26]
boxes/intelligence/NB3_skull/logo_NBB_black_text.dxf
851.0 x 846.0 mm
