NoBlackBoxes/LastBlackBox/course/_resources/packaging/CAD/boxes/Mailer.step

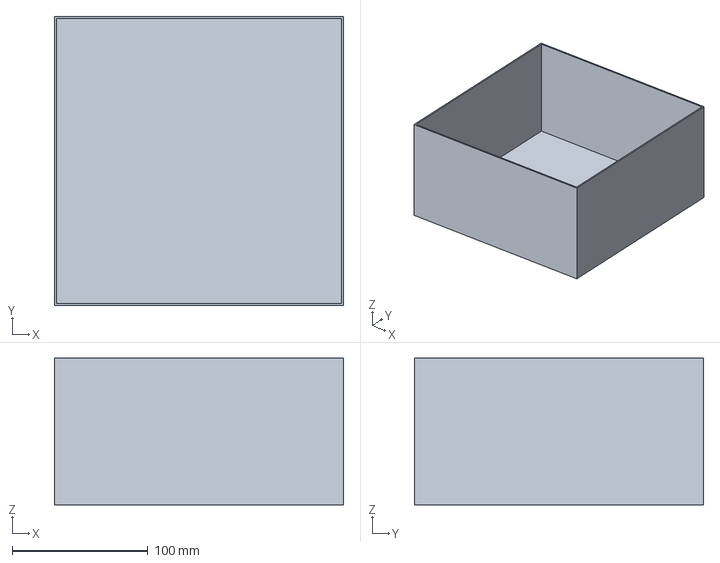
[picture p209: CAD file, 2025-02-15]
course/_resources/packaging/CAD/boxes/Mailer.step
213.0 x 213.0 x 108.0 mm
