NoBlackBoxes/LastBlackBox/boxes/intelligence/NB3_skull/NB3_skull-hindbrain.dxf

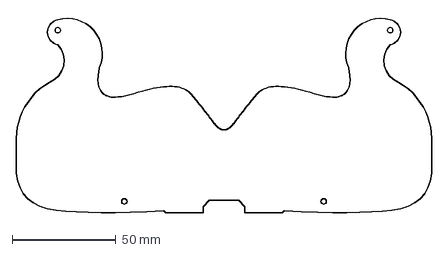
[picture p210: CAD file, 2025-01-26]
boxes/intelligence/NB3_skull/NB3_skull-hindbrain.dxf
200.0 x 94.8 mm
