NoBlackBoxes/LastBlackBox/boxes/intelligence/NB3_skull/NB3_skull.dxf

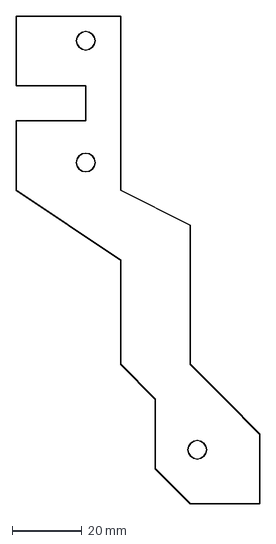
[picture p211: CAD file, 2025-01-24]
boxes/intelligence/NB3_skull/NB3_skull.dxf
70.0 x 140.0 mm
