NoBlackBoxes/LastBlackBox/boxes/control/_resources/lessons/NB3_Building-a-PWM-Speed-Controller.md

# Control : NB3 : Building a PWM Speed Controller
We can use a digital (binary) signal and a MOSFET to turn a motor **ON** and **OFF**. We can use PWM to change the motor's speed.

## [Video](https://vimeo.com/1033891821)

## Concepts
- Build a PWM circuit
- Test the code

## Lesson
