NoBlackBoxes/LastBlackBox/boxes/data/_resources/lessons/NB3_Build-an-ADC-input.md

# Data : NB3 : Build an ADC (input)
Use a comparator to convert analog values into discrete levels.

## [Video](https://vimeo.com/1034767170)

## Concepts
- Build a resistor ladder
- Connect comparator
- *Note*: The LM339 output connects to ground (open collector) when the **-** input is greater than th e **+** input.

## Lesson
