NoBlackBoxes/LastBlackBox/boxes/electrons/_resources/lessons/NB3_Building-Voltage-Dividers.md

# Electrons : NB3 : Building Voltage Dividers
Step-by-step guide to building and testing voltage dividers with discrete resistors and a potentiometer.

## [Video](https://vimeo.com/1030790826)

## Concepts
- Pretty simple.
- Build and measure a voltage divider circuit with two fixed resistors of the same size, and different.
- Explain potentiometer installation and use.
- How potentiometers fail...as variable resistors.

## Lesson
