NoBlackBoxes/LastBlackBox/boxes/logic/_resources/lessons/NB3_Build-an-ADC-output.md

# Logic : NB3 : Build an ADC (output)
Use a comparator to convert analog values into discrete levels.

## [Video]()

## Concepts
- Build a priority encoder (2-bit or 3-bit?)

## Lesson
