NoBlackBoxes/LastBlackBox/course/versions/buildabrain/05_build-a-robot/_resources/guide.md

# Teaching Guide

## Topics
- Robotics: "Braitenberg Vehicles" and sensorimotor loops
- Servo motors (controlling hobby servos with digital pulses)
- Microcontoller programming ("servo" library)

## Goal
Build a Braitenberg Vehicle
- Attach servo motors and wheels to the NB3
  - Test the servos
- Attach a ball caster (third wheel) to the NB3
- Measure values from a light sensor and use these values to adjust the speed of the servo motors

## Tools
- Light sources (e.g. phone torch) to guide the robots

## Steps
> lecture - **practical** - *optional*

- (05:005) Sensorimotor Loops: simple circuits, complex behaviour
- (05:010) "Braitenberg Vehicles"
- (05:015) Servo Motors: function and control
- (15:030) **Attach your NB3's muscles (servo motors)**
- (10:040) **Attach your NB3's ball caster**
- (10:050) **Test your servo motors**
- (10:060) How to program a Braitenberg Vehicle using Arduino
- (90:150) **Building (and programming) a Braitenberg Vehicle**
