NoBlackBoxes/LastBlackBox/course/versions/buildabrain/06_the-software-stack/_resources/guide.md

# Teaching Guide

## Topics
- SoC (system-on-chip)
- SBC (single-board computer)
- Operating system
- Linux command line
- VS code
- Python

## Goal

## Tools

## Steps
