NoBlackBoxes/LastBlackBox/boxes/memory/_resources/lessons/NB3_Building-an-SR-Latch.md

# Memory : NB3 : Building an SR Latch
Let's build and test an SR latch from NAND gates.

## [Video](https://vimeo.com/1033234541)

## Concepts

## Lesson
- Build an SR latch, follow the video guide
