NoBlackBoxes/LastBlackBox/course/versions/buildabrain/07_how-the-internet-works/_resources/guide.md

# Teaching Guide

## Topics
- Networks and protocols (HTTP)
- HTML/CSS/Javascript
- Browsers
- Servers

## Goal

## Tools

## Steps
