NoBlackBoxes/LastBlackBox/course/versions/buildabrain/08_artificial-intelligence/_resources/guide.md

# Teaching Guide

## Topics
- Digital signal processing (FFT)
- Computer vision (blob tracking)
- Machine learning (neural networks and transfer learning)
- AI (LLMs via APIs)

## Goal

## Tools

## Steps
