NoBlackBoxes/LastBlackBox/course/versions/ai-workshops/02_vision/_resources/chromebook/setup.md

# Vision Workshop Setup (Chromebook / Linux)

## Install Visual Studio Code

https://github.com/NoBlackBoxes/LastBlackBox/blob/ac1b994161ca0613f8d21e692abad5cec0fe67aa/boxes/systems/chromeos/README.md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

## Open VS Code, run:

``` bash
mkdir NoBlackBoxes
cd NoBlackBoxes
```

## Clone the repository (master branch, depth 1)

``` bash
git clone --branch master --depth 1 https://github.com/NoBlackBoxes/LastBlackBox.git
```

## Go to the workshop folder

``` bash
cd ~/NoBlackBoxes/LastBlackBox/course/versions/ai-workshops/02_vision/_resources/chromebook
```

## Check Python and install venv support

``` bash
python3 --version
sudo apt update
sudo apt install python3.11-venv
```

## Create and activate the virtual environment

``` bash
python3 -m venv vision_env
source vision_env/bin/activate
```

Check it:

``` bash
which python
which pip
python --version
```

Expected: - Python path inside `vision_env` - Pip path inside
`vision_env` - Python 3.11.x

## Upgrade packaging tools

``` bash
python -m pip install --upgrade pip setuptools wheel
```

## Install NumPy

``` bash
python -m pip install "numpy==1.26.4"
```

## Install OpenCV

``` bash
python -m pip install --only-binary=:all: "opencv-python==4.10.0.84"
```

## Install Jupyter

``` bash
python -m pip install jupyter ipykernel
```

## Install PyTorch (CPU ONLY)

⚠️ Important: prevents huge CUDA downloads

``` bash
python -m pip install torch torchvision torchaudio --index-url https://download.pytorch.org/whl/cpu
```

## Install Ultralytics

``` bash
python -m pip install ultralytics
```

## Install MediaPipe

``` bash
python -m pip install "protobuf<5,>=4.25.3" flatbuffers sounddevice sentencepiece absl-py "jax==0.4.38" "jaxlib==0.4.38" "ml-dtypes==0.5.4"
python -m pip install --no-deps "mediapipe==0.10.21"
```

## Install Facial Landmarks

``` bash
python -m pip install "git+https://github.com/ncguilbeault/facial-landmarks"
```

## Register Jupyter kernel

``` bash
python -m ipykernel install --user --name vision_env --display-name "Python (vision_env)"
```

## Verify installation

``` bash
python -c "import numpy as np; print('numpy ok', np.__version__)"
python -c "import cv2; print('cv2 ok', cv2.__version__)"
python -c "import torch; print('torch ok', torch.__version__)"
python -c "from ultralytics import YOLO; print('ultralytics ok')"
python -c "import mediapipe as mp; print('mediapipe ok', mp.__version__)"
python -c "import jupyter; import ipykernel; print('jupyter ok')"
```

## Open the project
- Open the `NoBlackBoxes` folder in VS Code.

###  Open the notebook
- Navigate to:

~/NoBlackBoxes/LastBlackBox/course/versions/ai-workshops/02_vision/_resources/chromebook/notebooks/01_images_and_cameras_V2_recorded.ipynb

## Run initial setup
- Run the first code cell.
- Follow the prompts to install required packages (Jupyter, Python).

## Select Python interpreter
- Open Command Palette:
  - `View → Command Palette`
- Search and select:
  - `Python: Select Interpreter`
- Choose **Enter interpreter path**, then select:

~/NoBlackBoxes/LastBlackBox/course/versions/ai-workshops/02_vision/_resources/chromebook/vision_env/bin/python
