NoBlackBoxes/LastBlackBox/boxes/fpgas/_resources/images/RISC-V_Instructions.png

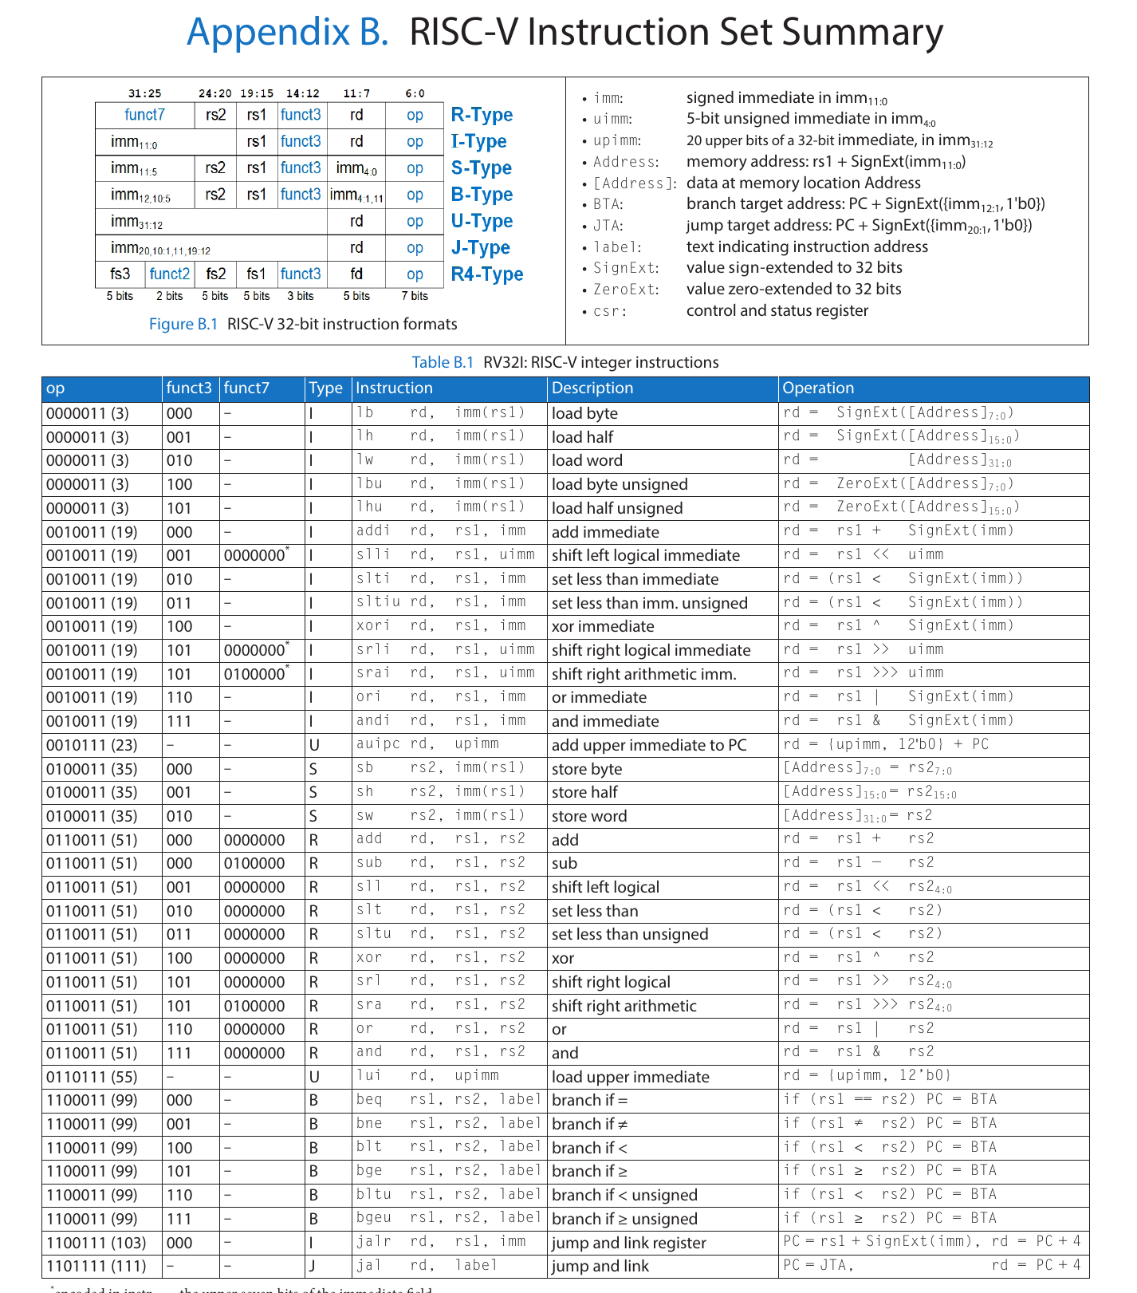
boxes/fpgas/_resources/images/RISC-V_Instructions.png
