NoBlackBoxes/LastBlackBox/boxes/ics/hdl/verilog/cpu/RISC-V Instructions.png

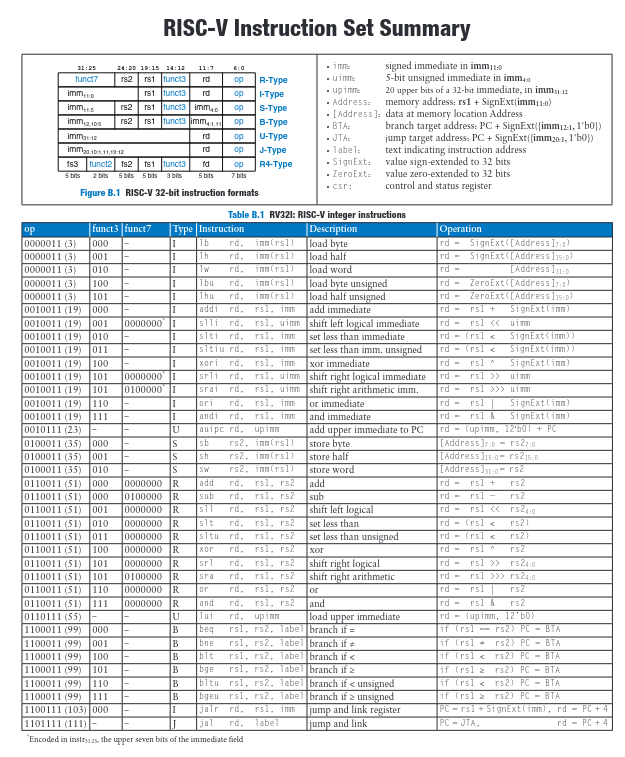
boxes/ics/hdl/verilog/cpu/RISC-V Instructions.png
