NoBlackBoxes/LastBlackBox/boxes/fpgas/hdl/verilog/cpu/modules/controller.v

// Controller (RV32I)
module controller(opcode, funct3, funct7b5, zero, result_select, memory_control, PC_select, ALU_select, reg_write, jump, ALU_control);

    // Declarations
    input [6:0] opcode;
    input [2:0] funct3;  
    input funct7b5;
    input zero;
    output [2:0] result_select;
    output [3:0] memory_control;
    output reg [1:0] PC_select;
    output ALU_select;
    output reg_write;
    output jump;
    output [3:0] ALU_control;
    
    // Intermediates
    wire [1:0] ALU_op;
    wire branch;
    
    // Main Decoder Sub-module
    main_decoder main_decoder
    (
        opcode,             // (input)
        funct3,             // (input)
        reg_write,          // (output)
        ALU_select,         // (output)
        memory_control,     // (output)
        result_select,      // (output)
        branch,             // (output)
        ALU_op,             // (output)
        jump                // (output)
    );
    
    // ALU Decoder Sub-module
    alu_decoder alu_decoder
    (
        opcode[5],      // (input) opcode_b5
        funct3,         // (input)
        funct7b5,       // (input)
        ALU_op,         // (input)
        ALU_control     // (output)
    );

    // Program Counter update for branch instructions
    always @*
        if(jump)
            case(opcode[3])
                1'b0: PC_select = 2'b10;            // jalr
                1'b1: PC_select = 2'b01;            // jal
                default: PC_select = 2'b01;
            endcase
        else
            case(funct3)
                3'b000: PC_select = branch & zero;   // beq
                3'b001: PC_select = branch & ~zero;  // bne
                3'b100: PC_select = branch & ~zero;  // blt
                3'b101: PC_select = branch & zero;   // bge
                3'b110: PC_select = branch & ~zero;  // bltu
                3'b111: PC_select = branch & zero;   // bgeu
                default: PC_select = 2'b00;
            endcase           
        
        // Compute memory offset for misaligned read/writes


endmodule
