NoBlackBoxes/LastBlackBox/boxes/systems/programming/baremetal/include/rpi-gpio.h

#ifndef RPI_GPIO_H
#define RPI_GPIO_H

/* The base address of the GPIO peripheral (ARM Physical Address) This is defined in the
   Peripherals manual provided by Broadcom and it differs between the different Raspberry Pi
   models */

/* This comes from the linux source code:
    https://github.com/raspberrypi/linux/blob/rpi-4.19.y/arch/arm/boot/dts/bcm2838.dtsi */
#define GPIO_BASE       0xFE200000UL

/* The RPi4 model has the ACT LED attached to GPIO 42
    https://github.com/raspberrypi/linux/blob/rpi-4.19.y/arch/arm/boot/dts/bcm2838-rpi-4-b.dts */
#define LED_GPFSEL      GPIO_GPFSEL4
#define LED_GPFBIT      6
#define LED_GPSET       GPIO_GPSET1
#define LED_GPCLR       GPIO_GPCLR1
#define LED_GPIO_BIT    10


#define GPIO_GPFSEL0    0
#define GPIO_GPFSEL1    1
#define GPIO_GPFSEL2    2
#define GPIO_GPFSEL3    3
#define GPIO_GPFSEL4    4
#define GPIO_GPFSEL5    5

#define GPIO_GPSET0     7
#define GPIO_GPSET1     8

#define GPIO_GPCLR0     10
#define GPIO_GPCLR1     11

#define GPIO_GPLEV0     13
#define GPIO_GPLEV1     14

#define GPIO_GPEDS0     16
#define GPIO_GPEDS1     17

#define GPIO_GPREN0     19
#define GPIO_GPREN1     20

#define GPIO_GPFEN0     22
#define GPIO_GPFEN1     23

#define GPIO_GPHEN0     25
#define GPIO_GPHEN1     26

#define GPIO_GPLEN0     28
#define GPIO_GPLEN1     29

#define GPIO_GPAREN0    31
#define GPIO_GPAREN1    32

#define GPIO_GPAFEN0    34
#define GPIO_GPAFEN1    35

#define GPIO_GPPUD      37
#define GPIO_GPPUDCLK0  38
#define GPIO_GPPUDCLK1  39

#endif
