NoBlackBoxes/LastBlackBox/course/_resources/videos/obs/NoBlackBox_Profile/basic.ini

[General]
Name=NoBlackBox Profile

[Video]
BaseCX=1920
BaseCY=1080
OutputCX=1920
OutputCY=1080
FPSType=0
FPSCommon=30
FPSInt=30
FPSNum=30
FPSDen=1
ScaleType=bicubic
ColorFormat=NV12
ColorSpace=709
ColorRange=Partial
SdrWhiteLevel=300
HdrNominalPeakLevel=1000

[Panels]
CookieId=A78EFA69782FCF5C

[SimpleOutput]
RecEncoder=x264
RecQuality=Small
FilePath=/home/kampff
RecFormat2=mkv
VBitrate=2500
ABitrate=160
UseAdvanced=false
Preset=veryfast
NVENCPreset2=p5
RecRB=false
RecRBTime=20
RecRBSize=512
RecRBPrefix=Replay
StreamAudioEncoder=aac
RecAudioEncoder=aac
RecTracks=1
StreamEncoder=x264

[Output]
Mode=Advanced
FilenameFormatting=%CCYY-%MM-%DD %hh-%mm-%ss
DelayEnable=false
DelaySec=20
DelayPreserve=true
Reconnect=true
RetryDelay=2
MaxRetries=25
BindIP=default
IPFamily=IPv4+IPv6
NewSocketLoopEnable=false
LowLatencyEnable=false

[AdvOut]
TrackIndex=1
RecType=Standard
RecFilePath=/home/kampff/Videos
RecEncoder=ffmpeg_vaapi
RecTracks=1
FLVTrack=1
FFOutputToFile=true
FFFormat=
FFFormatMimeType=
FFVEncoderId=0
FFVEncoder=
FFAEncoderId=0
FFAEncoder=
FFAudioMixes=1
VodTrackIndex=2
RecFileNameWithoutSpace=true
RecSplitFileType=Time
ApplyServiceSettings=true
UseRescale=false
Encoder=obs_x264
RecFormat2=mkv
RecUseRescale=false
FFFilePath=/home/kampff
FFVBitrate=2500
FFVGOPSize=250
FFUseRescale=false
FFIgnoreCompat=false
FFABitrate=160
Track1Bitrate=320
Track2Bitrate=320
Track3Bitrate=320
Track4Bitrate=320
Track5Bitrate=320
Track6Bitrate=320
RecSplitFileTime=15
RecSplitFileSize=2048
RecRB=false
RecRBTime=20
RecRBSize=512
AudioEncoder=libfdk_aac
RecAudioEncoder=libfdk_aac
StreamMultiTrackAudioMixes=1

[Stream1]
IgnoreRecommended=false
EnableMultitrackVideo=false
MultitrackVideoMaximumAggregateBitrateAuto=true
MultitrackVideoMaximumVideoTracksAuto=true

[Audio]
MonitoringDeviceId=default
MonitoringDeviceName=Default
SampleRate=48000
ChannelSetup=Stereo
MeterDecayRate=23.53
PeakMeterType=0
