NoBlackBoxes/LastBlackBox/boxes/fpgas/hdl/vhdl/hello/hello.vhdl

use std.textio.all; 

-- Design entity, no ports
entity hello_world is
end hello_world;

architecture behaviour of hello_world is
begin
  process
    variable l : line;
  begin
    write (l, String'("Hello world!"));
    writeline (output, l);
    wait;
  end process;
end behaviour;
