NoBlackBoxes/LastBlackBox/boxes/networks/serial_protocol/python/rgb_scroll/rgb_scroll.py

import serial
import time

# Open serial port
ser = serial.Serial(port='/dev/ttyUSB0', baudrate=115200)
time.sleep(2.00) # Wait for connection before sending any data


# Send a RGB commands
for i in range(10):
    intensities = list(range(0,255,15)) + list(range(255,0,-15))
    for r in intensities:
        command = f"r:{r:03d}\n"
        ser.write(command.encode())
        #print(command.encode())
        time.sleep(0.02)
    for g in intensities:
        command = f"g:{g:03d}\n"
        #print(command.encode())
        ser.write(command.encode())
        time.sleep(0.02)
    for b in intensities:
        command = f"b:{b:03d}\n"
        #print(command.encode())
        ser.write(command.encode())
        time.sleep(0.02)

# Close serial port
ser.close()

#FIN
