NoBlackBoxes/LastBlackBox/boxes/systems/NBBOS/level_0/include/framebuffer.h

#pragma once
#include "common.h"

// Declarations
void framebuffer_init();
void framebuffer_clear();
void framebuffer_fill_naive(char r, char g, char b);
void framebuffer_fill(char r, char g, char b);
