NoBlackBoxes/LastBlackBox/course/versions/ai-workshops/01_audio/_resources/python/nb3_config.py

"""
NB3 configuration for voice and LLM.

Edit these values to change the robot's voice and brain
everywhere (00, 02, and demo.py).
"""

# ElevenLabs voice and TTS model
VOICE_ID = "21m00Tcm4TlvDq8ikWAM"
TTS_MODEL_ID = "eleven_turbo_v2_5"

# OpenAI LLM model and default system prompt
LLM_MODEL = "gpt-4.1-mini"
SYSTEM_PROMPT = "You are a friendly robot teacher. Reply in one short sentence."
